thereprocase/dell-5560-wall-mount/docs/assets/after-fin.png

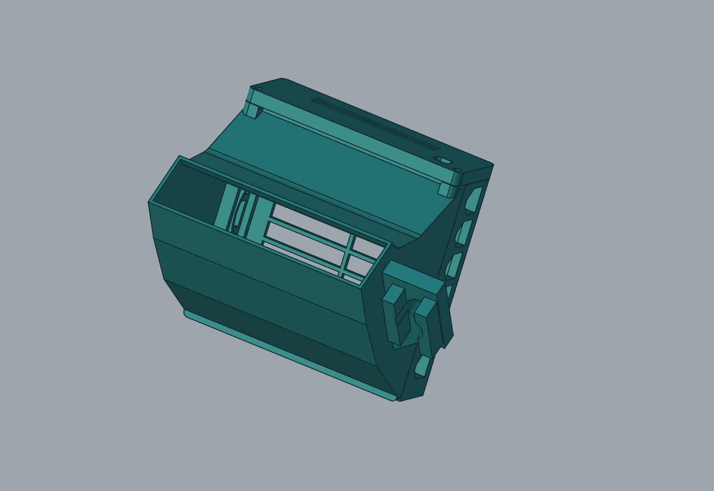
docs/assets/after-fin.png
