thereprocase/dell-5560-wall-mount/docs/assets/after-shoulder.png

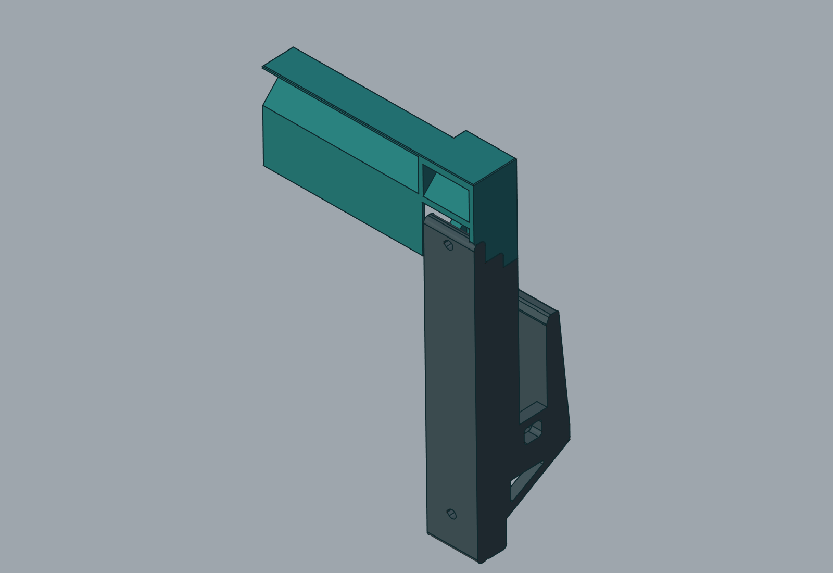
docs/assets/after-shoulder.png
