thereprocase/dell-5560-wall-mount/docs/assets/before-fin.png

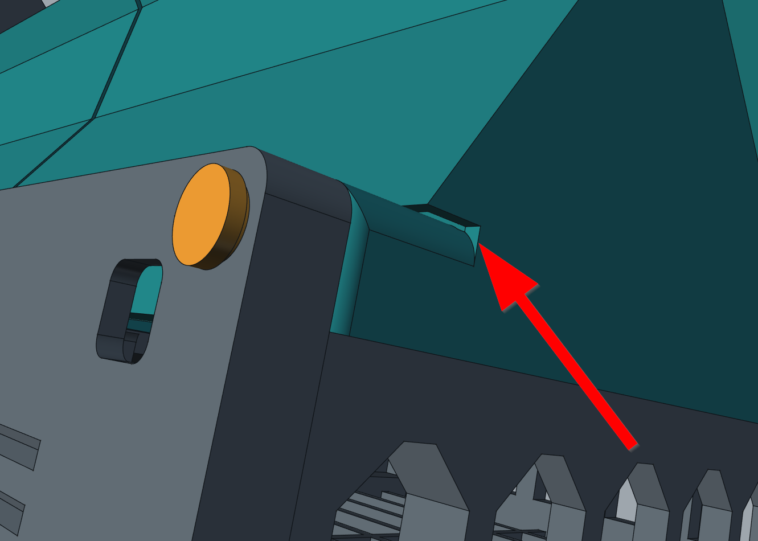
docs/assets/before-fin.png
