thereprocase/dell-5560-wall-mount/docs/assets/before-shoulder.png

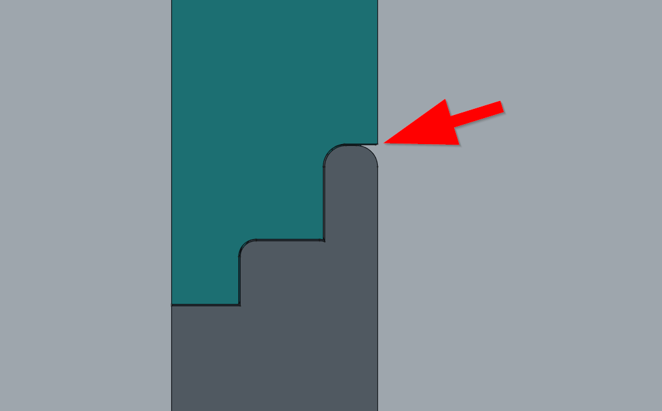
docs/assets/before-shoulder.png
