thereprocase/dell-5560-wall-mount/docs/assets/before-tray.png

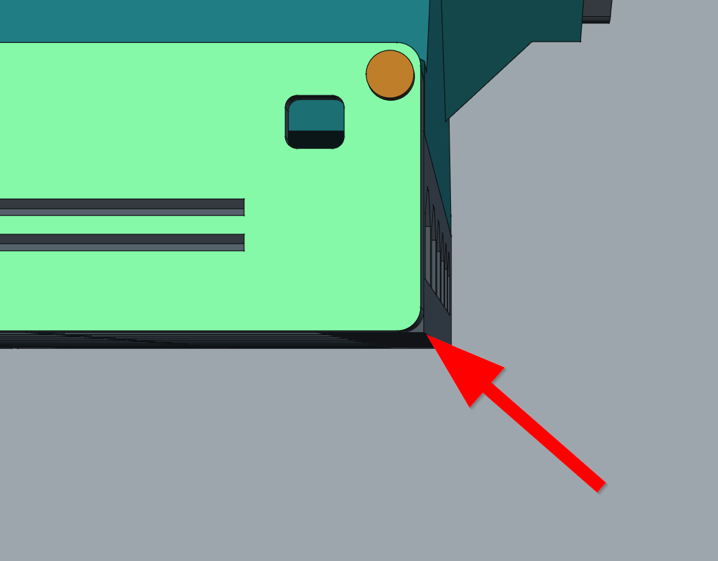
docs/assets/before-tray.png
