thereprocase/dell-5560-wall-mount/docs/assets/cap.png

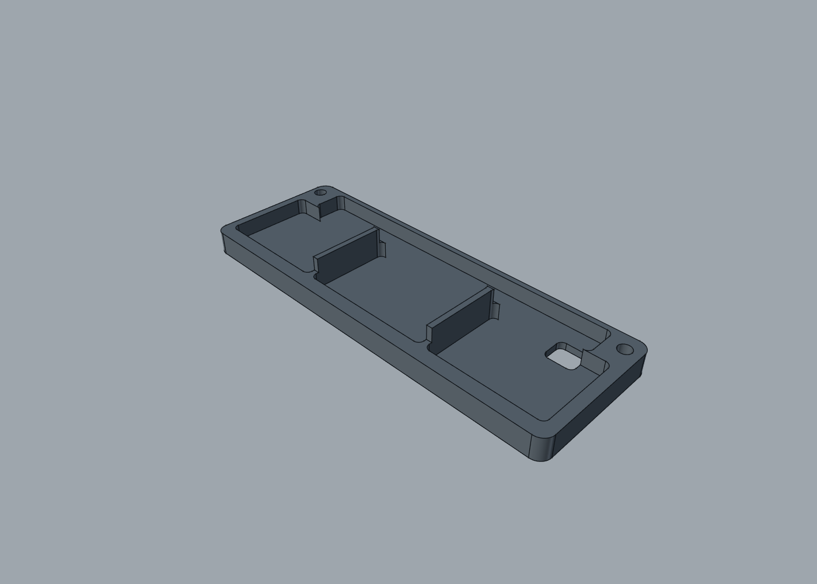
docs/assets/cap.png
