thereprocase/dell-5560-wall-mount/docs/assets/cfd-mesh.png

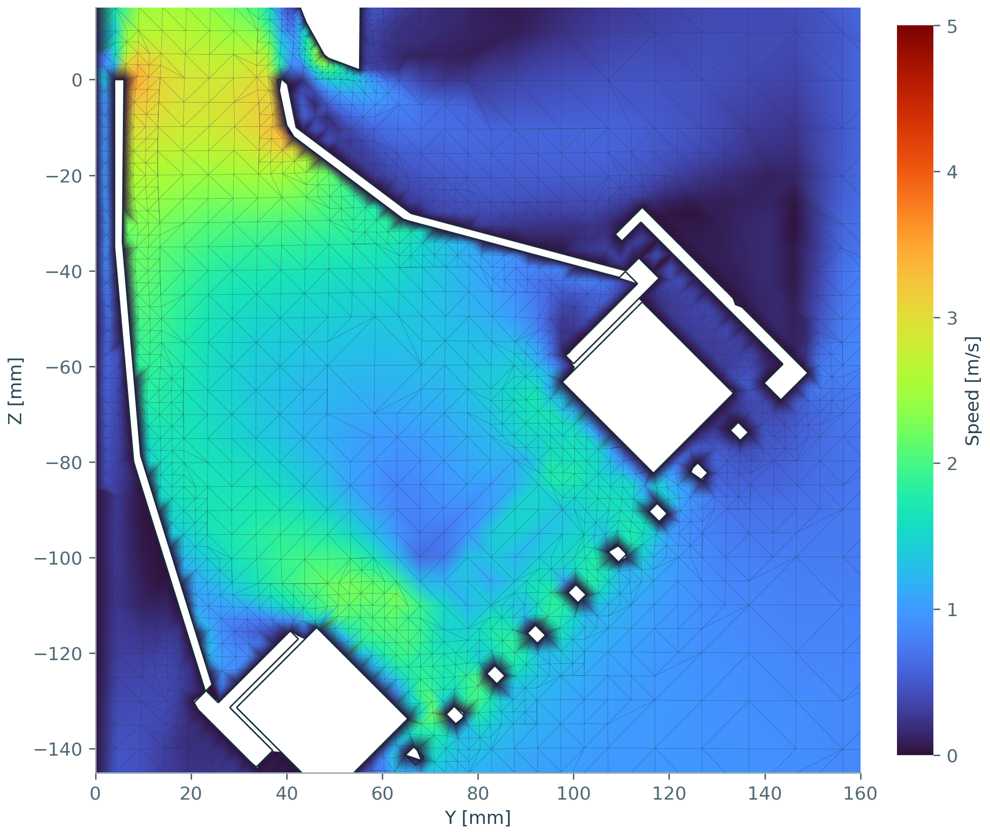
docs/assets/cfd-mesh.png
