thereprocase/dell-5560-wall-mount/docs/assets/cfd-pressure.png

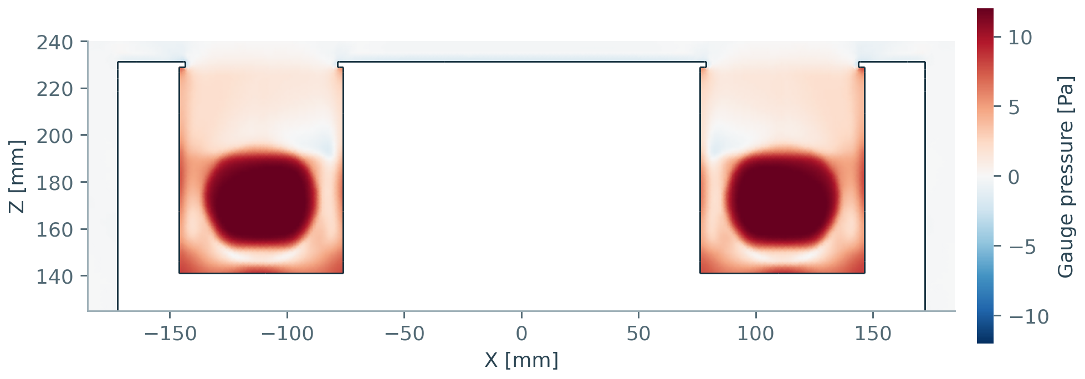
docs/assets/cfd-pressure.png
