thereprocase/dell-5560-wall-mount/docs/assets/cfd-residuals.png

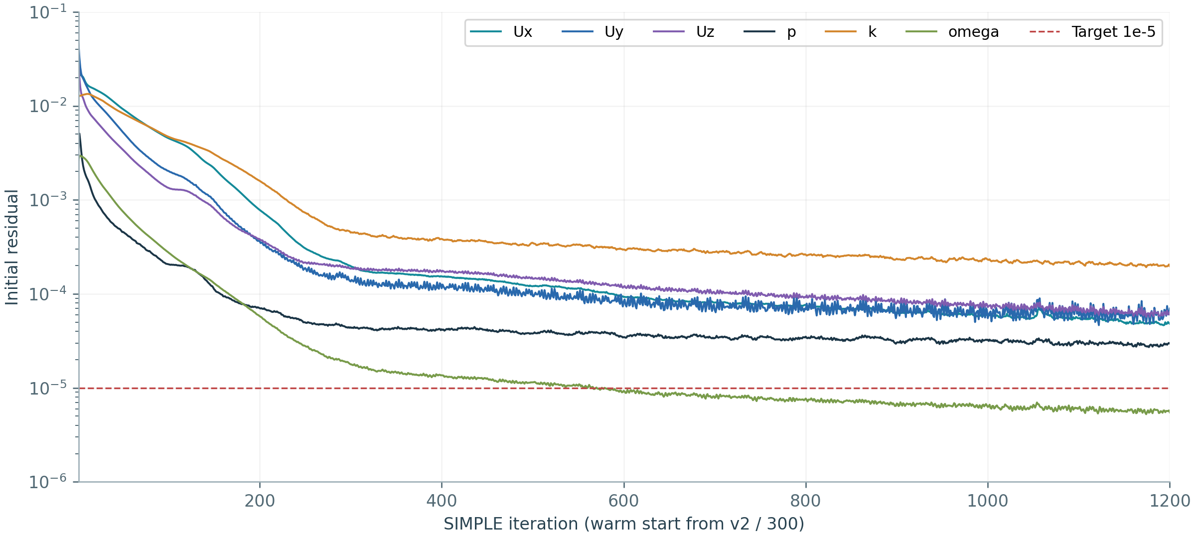
docs/assets/cfd-residuals.png
