thereprocase/dell-5560-wall-mount/docs/assets/cfd-speed.png

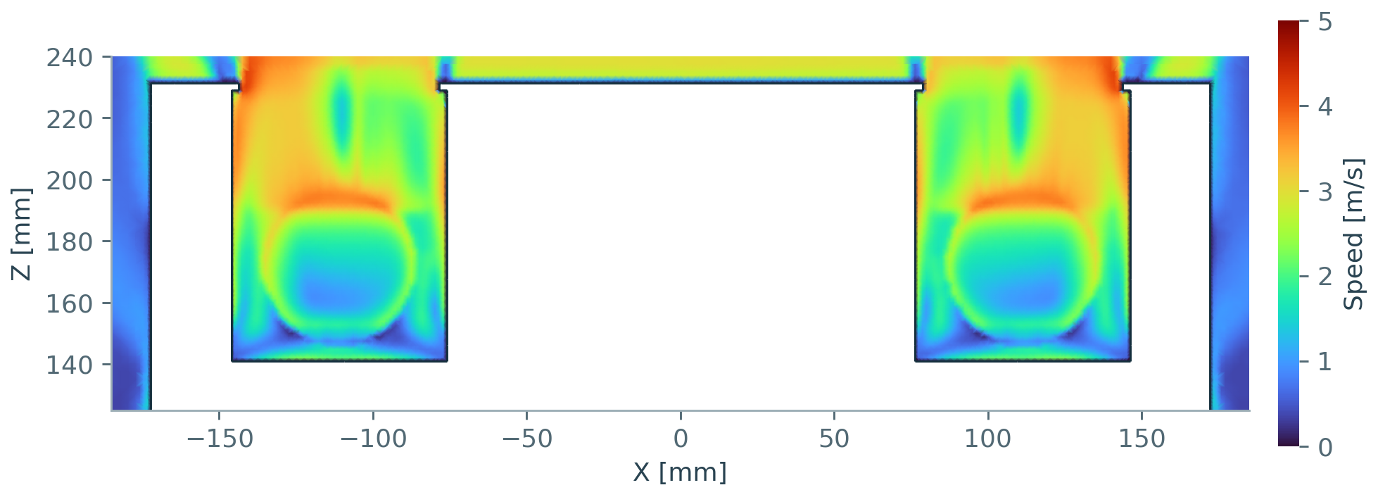
docs/assets/cfd-speed.png
