thereprocase/dell-5560-wall-mount/docs/assets/cfd-streamlines.png

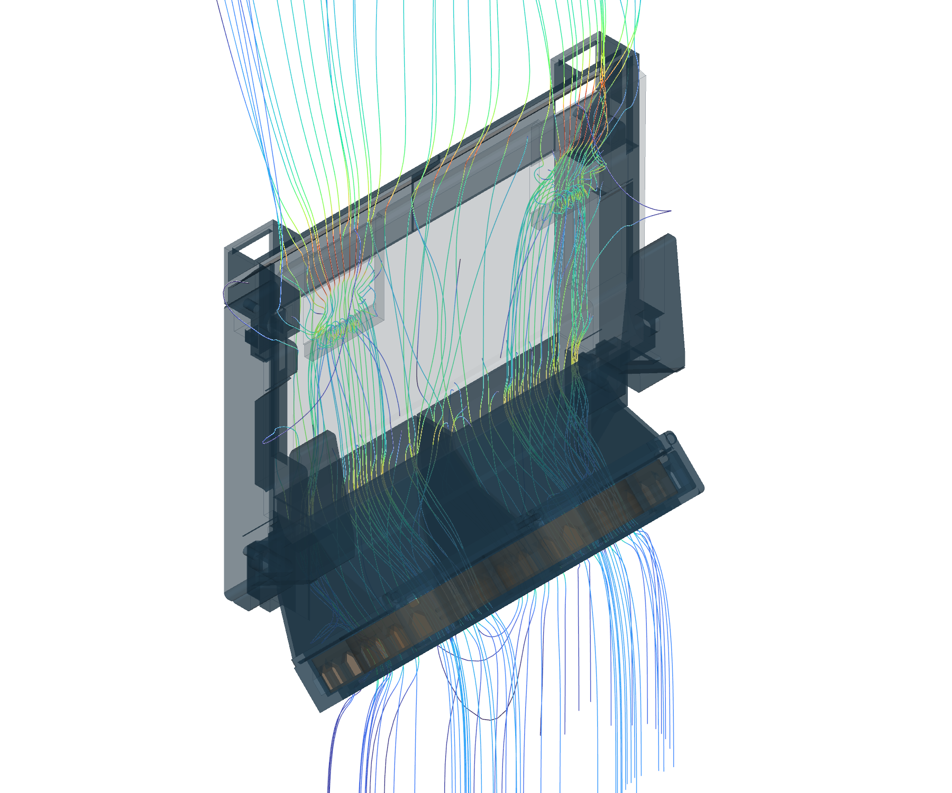
docs/assets/cfd-streamlines.png
