thereprocase/dell-5560-wall-mount/docs/assets/duct.png

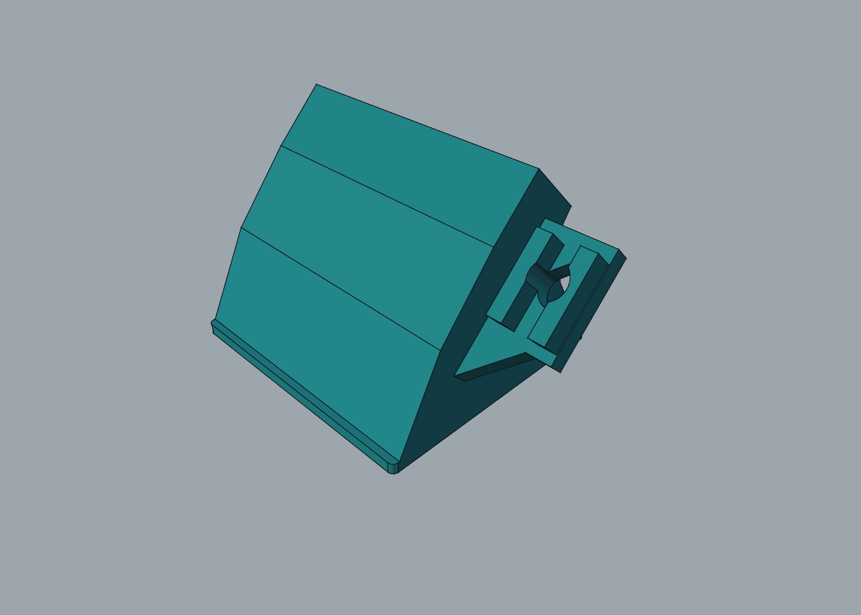
docs/assets/duct.png
