thereprocase/dell-5560-wall-mount/docs/assets/flow-refinement.png

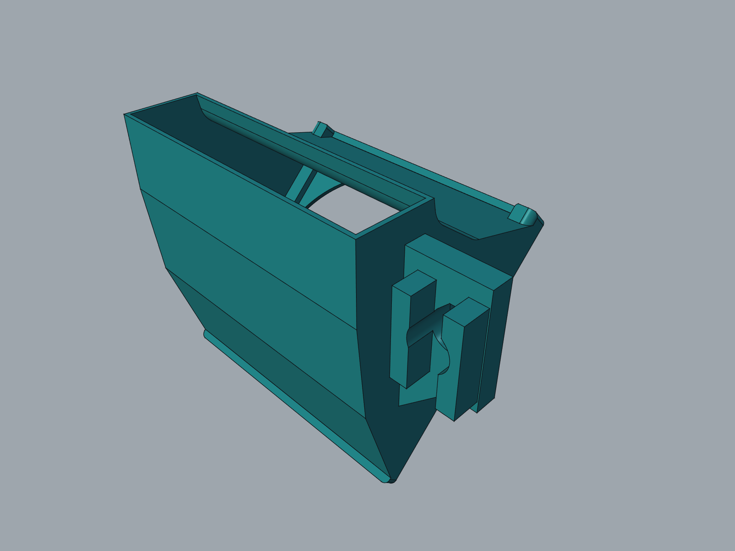
docs/assets/flow-refinement.png
