thereprocase/dell-5560-wall-mount/docs/assets/minimalist-cage-toolpaths.png

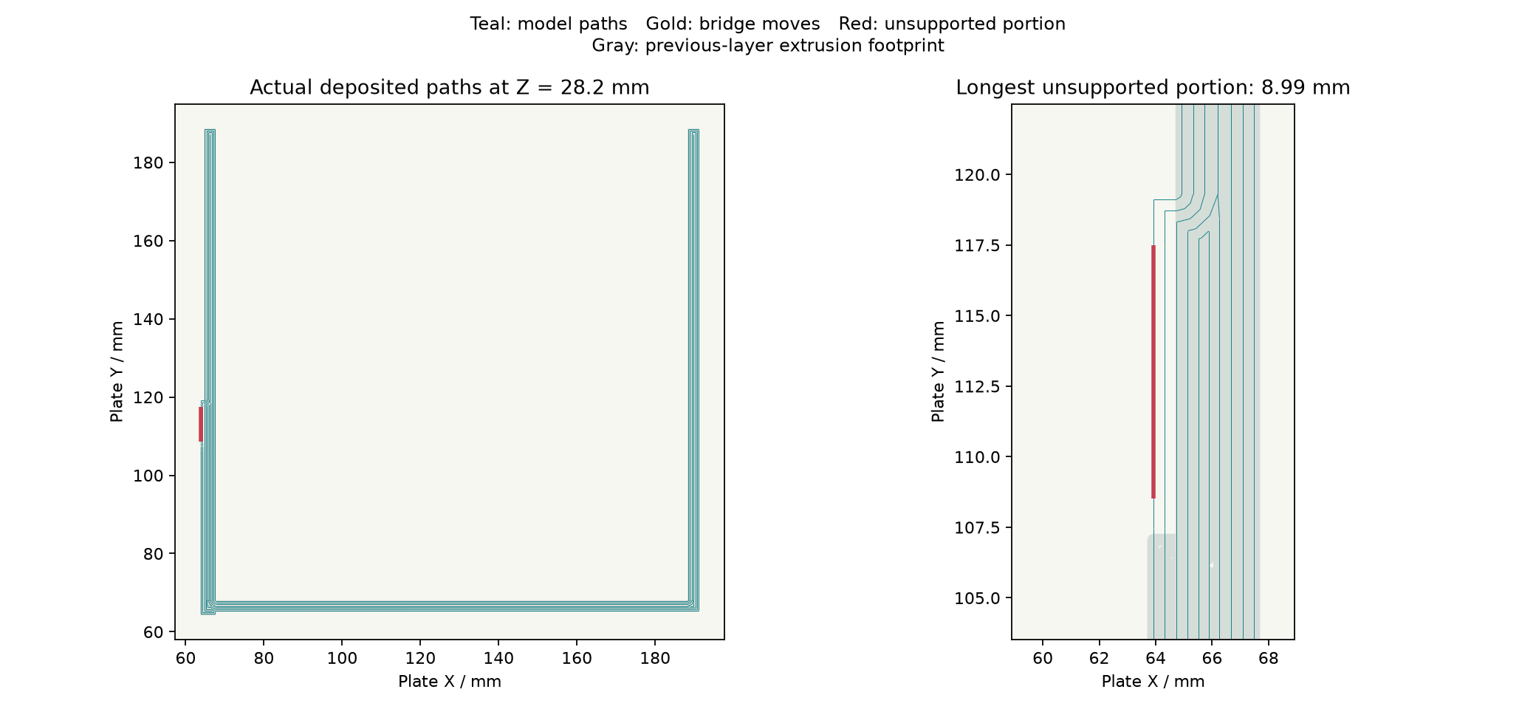
docs/assets/minimalist-cage-toolpaths.png
