thereprocase/dell-5560-wall-mount/docs/assets/minimalist-native.png

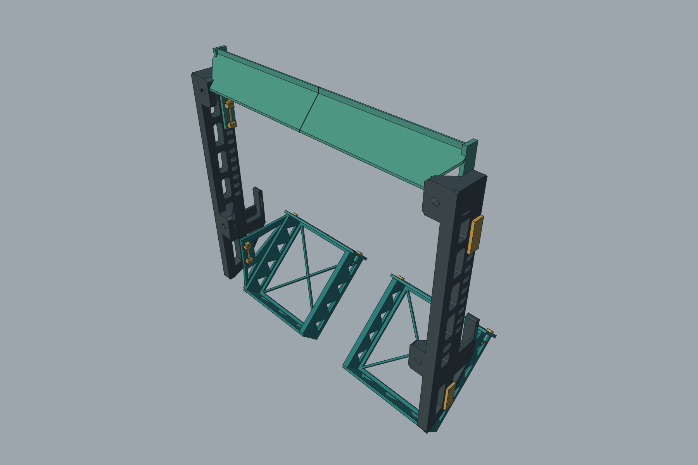
docs/assets/minimalist-native.png
