thereprocase/dell-5560-wall-mount/docs/assets/minimalist-with-envelopes.png

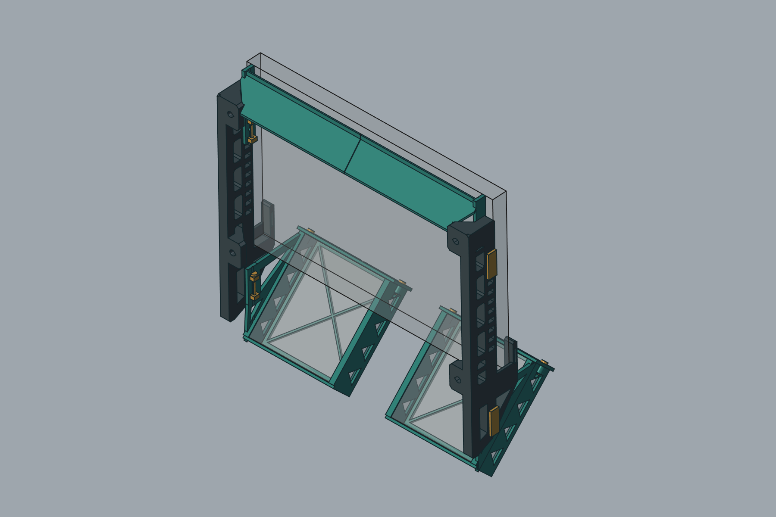
docs/assets/minimalist-with-envelopes.png
