thereprocase/dell-5560-wall-mount/docs/assets/parameters.png

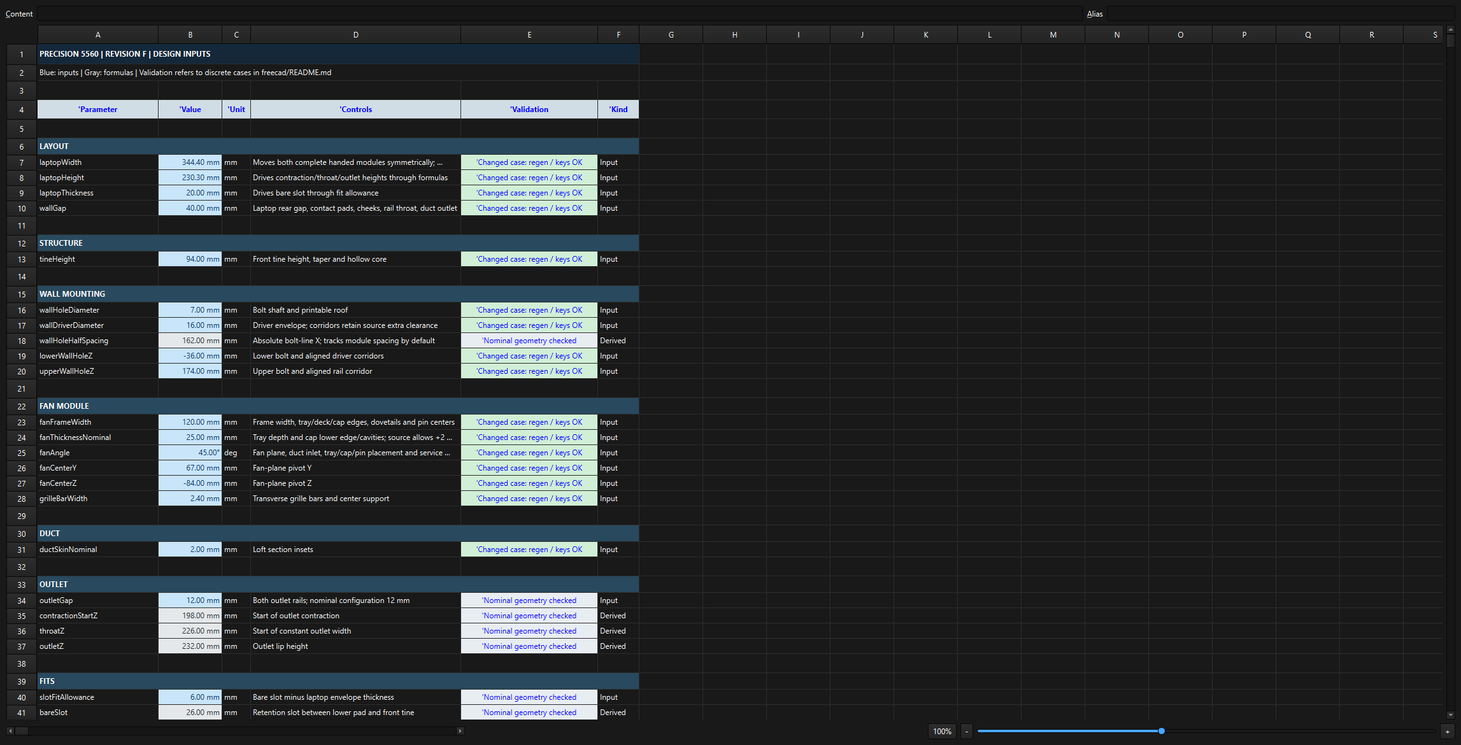
docs/assets/parameters.png
