thereprocase/dell-5560-wall-mount/docs/assets/pin.png

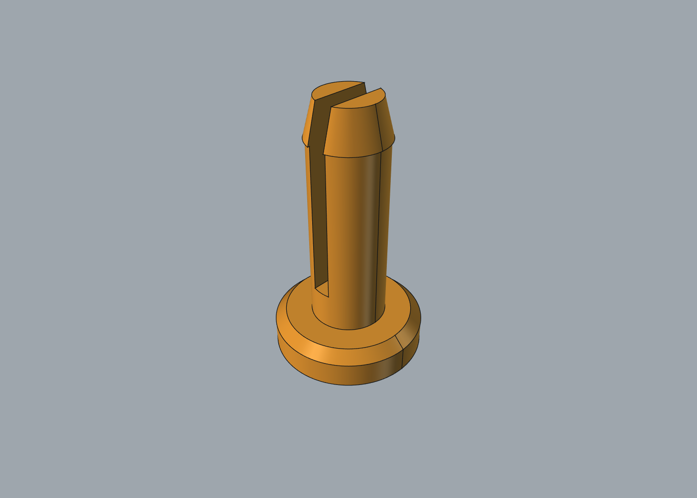
docs/assets/pin.png
