thereprocase/dell-5560-wall-mount/docs/assets/rail.png

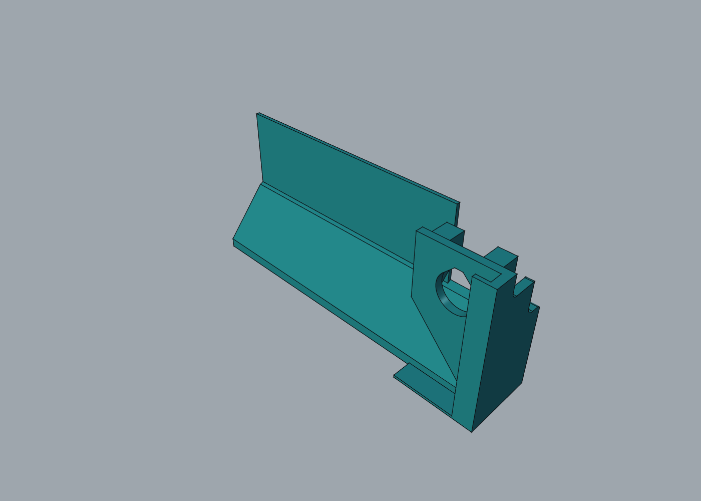
docs/assets/rail.png
