thereprocase/dell-5560-wall-mount/docs/assets/revh-cables-coupon.png

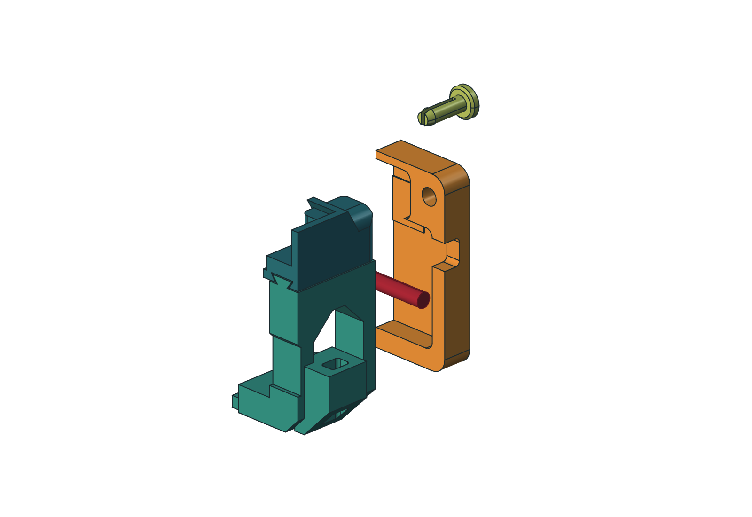
docs/assets/revh-cables-coupon.png
