thereprocase/dell-5560-wall-mount/docs/assets/revh-cables-toolpaths.png

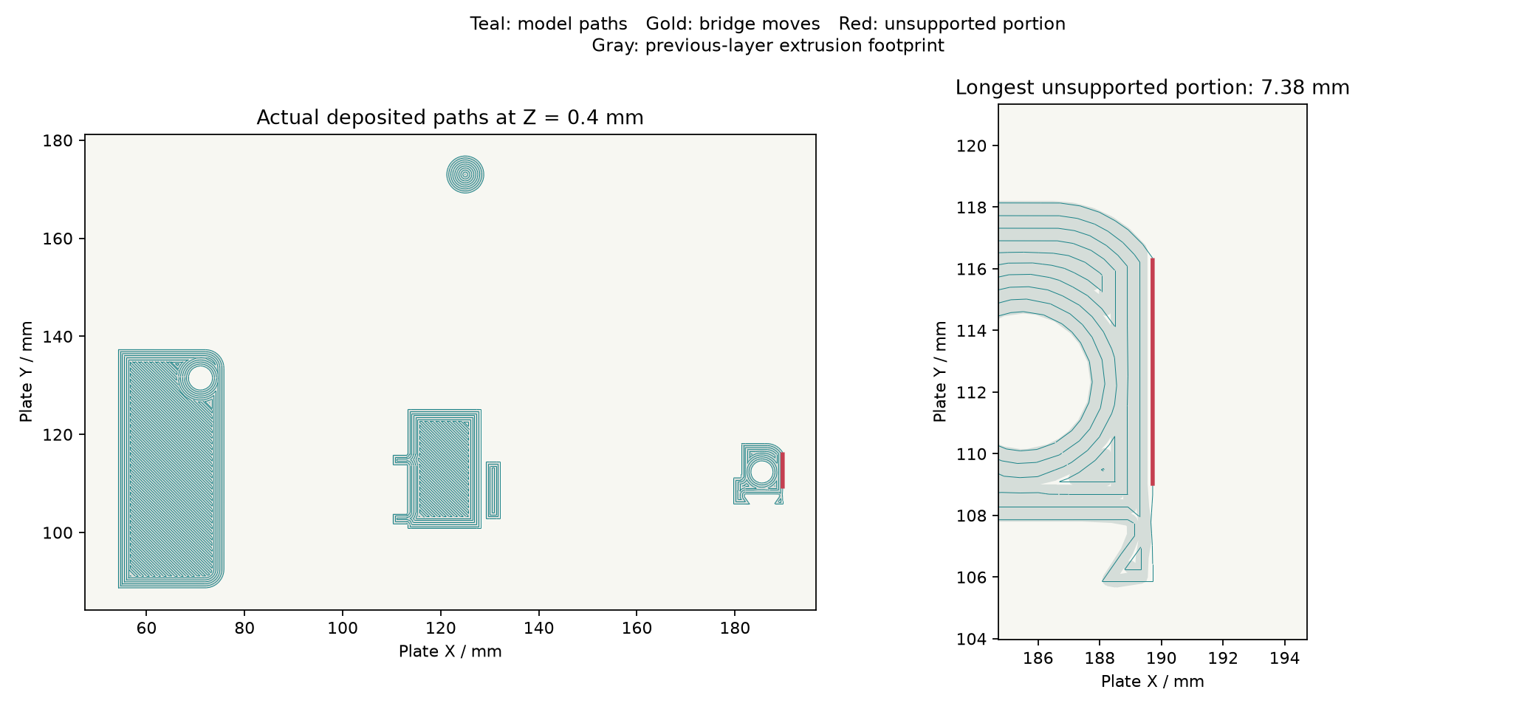
docs/assets/revh-cables-toolpaths.png
