thereprocase/dell-5560-wall-mount/docs/assets/revh-cables-tray.png

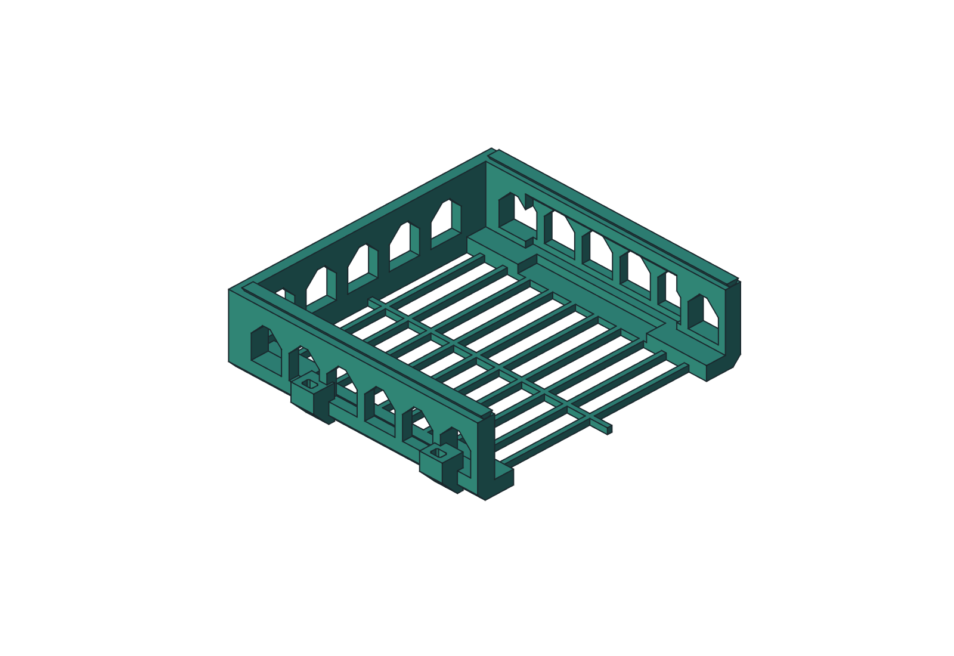
docs/assets/revh-cables-tray.png
