thereprocase/dell-5560-wall-mount/docs/assets/revh-duct-d4-pin-hole-obstruction.png

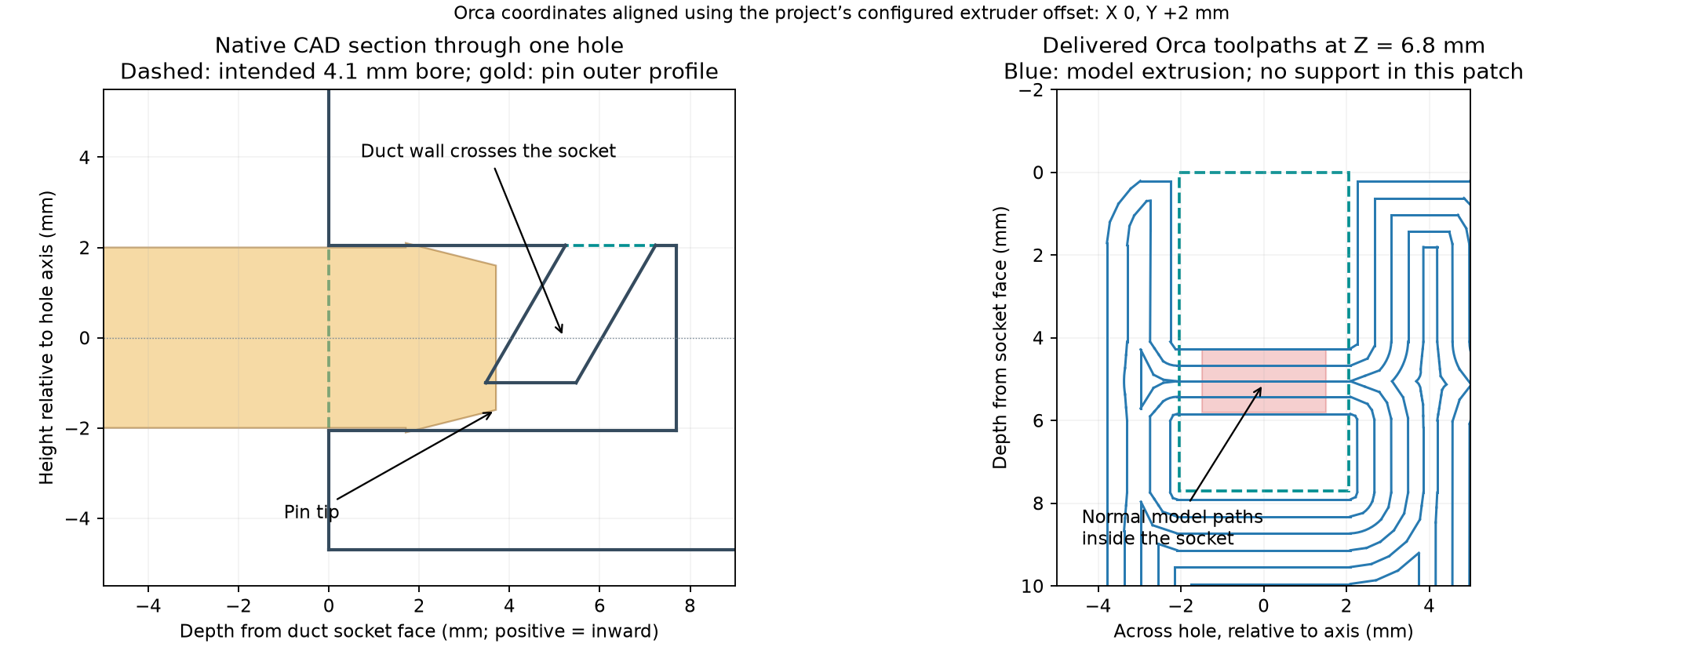
docs/assets/revh-duct-d4-pin-hole-obstruction.png
