thereprocase/dell-5560-wall-mount/docs/assets/revh-duct-d4-socket-before-after.png

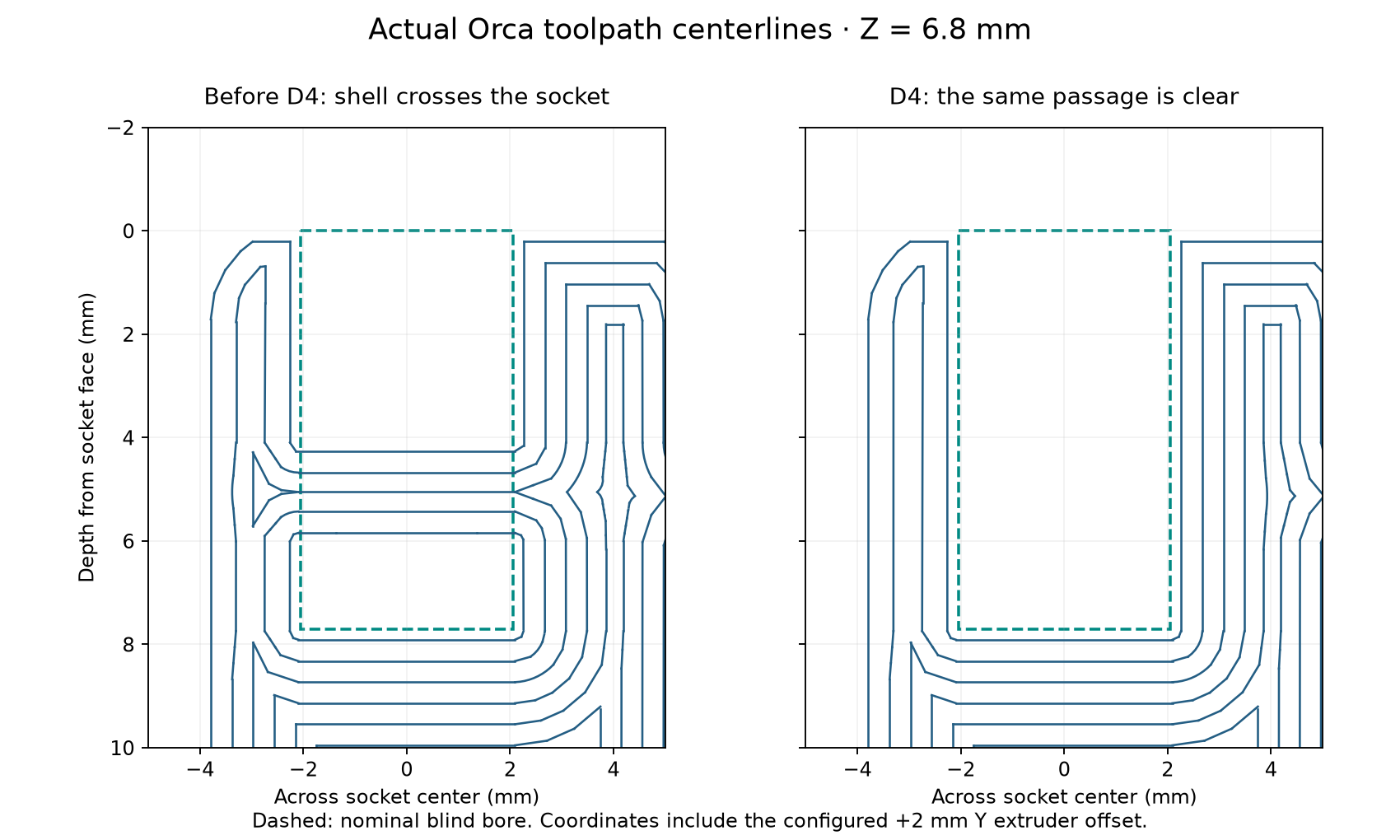
docs/assets/revh-duct-d4-socket-before-after.png
