thereprocase/dell-5560-wall-mount/docs/assets/revh-orca-left-cross-slot-audit.png

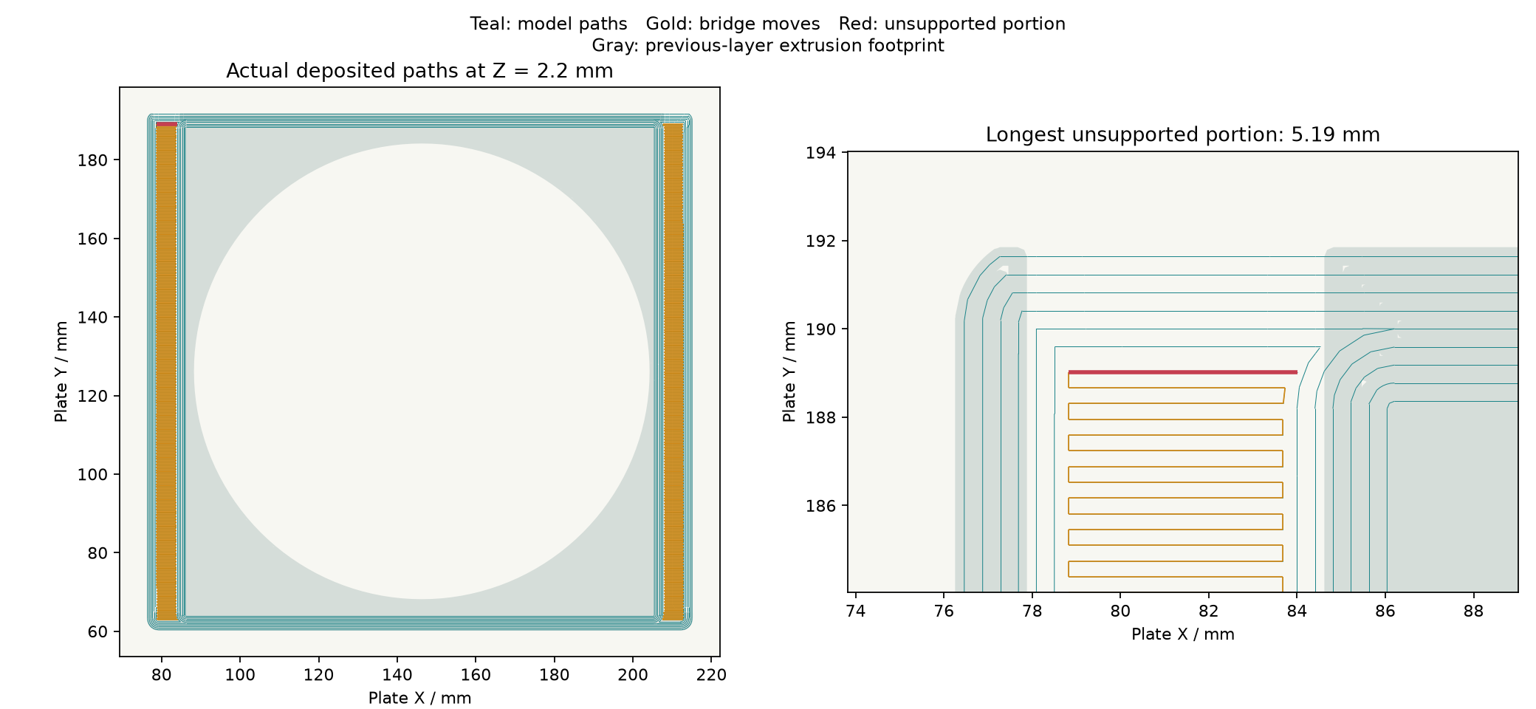
docs/assets/revh-orca-left-cross-slot-audit.png
