thereprocase/dell-5560-wall-mount/docs/assets/revh-retainers-lower.png

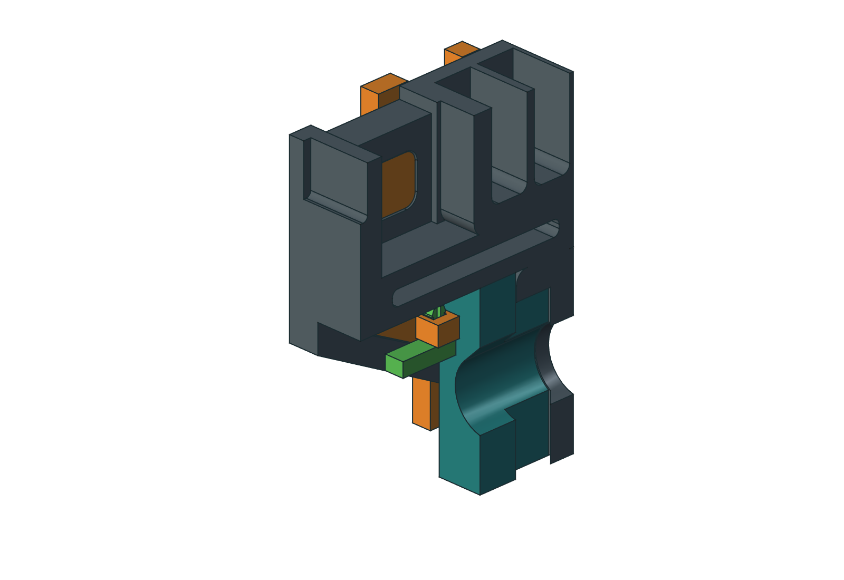
docs/assets/revh-retainers-lower.png
