thereprocase/dell-5560-wall-mount/docs/assets/revh-retainers-removed.png

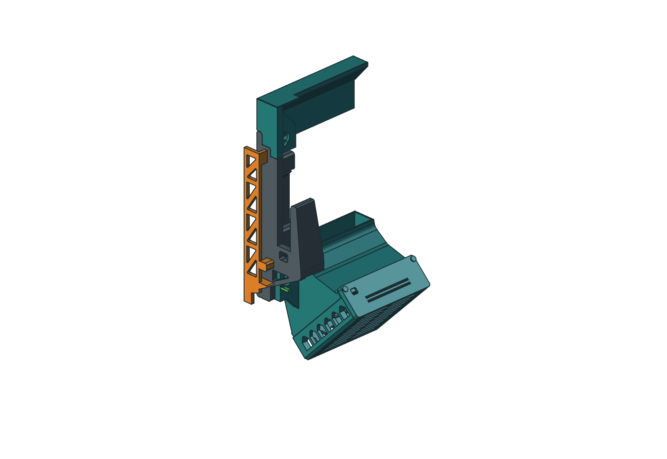
docs/assets/revh-retainers-removed.png
