thereprocase/dell-5560-wall-mount/docs/assets/revh-retainers-toolpaths.png

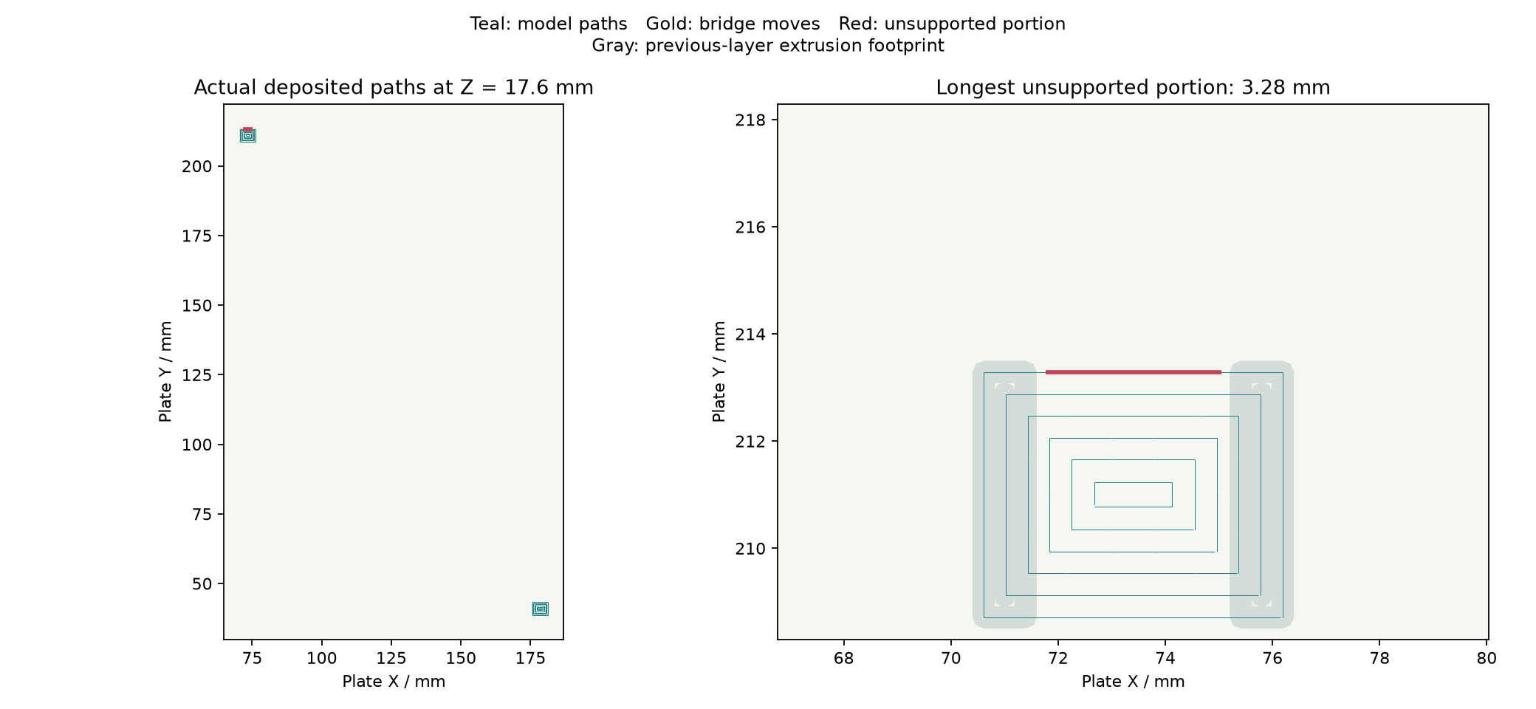
docs/assets/revh-retainers-toolpaths.png
