thereprocase/dell-5560-wall-mount/docs/assets/revh-retainers-upper.png

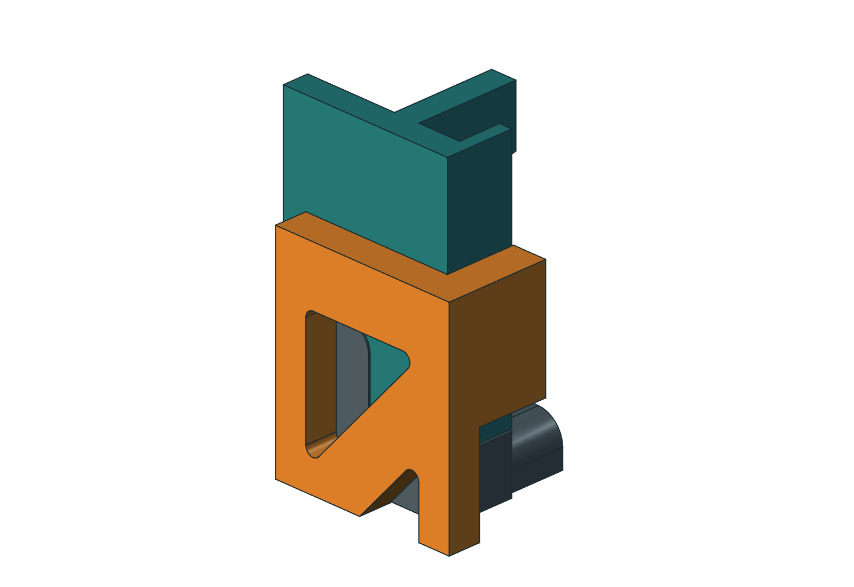
docs/assets/revh-retainers-upper.png
