thereprocase/dell-5560-wall-mount/docs/assets/tray.png

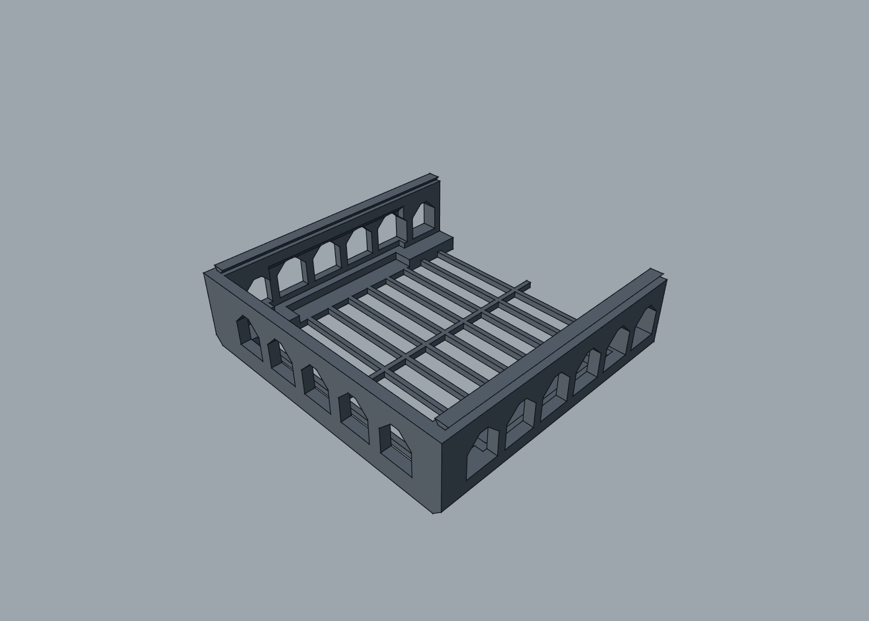
docs/assets/tray.png
