thereprocase/dell-5560-wall-mount/docs/assets/wall-patch.png

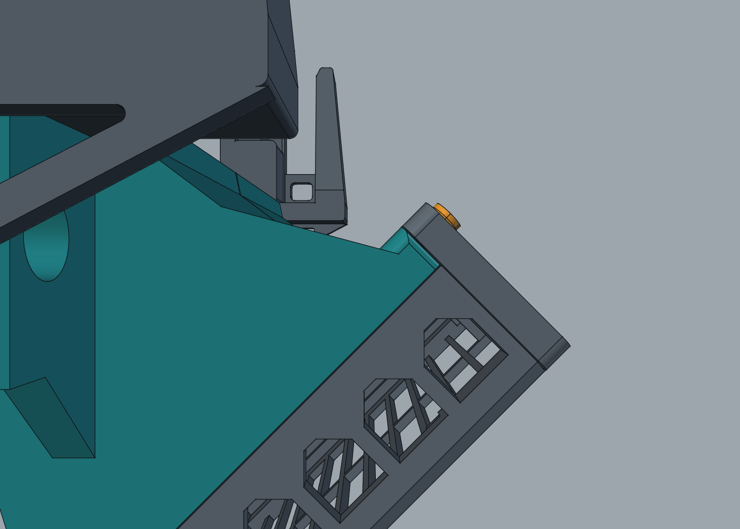
docs/assets/wall-patch.png
