thereprocase/dell-5560-wall-mount/docs/simulation/revh-transient/mesh-duct-overview.png

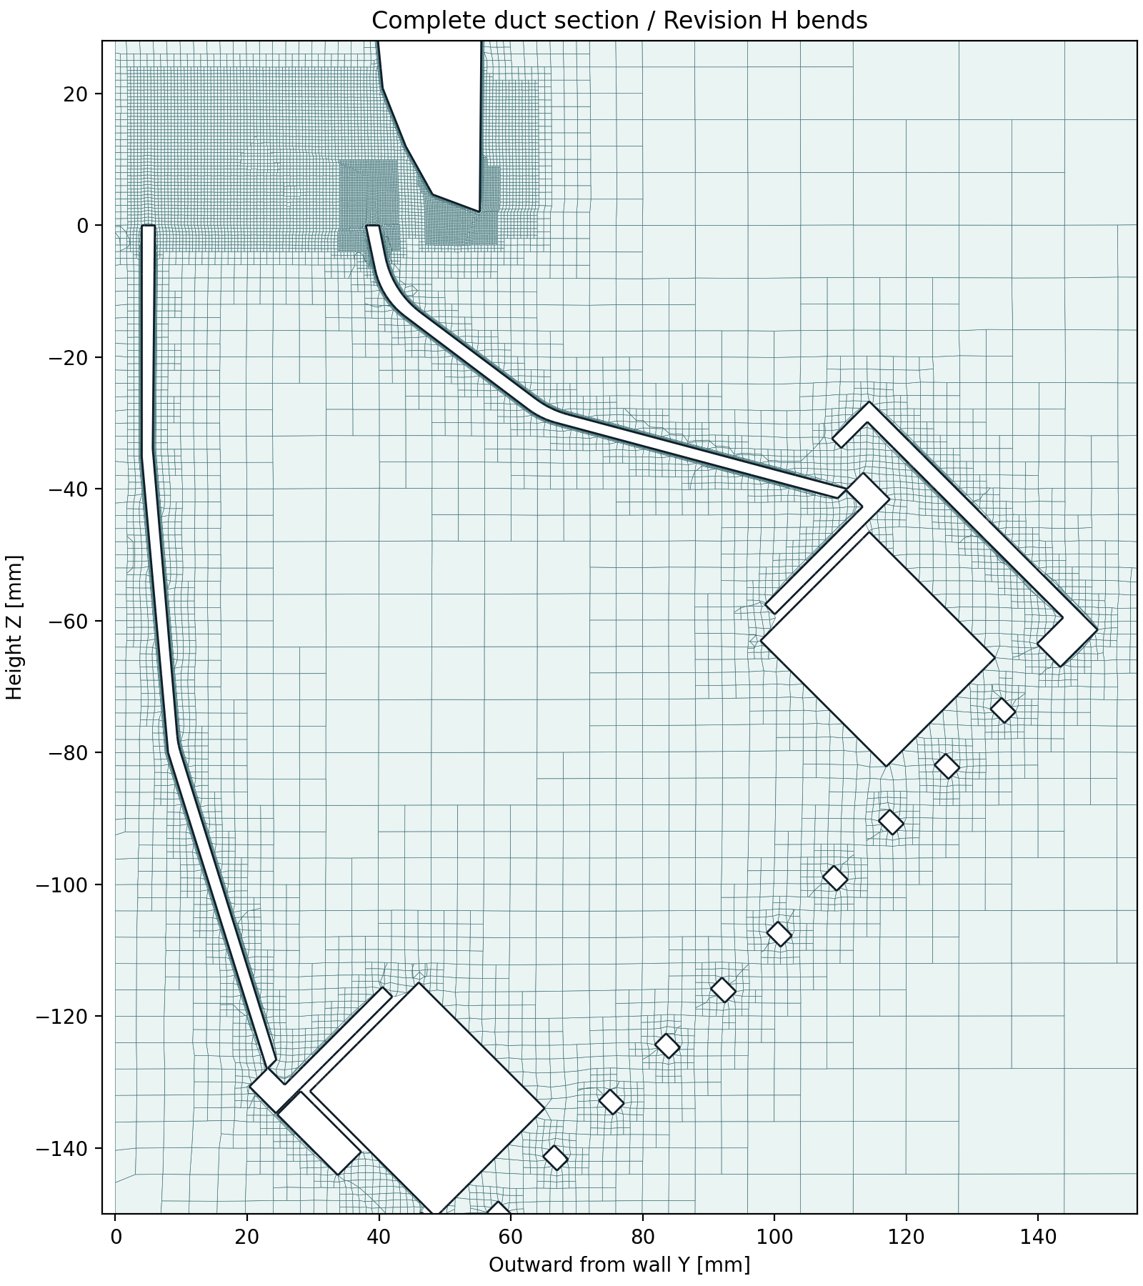
docs/simulation/revh-transient/mesh-duct-overview.png
