thereprocase/dell-5560-wall-mount/docs/simulation/revh-transient/pilot-sections-poster.png

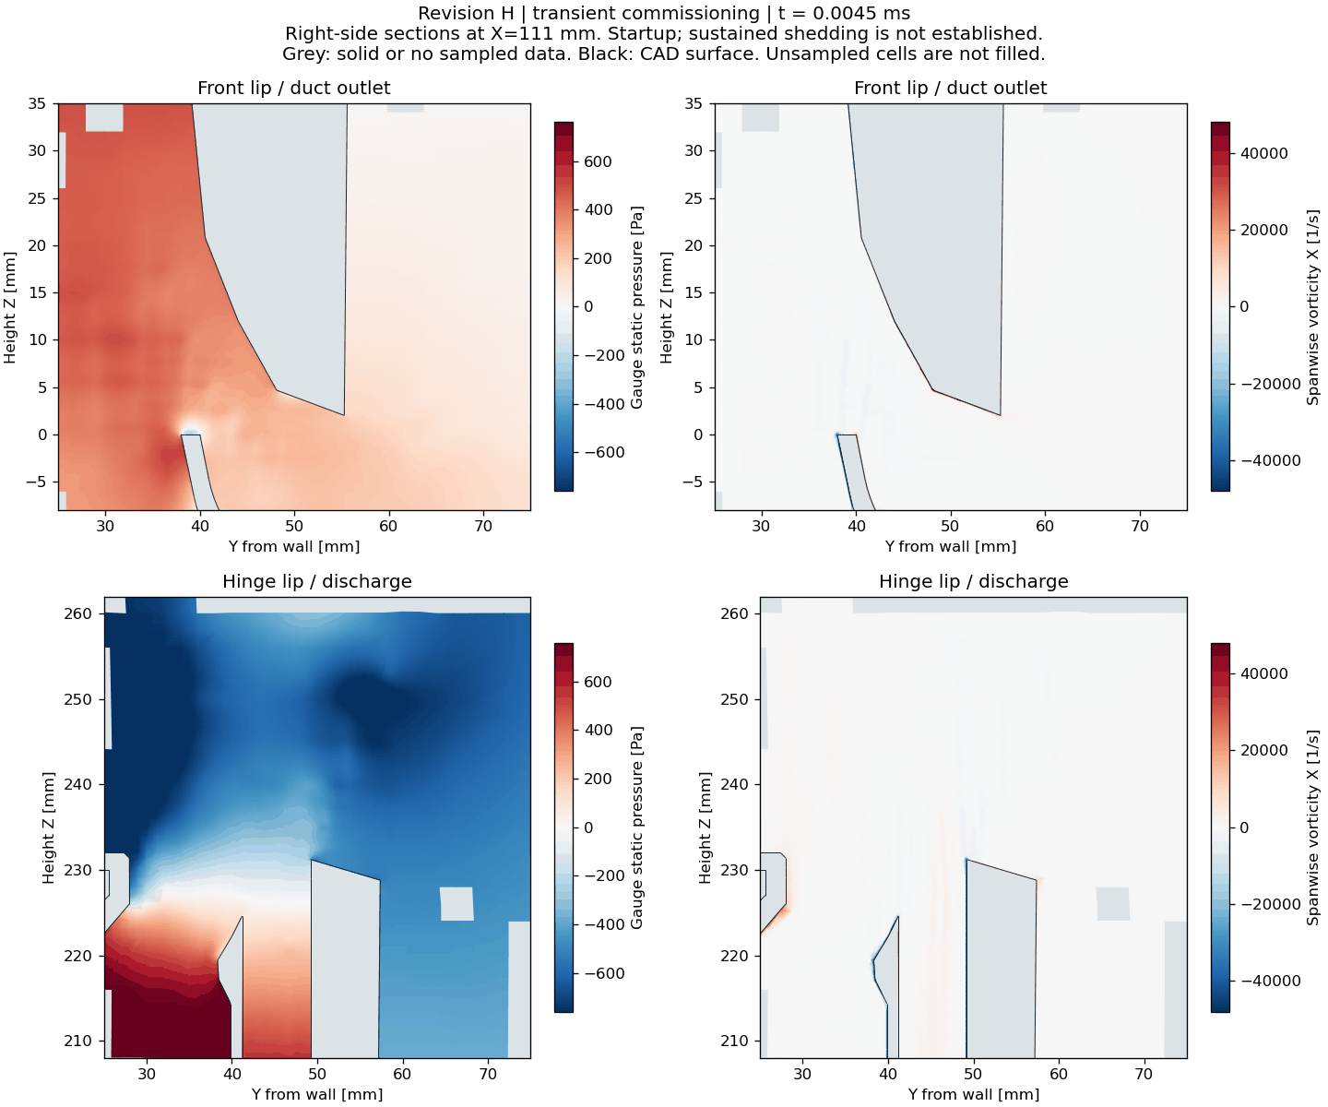
docs/simulation/revh-transient/pilot-sections-poster.png
