thereprocase/dell-5560-wall-mount/docs/simulation/revh-transient/section-locator.png

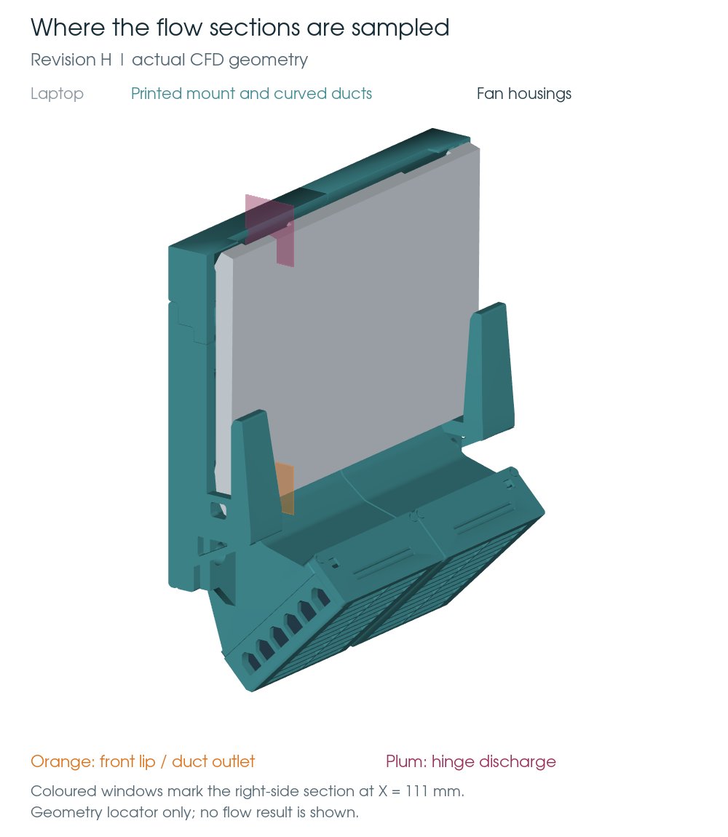
docs/simulation/revh-transient/section-locator.png
