thereprocase/dell-5560-wall-mount/docs/simulation/revh-transient/sequence/checkpoint-01/first-frame.png

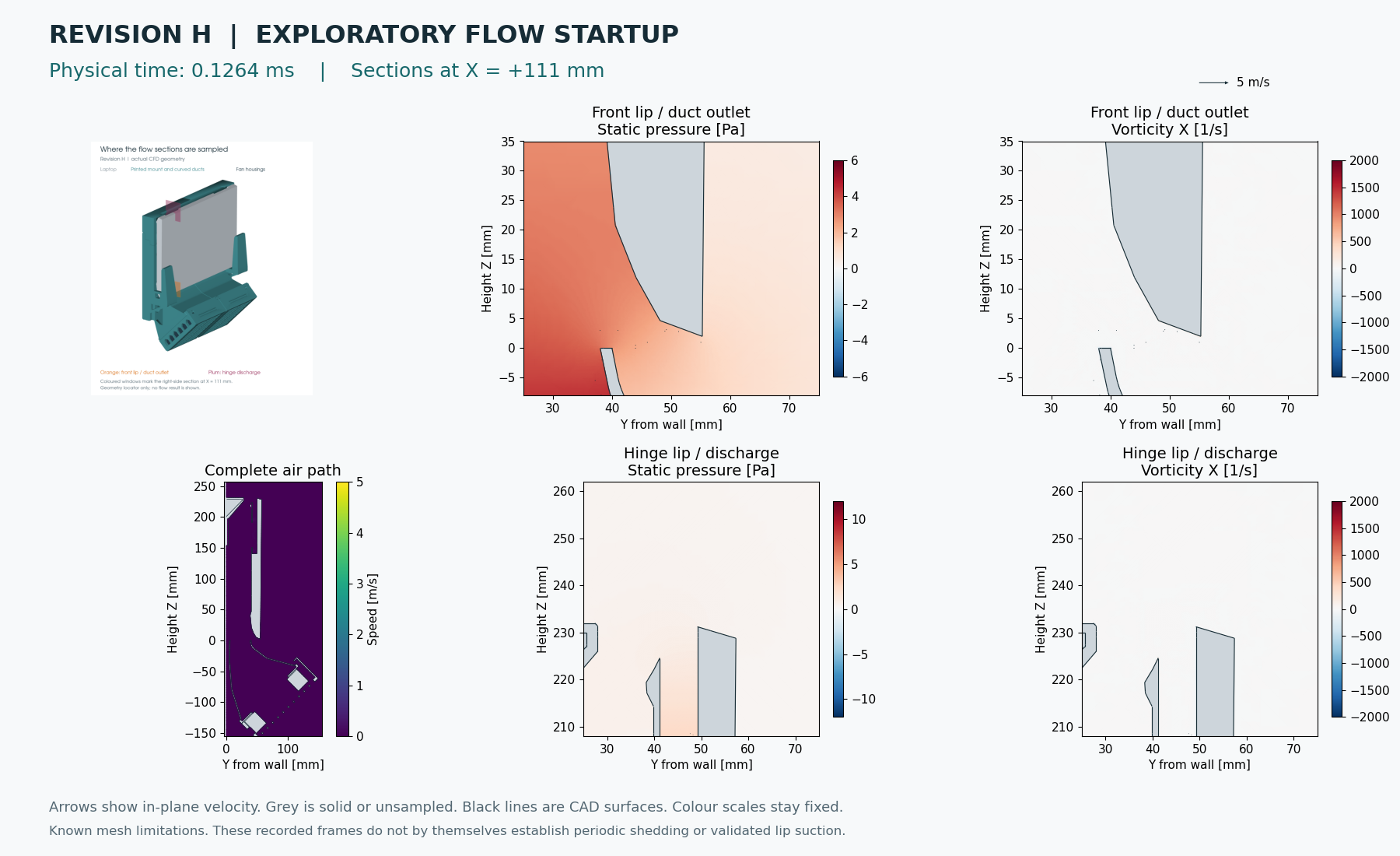
docs/simulation/revh-transient/sequence/checkpoint-01/first-frame.png
