thereprocase/dell-5560-wall-mount/docs/simulation/revh-transient/sequence/checkpoint-03/poster.png

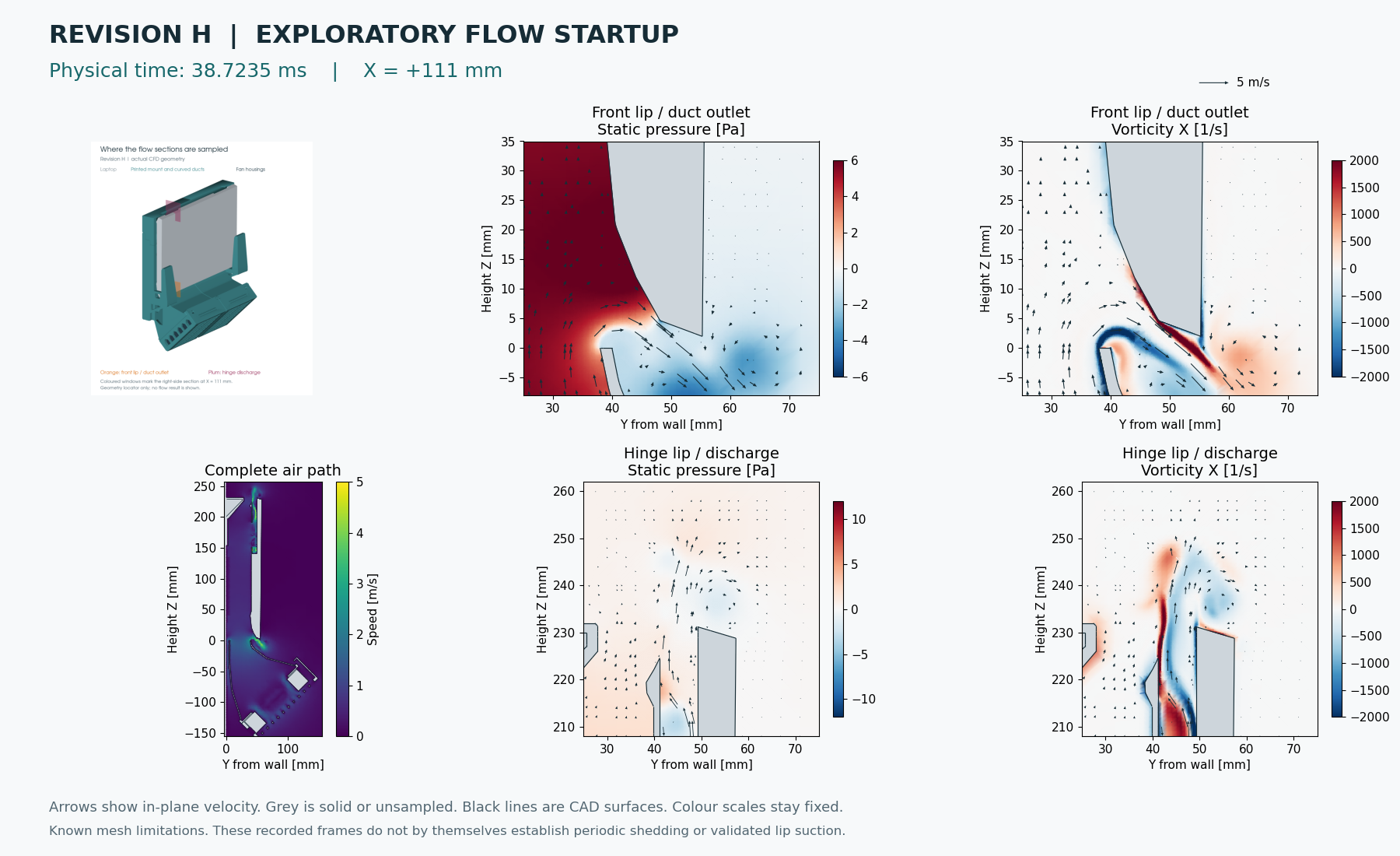
docs/simulation/revh-transient/sequence/checkpoint-03/poster.png
