thereprocase/dell-5560-wall-mount/docs/simulation/revh-transient/sequence/final/flowing/vorticity-arrows.png

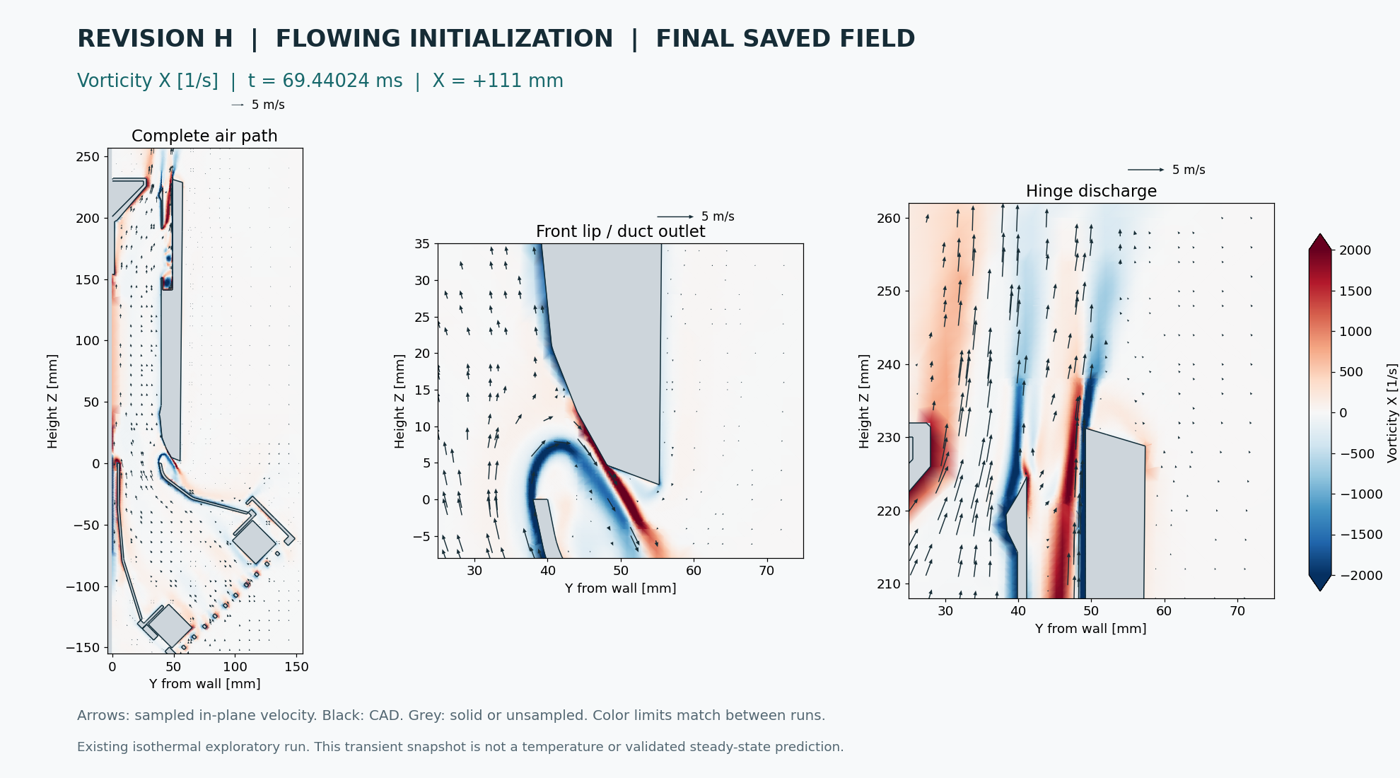
docs/simulation/revh-transient/sequence/final/flowing/vorticity-arrows.png
