thereprocase/dell-5560-wall-mount/docs/simulation/revh-transient/sequence/final/startup/speed-arrows.png

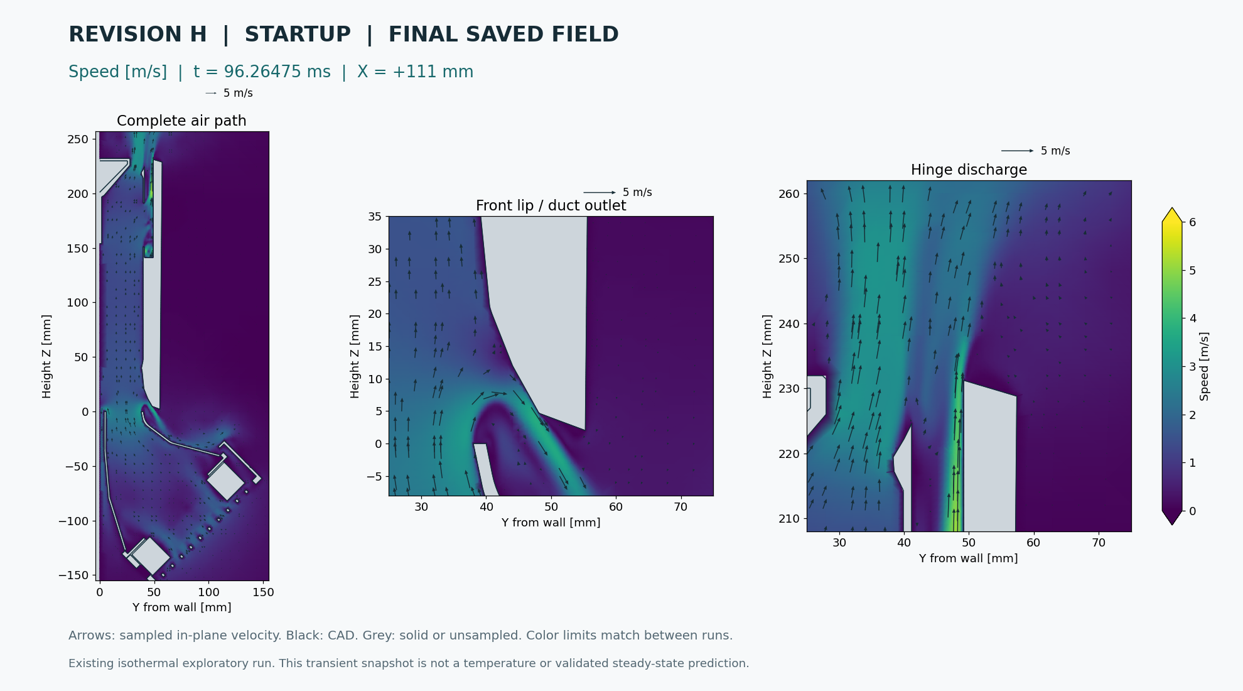
docs/simulation/revh-transient/sequence/final/startup/speed-arrows.png
