thereprocase/dell-5560-wall-mount/docs/simulation/revh-transient/sequence/flowing/latest-tracers.png

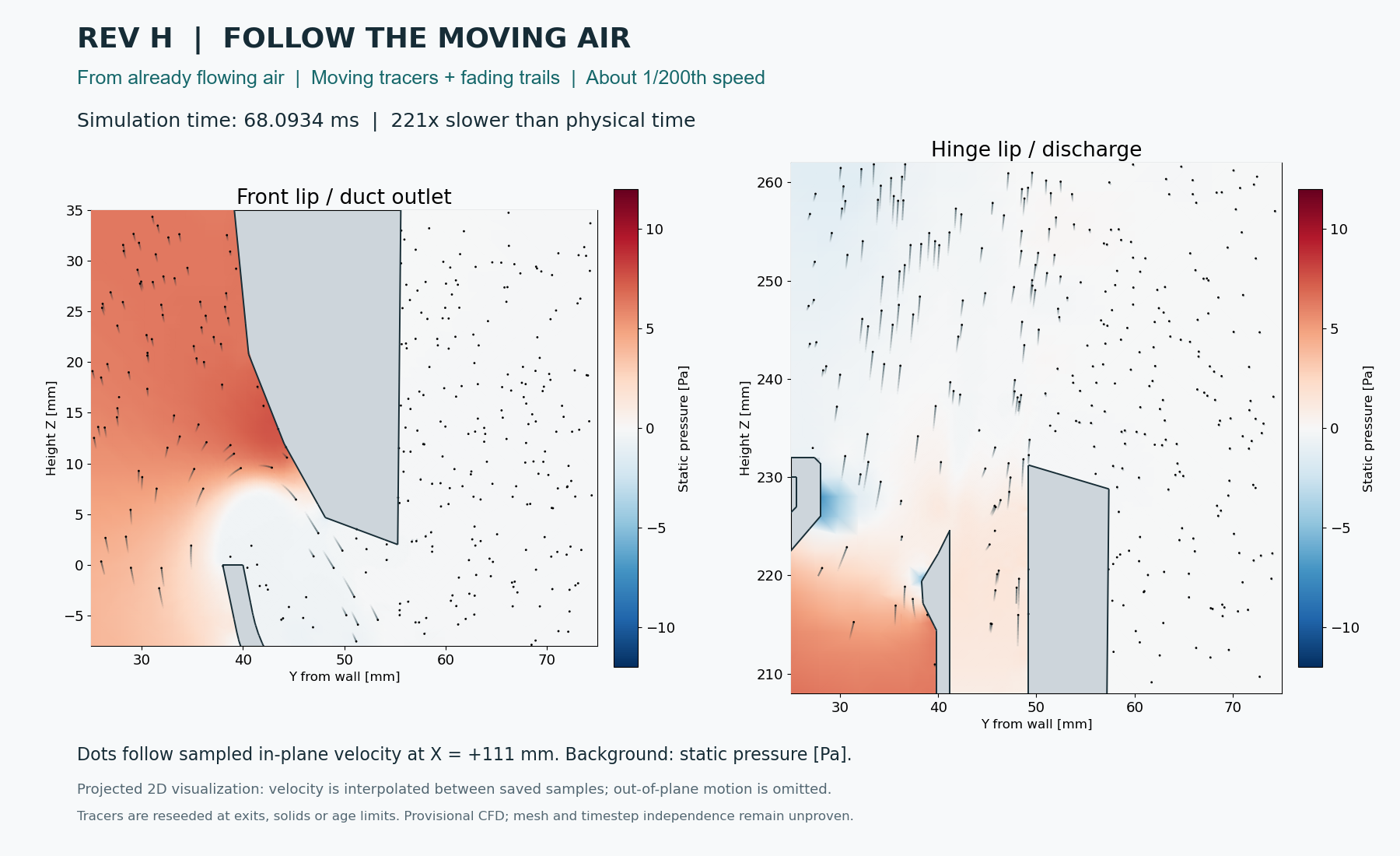
docs/simulation/revh-transient/sequence/flowing/latest-tracers.png
