thereprocase/dell-5560-wall-mount/docs/simulation/revh-transient/sequence/flowing/opening-flow-0.001546810911/opening-flow.png

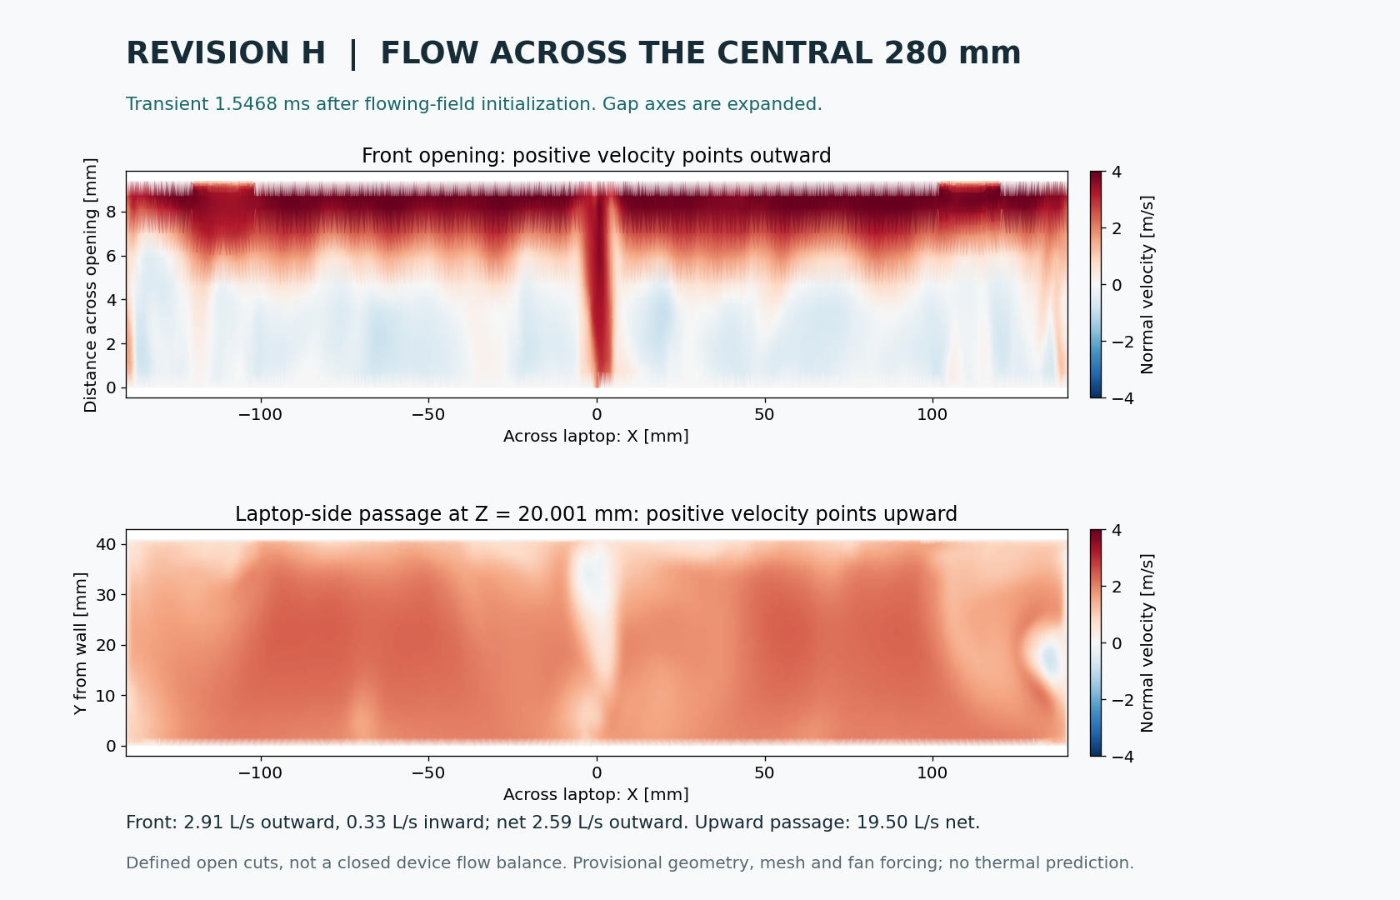
docs/simulation/revh-transient/sequence/flowing/opening-flow-0.001546810911/opening-flow.png
