thereprocase/dell-5560-wall-mount/docs/simulation/revh-transient/sequence/hour-7/poster.png

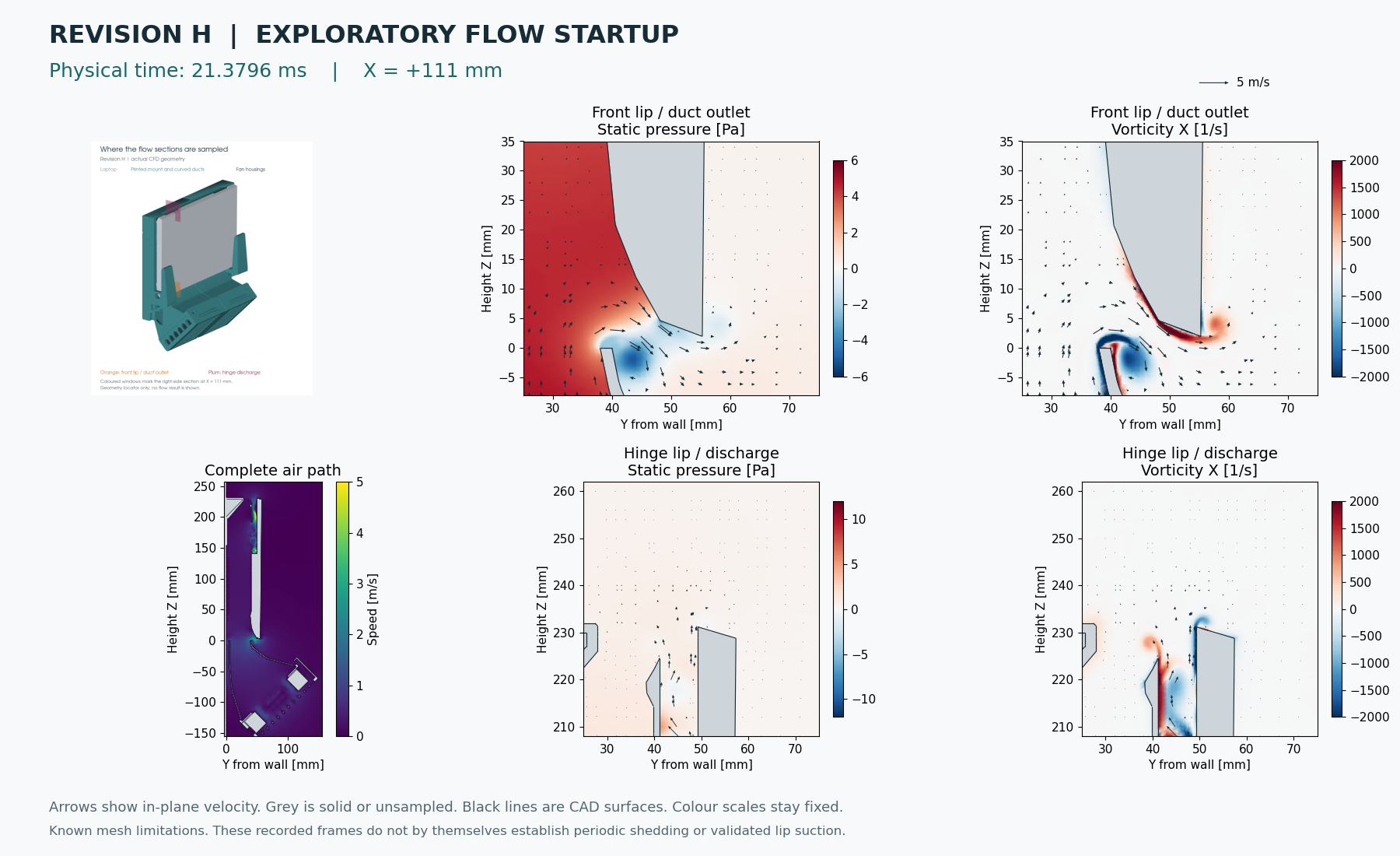
docs/simulation/revh-transient/sequence/hour-7/poster.png
