thereprocase/dell-5560-wall-mount/docs/simulation/revh-transient/sequence/latest-tracers.png

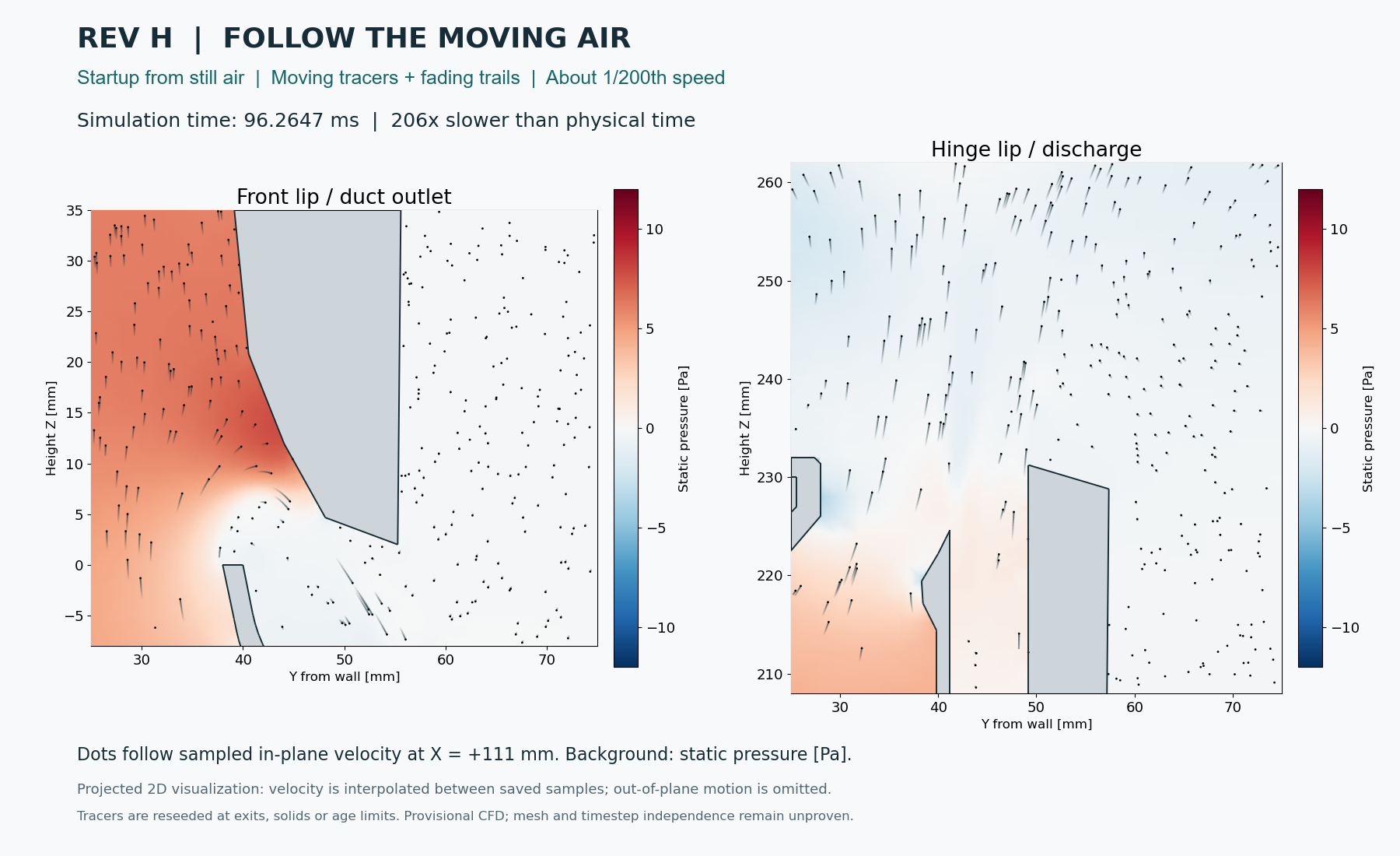
docs/simulation/revh-transient/sequence/latest-tracers.png
