thereprocase/dell-5560-wall-mount/docs/simulation/revh-transient/sequence/steady/iteration-400/vorticity-arrows.png

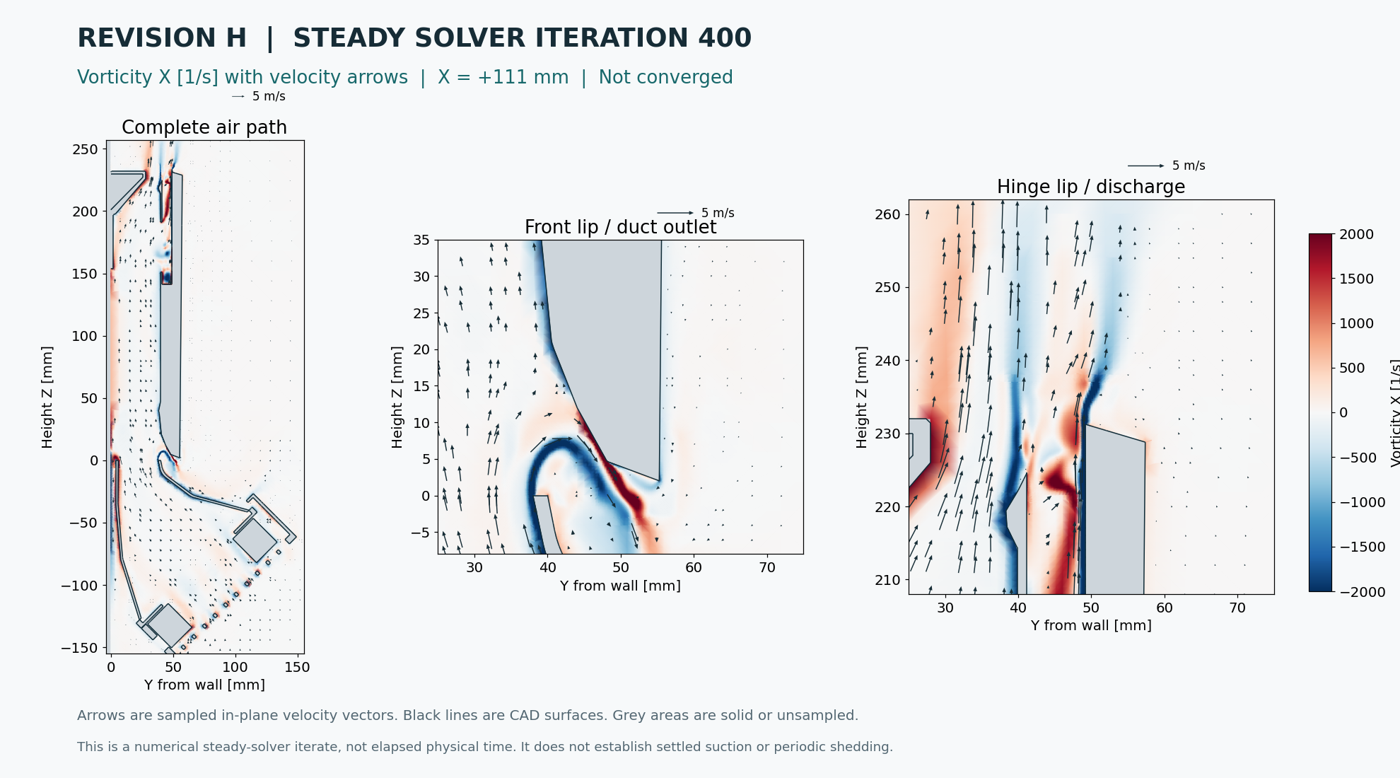
docs/simulation/revh-transient/sequence/steady/iteration-400/vorticity-arrows.png
