thereprocase/dell-5560-wall-mount/freecad/boss_runout_live.png

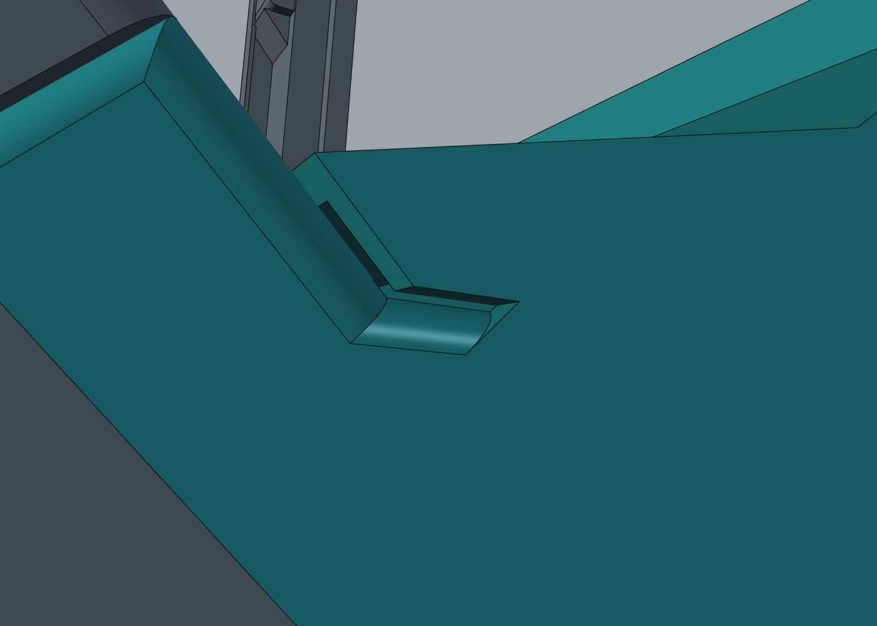
freecad/boss_runout_live.png
