thereprocase/dell-5560-wall-mount/freecad/cel_preview.png

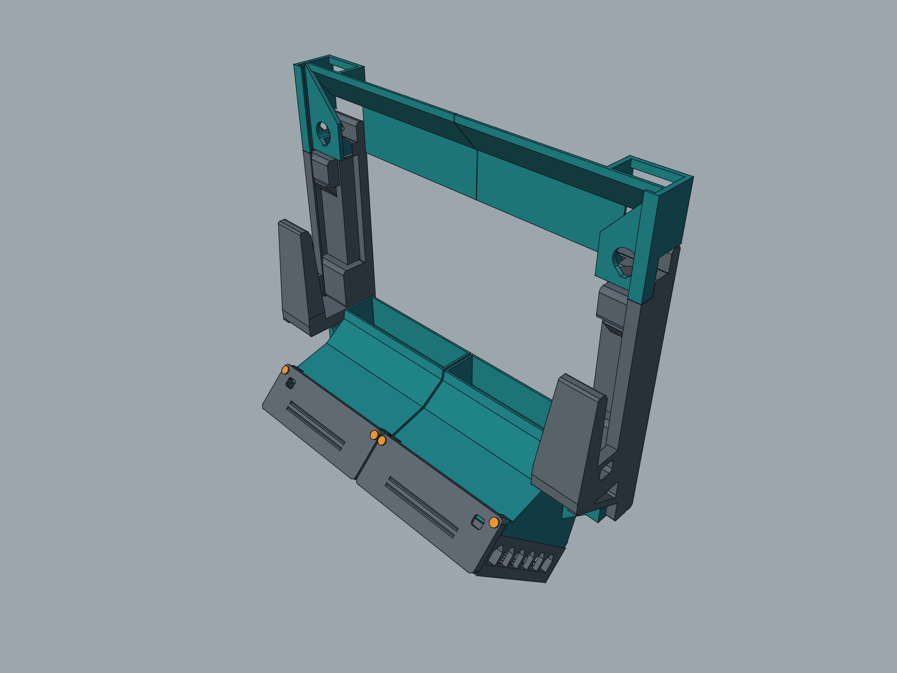
freecad/cel_preview.png
