thereprocase/dell-5560-wall-mount/freecad/Cradle_preview.png

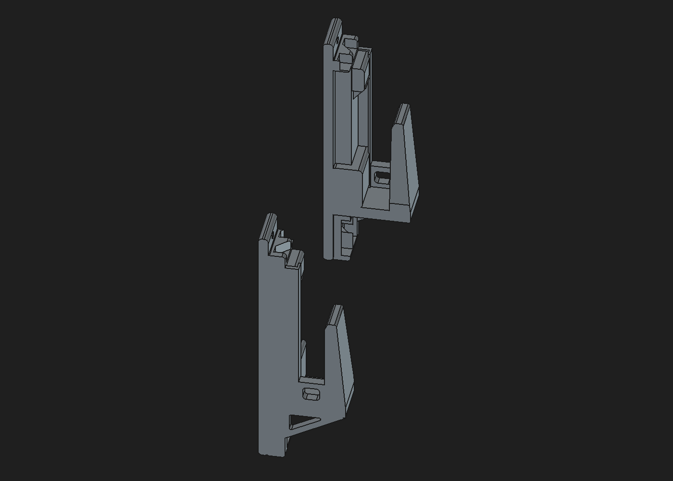
freecad/Cradle_preview.png
