thereprocase/dell-5560-wall-mount/freecad/duct_wall_protected.png

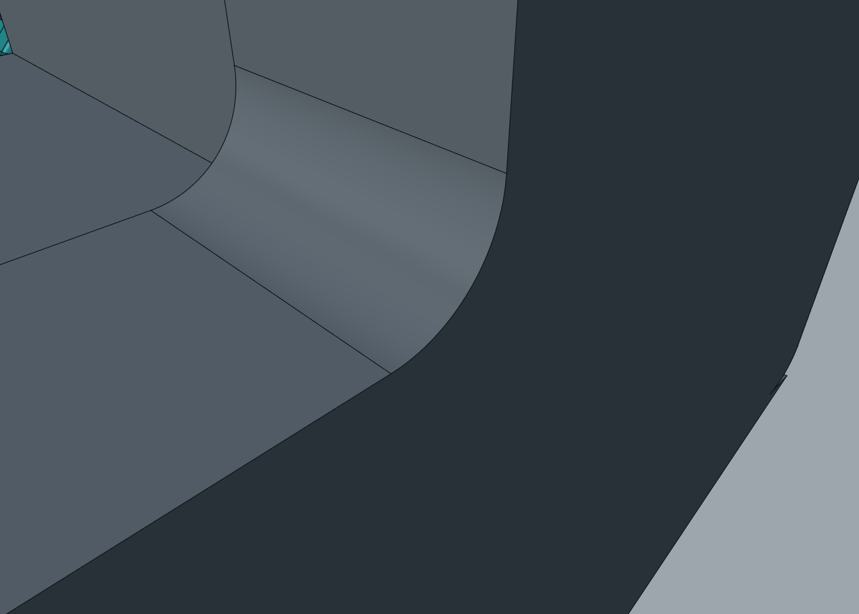
freecad/duct_wall_protected.png
