thereprocase/dell-5560-wall-mount/freecad/FanCap_preview.png

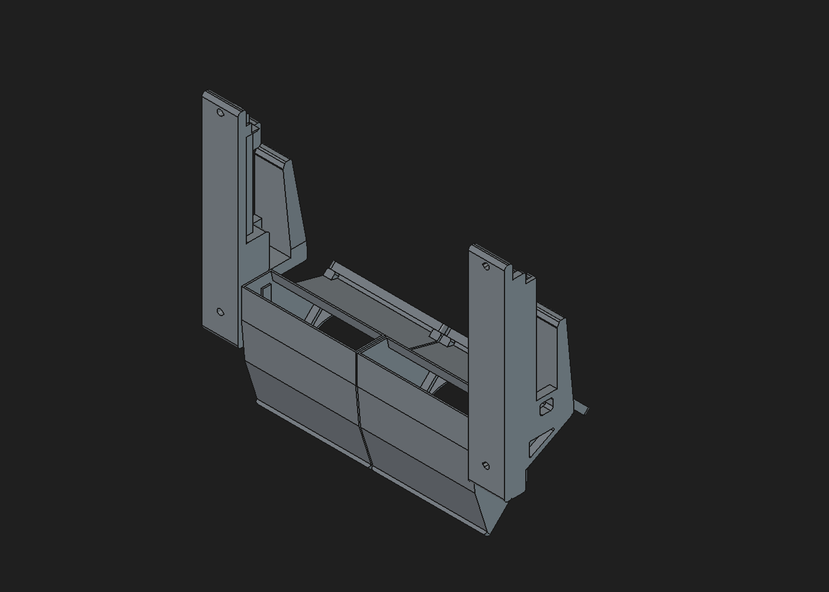
freecad/FanCap_preview.png
