thereprocase/dell-5560-wall-mount/freecad/finished_detail.png

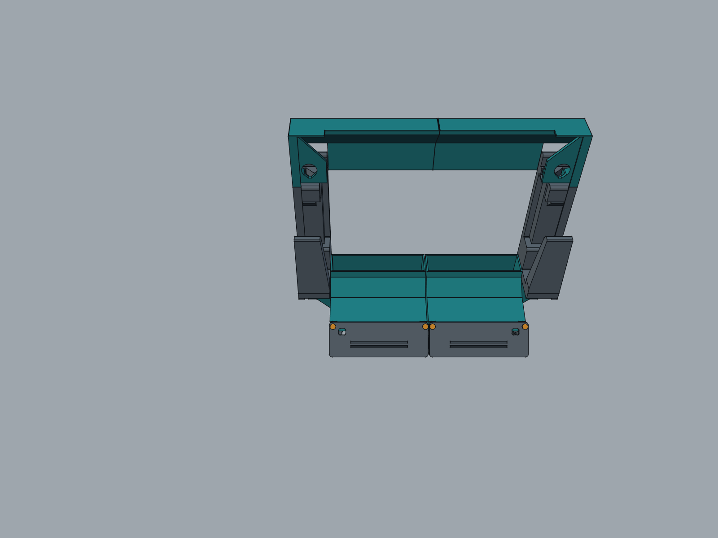
freecad/finished_detail.png
