thereprocase/dell-5560-wall-mount/freecad/fit_review_fan_rear.png

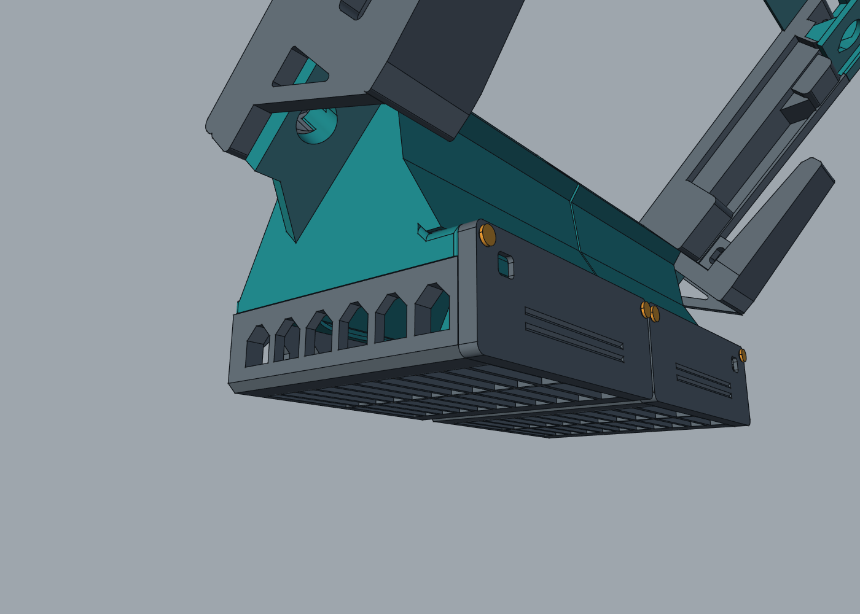
freecad/fit_review_fan_rear.png
