thereprocase/dell-5560-wall-mount/freecad/fit_review_rail.png

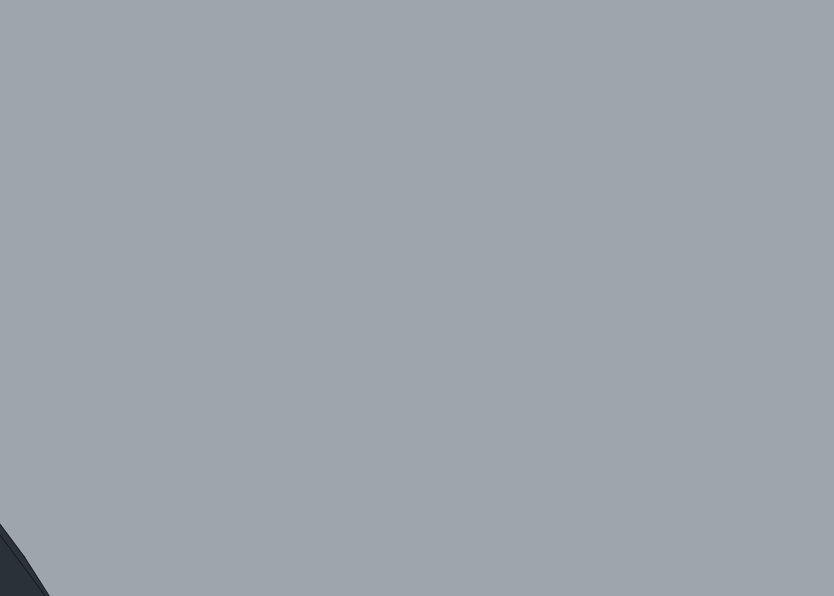
freecad/fit_review_rail.png
