thereprocase/dell-5560-wall-mount/freecad/OutletRail_preview.png

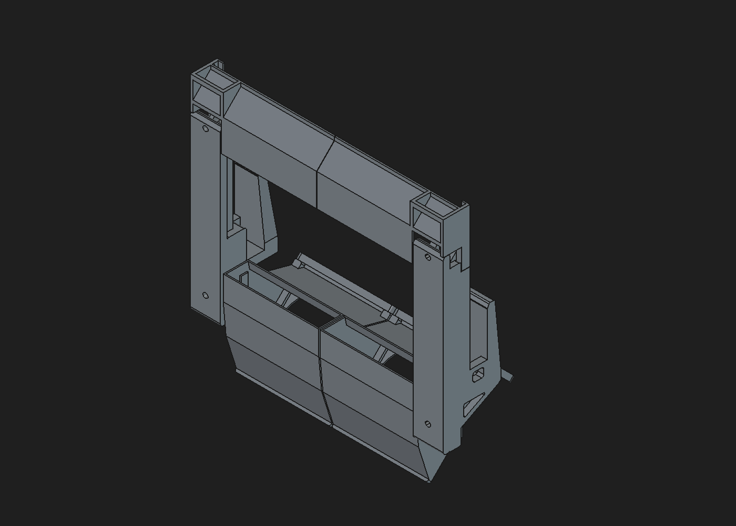
freecad/OutletRail_preview.png
