thereprocase/dell-5560-wall-mount/freecad/pin_preview.png

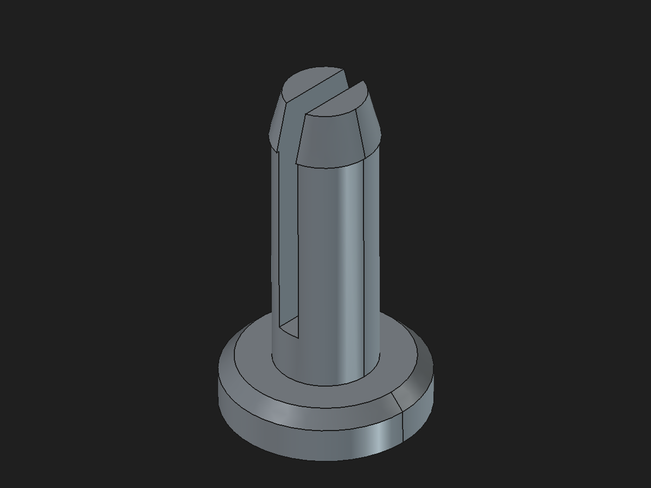
freecad/pin_preview.png
