thereprocase/dell-5560-wall-mount/freecad/rail_refinement_preview.png

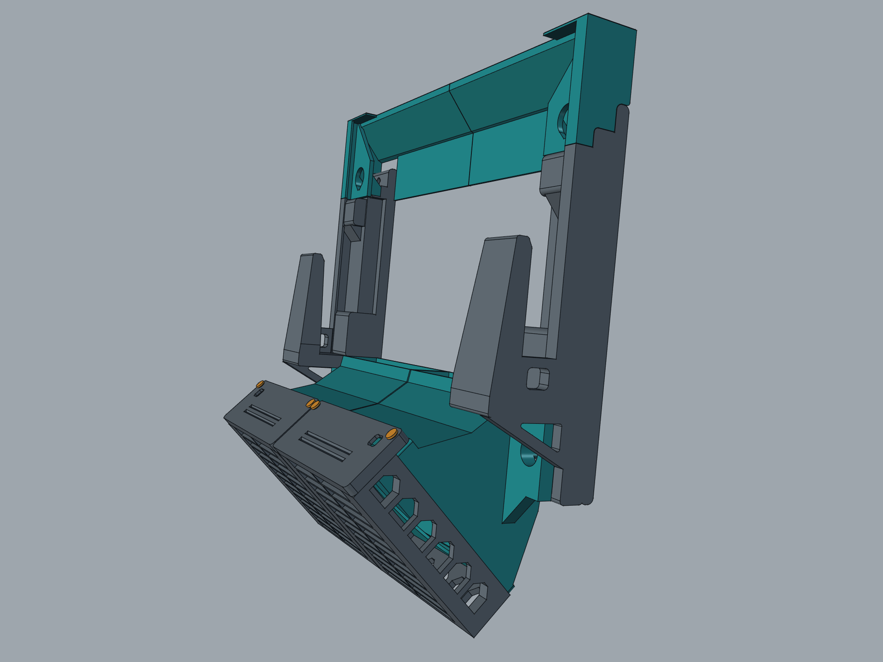
freecad/rail_refinement_preview.png
