thereprocase/dell-5560-wall-mount/freecad/studio_preview.png

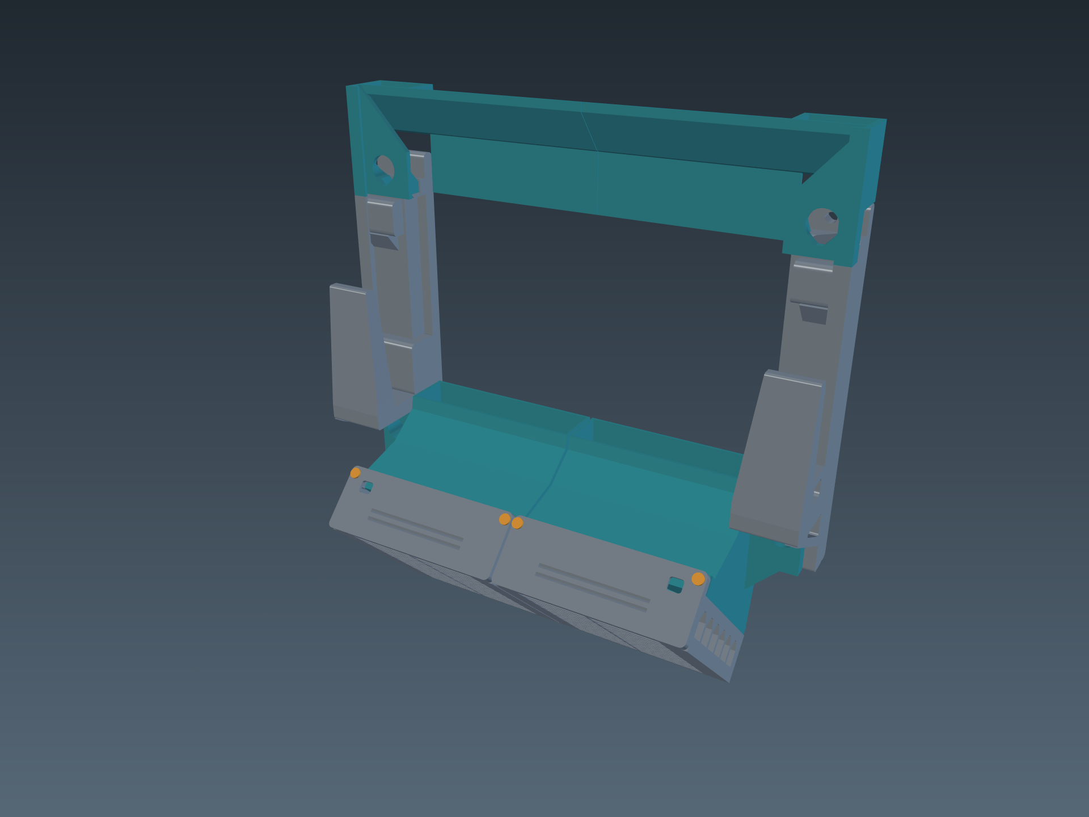
freecad/studio_preview.png
