thereprocase/dell-5560-wall-mount/fusion/output/Fusion_native_pin.png

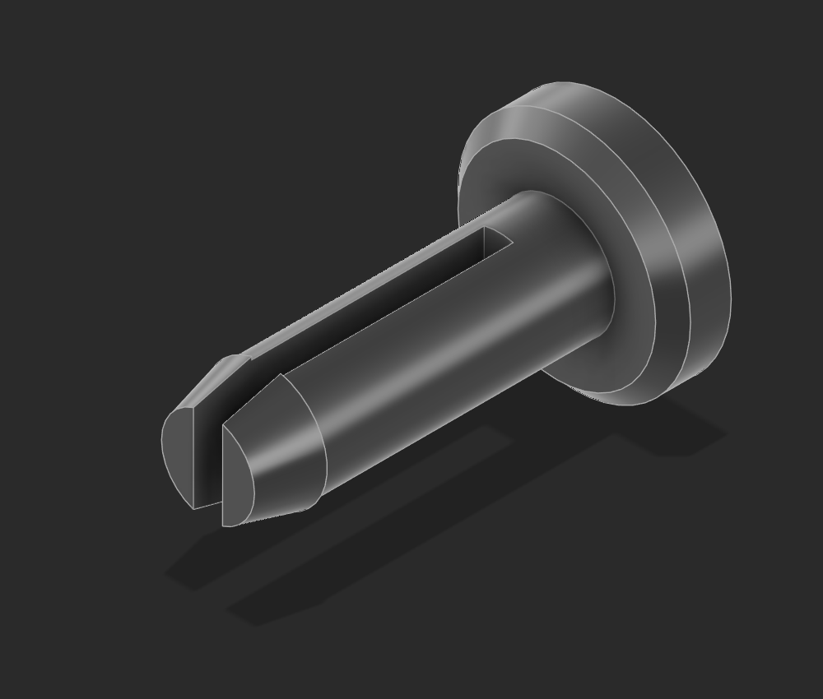
fusion/output/Fusion_native_pin.png
