thereprocase/dell-5560-wall-mount/onshape/exploration_20/pin_native.png

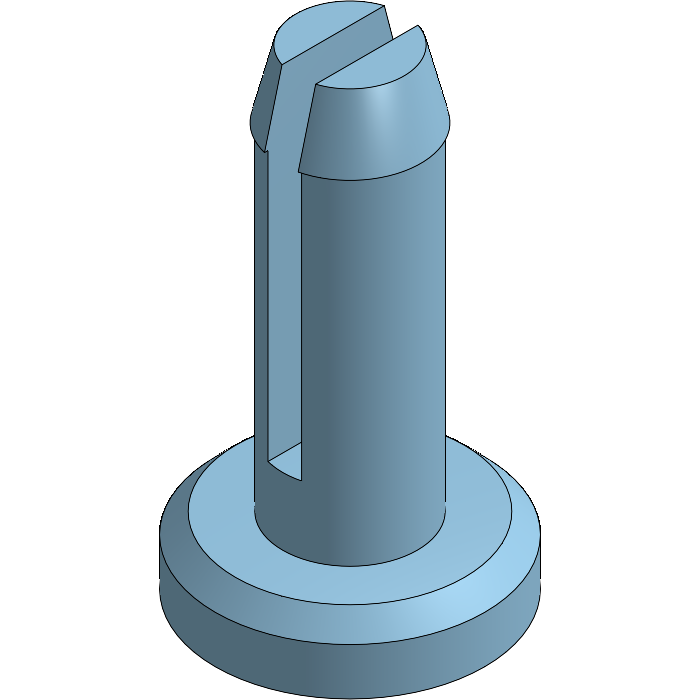
onshape/exploration_20/pin_native.png
