thereprocase/dell-5560-wall-mount/reference/Dell_5560_Base_Inside.jpg

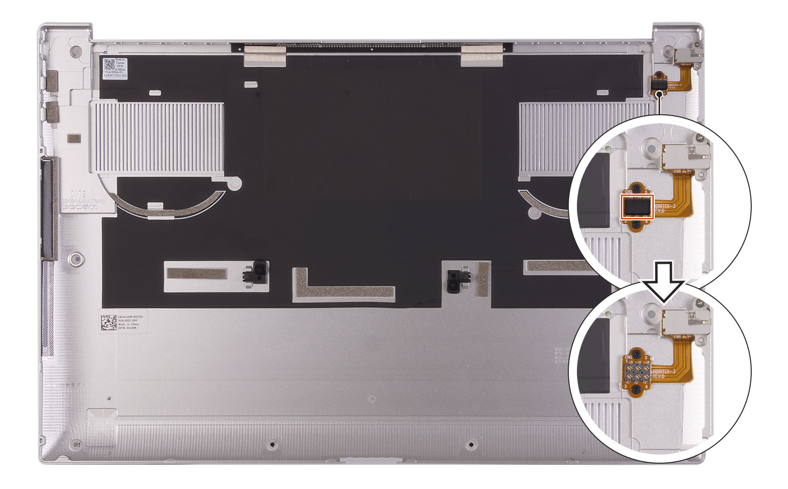
reference/Dell_5560_Base_Inside.jpg
