thereprocase/dell-5560-wall-mount/reference/Dell_5560_Bottom_View.png

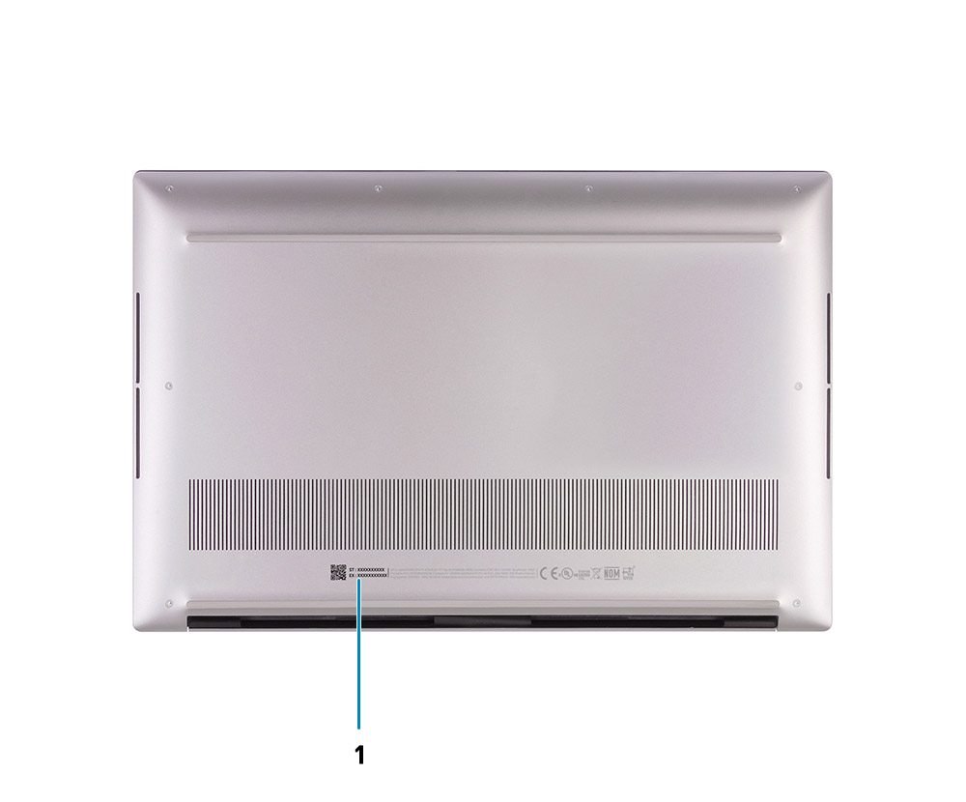
reference/Dell_5560_Bottom_View.png
