thereprocase/dell-5560-wall-mount/reference/Dell_5560_Left.jpg

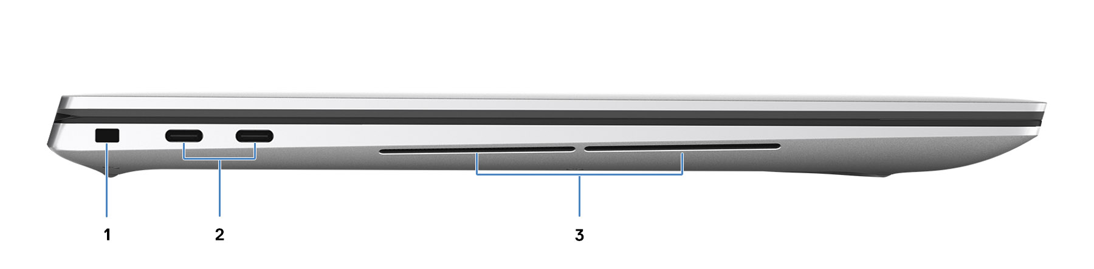
reference/Dell_5560_Left.jpg
