thereprocase/dell-5560-wall-mount/reference/Dell_5560_Right.jpg

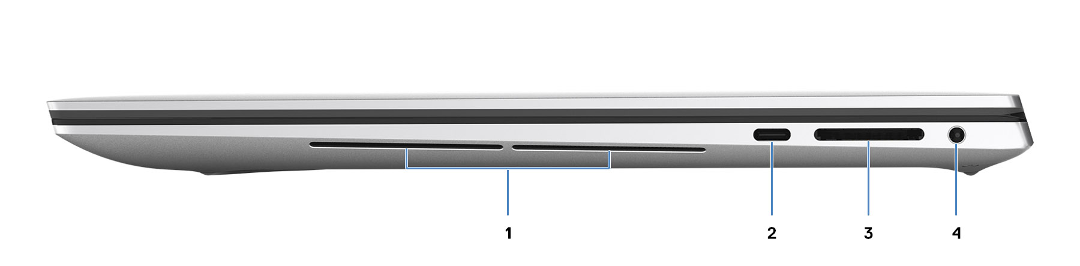
reference/Dell_5560_Right.jpg
