thereprocase/dell-5560-wall-mount/revh_cables/reports/09_left_fan_tray-toolpath.png

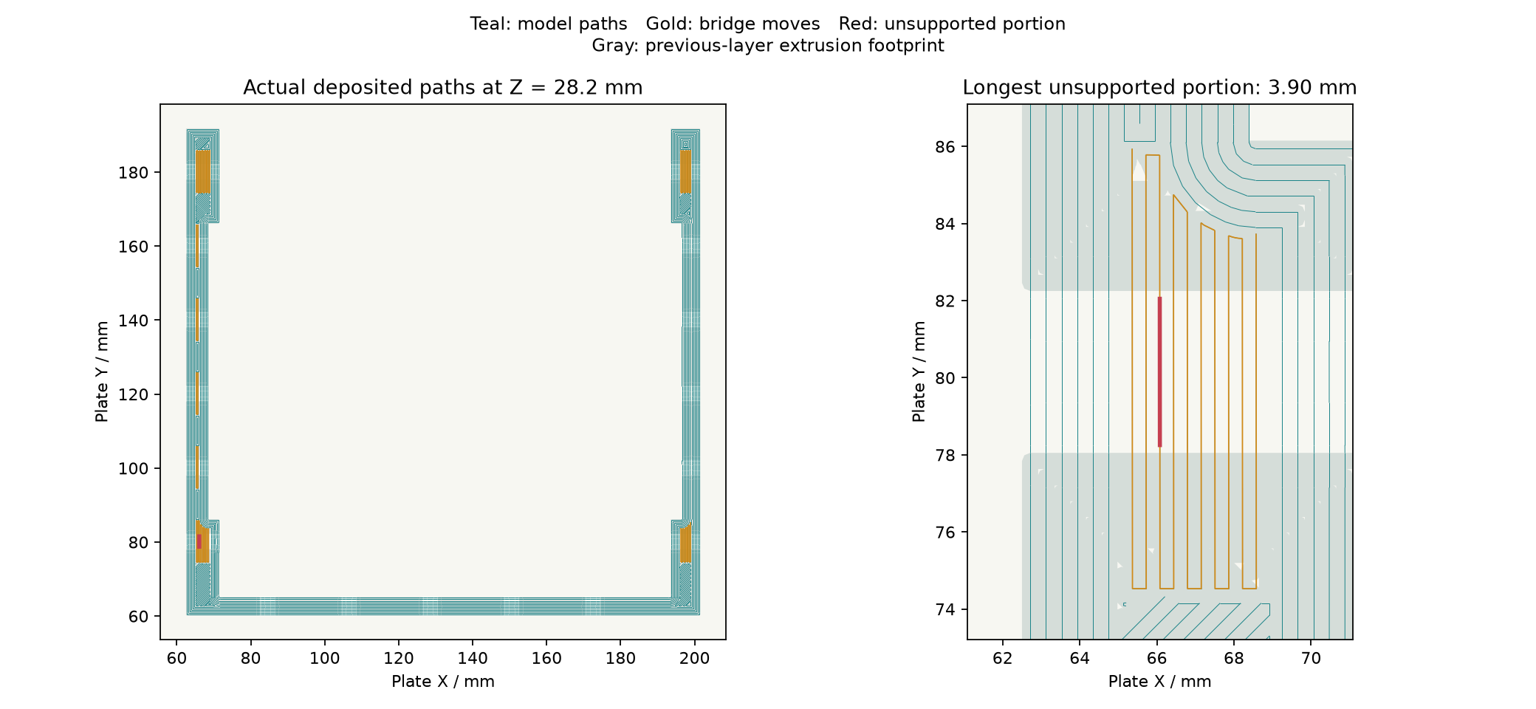
revh_cables/reports/09_left_fan_tray-toolpath.png
