thereprocase/dell-5560-wall-mount/revh_cables/reports/10_right_fan_tray-toolpath.png

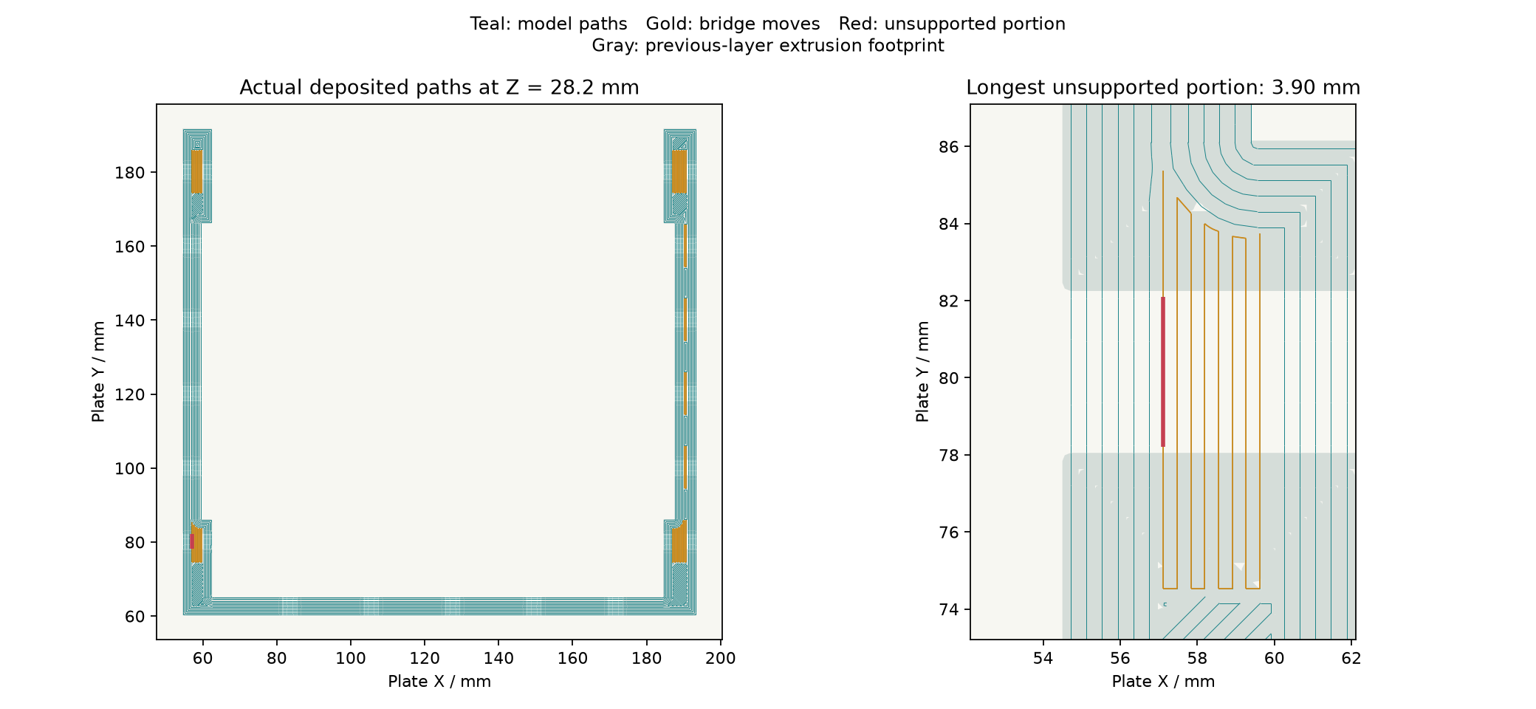
revh_cables/reports/10_right_fan_tray-toolpath.png
