thereprocase/dell-5560-wall-mount/revh_cables/reports/20_both_cable_covers-toolpath.png

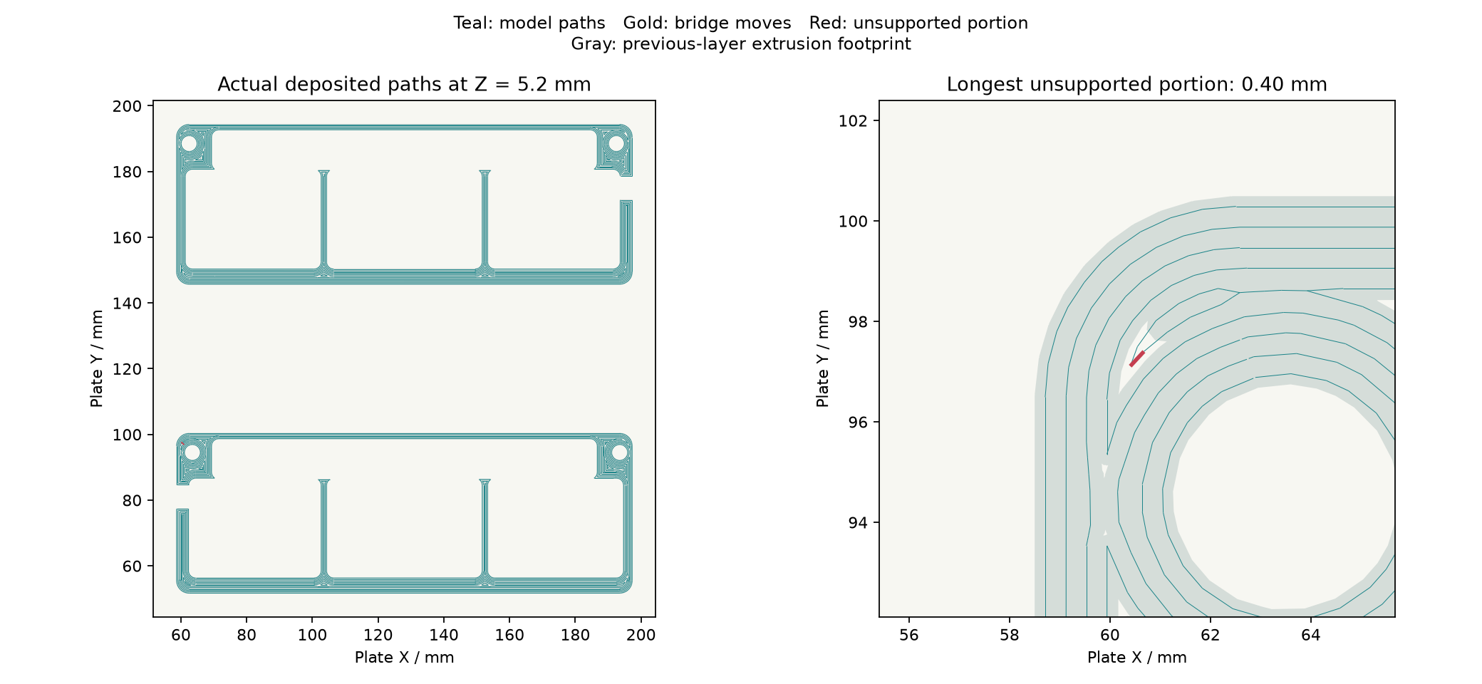
revh_cables/reports/20_both_cable_covers-toolpath.png
