thereprocase/dell-5560-wall-mount/revh_duct_r4/reports/04_right_fan_duct-support.png

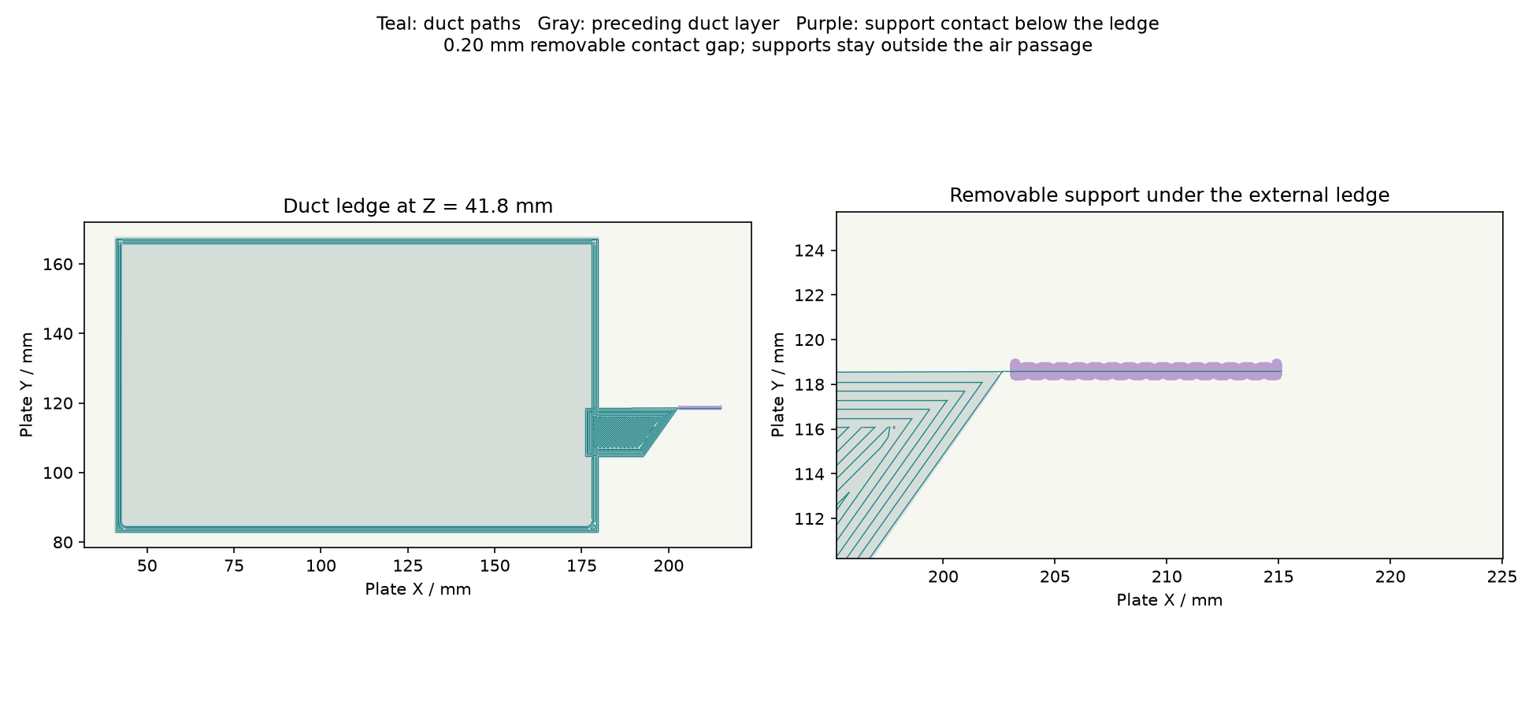
revh_duct_r4/reports/04_right_fan_duct-support.png
