thereprocase/dell-5560-wall-mount/freecad/Precision_5560_Native.step

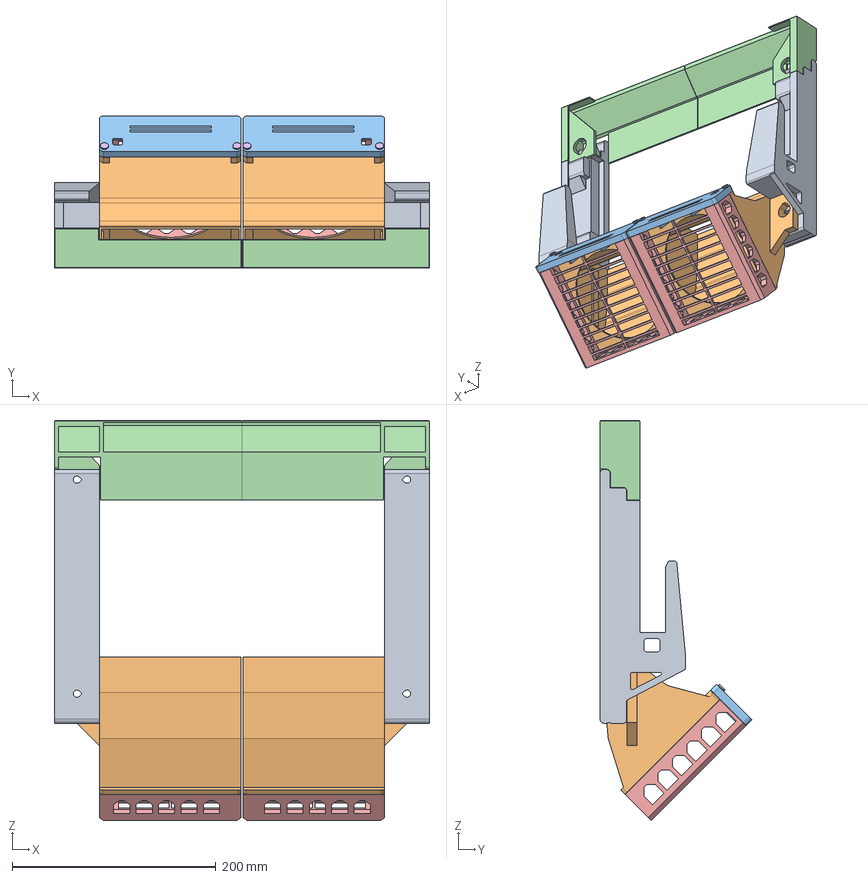
[picture p98: CAD file, 2026-10-06]
freecad/Precision_5560_Native.step
368.0 x 149.0 x 392.4 mm
02_right_cradle
01_left_cradle
04_right_fan_duct
03_left_fan_duct
06_right_fan_retainer
05_left_fan_retainer
08_right_outlet_rail
07_left_outlet_rail
10_right_fan_tray
09_left_fan_tray
Push pin — master x 4
