thereprocase/dell-5560-wall-mount/freecad/print_refinements/08_right_outlet_rail.step

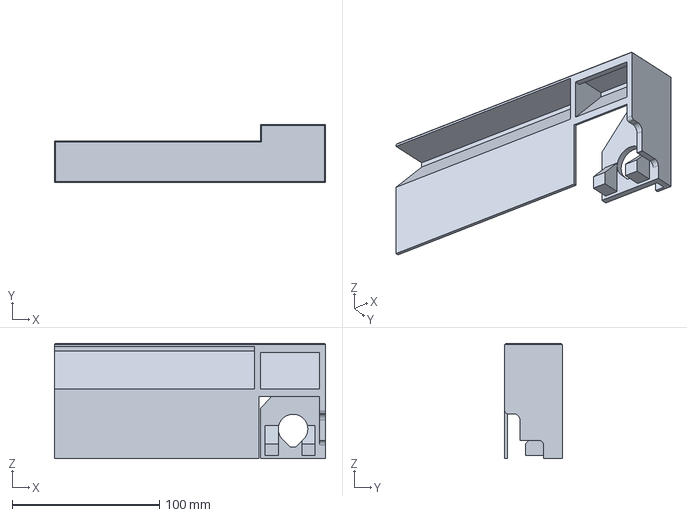
[picture p99: CAD file, 2026-10-06]
freecad/print_refinements/08_right_outlet_rail.step
183.8 x 39.0 x 78.0 mm
