thereprocase/dell-5560-wall-mount/freecad/print_refinements_oriented/03_left_fan_duct.stl

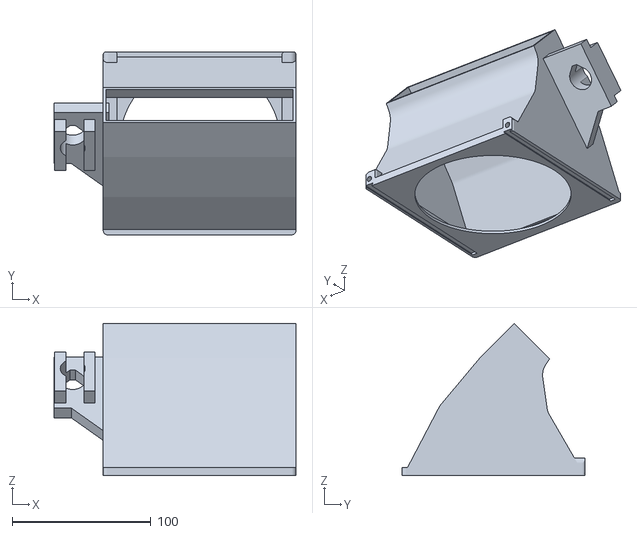
[picture p100: CAD file, 2026-10-06]
freecad/print_refinements_oriented/03_left_fan_duct.stl
174.5 x 131.7 x 109.6
