thereprocase/dell-5560-wall-mount/fusion/cfd/cases/OpenCFD_v2412/q20_coarse/constant/triSurface/fluid_boundary.stl

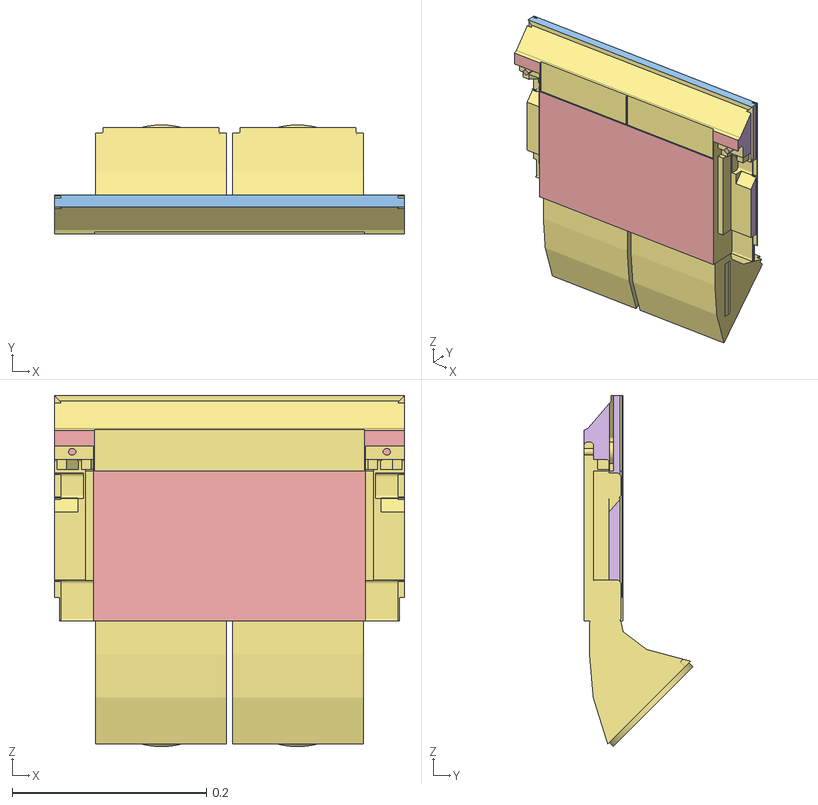
[picture p102: CAD file, 2026-10-06]
fusion/cfd/cases/OpenCFD_v2412/q20_coarse/constant/triSurface/fluid_boundary.stl
0.36 x 0.112 x 0.361
fan_left
fan_right
outlet
laptop_shell
wall_plane
assumed_side_seals
printed_or_model_walls
