thereprocase/dell-5560-wall-mount/fusion/cfd/geometry/fluid.step

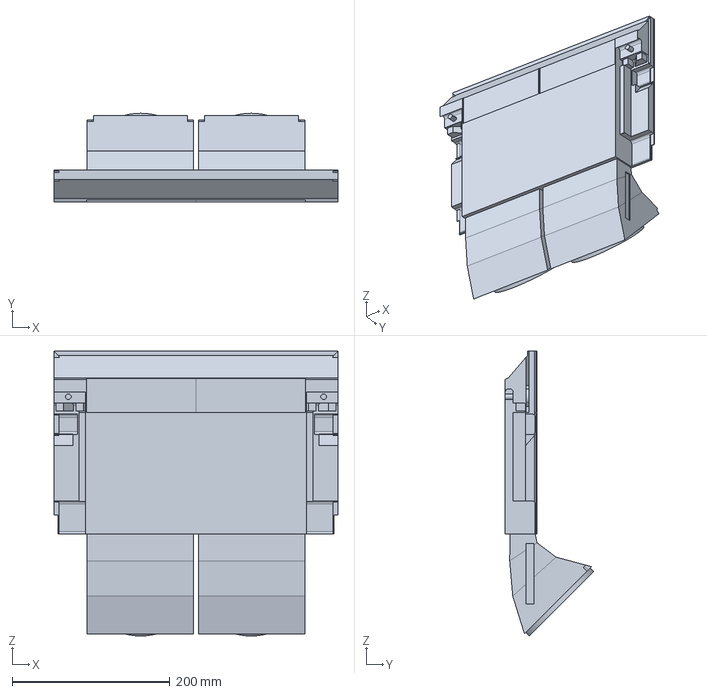
[picture p103: CAD file, 2026-10-06]
fusion/cfd/geometry/fluid.step
360.0 x 112.3 x 361.3 mm
