thereprocase/dell-5560-wall-mount/fusion/cfd/geometry_installed/printed.stl

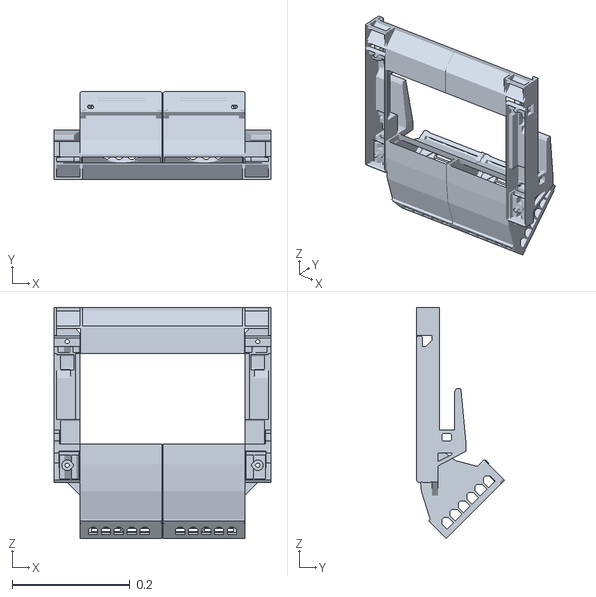
[picture p106: CAD file, 2026-10-06]
fusion/cfd/geometry_installed/printed.stl
0.368 x 0.149 x 0.392
