thereprocase/dell-5560-wall-mount/fusion/cfd/geometry_installed/zones/dell_fan_left.stl

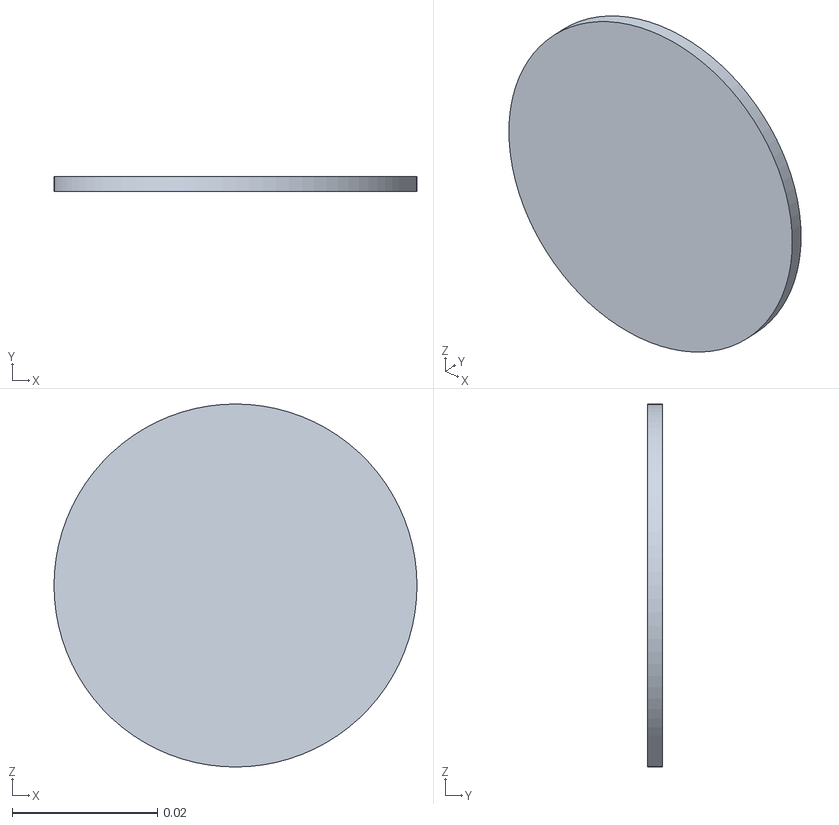
[picture p107: CAD file, 2026-10-06]
fusion/cfd/geometry_installed/zones/dell_fan_left.stl
0.05 x 0.002 x 0.05
