thereprocase/dell-5560-wall-mount/fusion/cfd/geometry_revh/laptop.stl

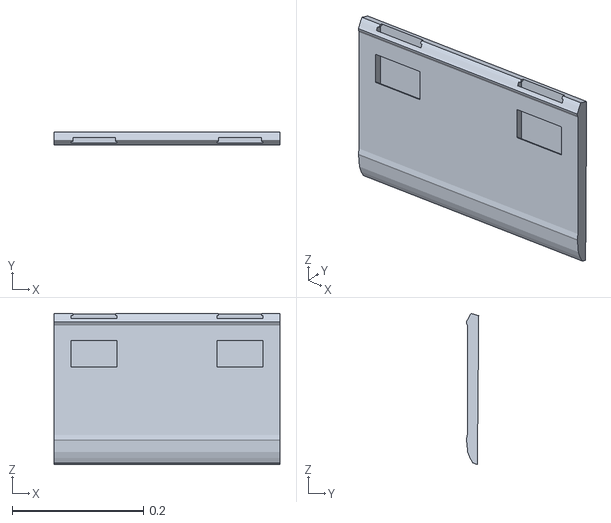
[picture p108: CAD file, 2026-10-06]
fusion/cfd/geometry_revh/laptop.stl
0.344 x 0.0191 x 0.23
