thereprocase/dell-5560-wall-mount/fusion/cfd/geometry_traced_repaired/ambient_openings.stl

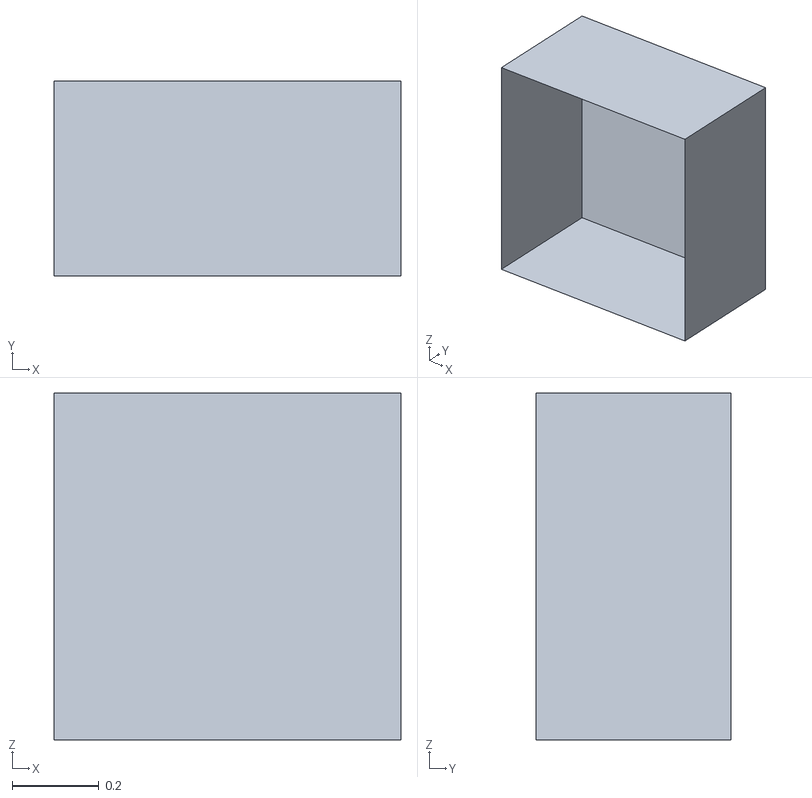
[picture p109: CAD file, 2026-10-06]
fusion/cfd/geometry_traced_repaired/ambient_openings.stl
0.8 x 0.45 x 0.8
