thereprocase/dell-5560-wall-mount/fusion/cfd/geometry_traced_v1/zones/noctua_fan_left.stl

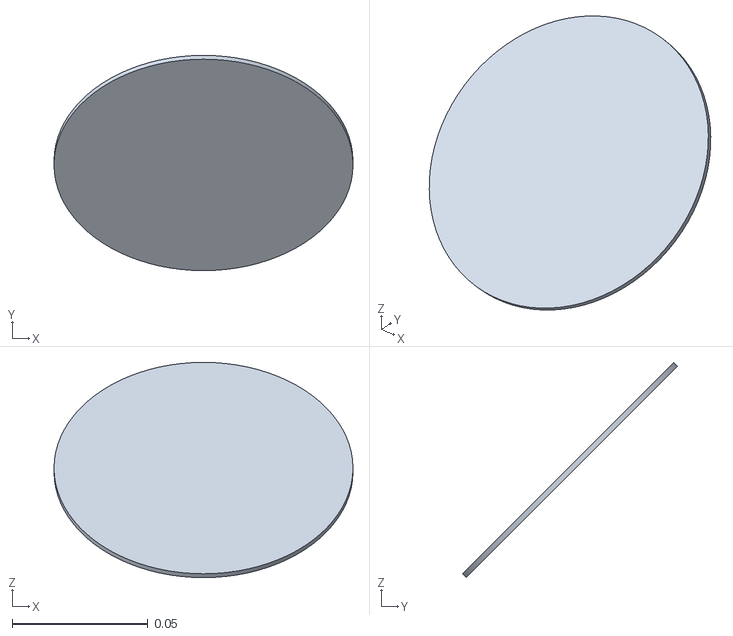
[picture p110: CAD file, 2026-10-06]
fusion/cfd/geometry_traced_v1/zones/noctua_fan_left.stl
0.11 x 0.0792 x 0.0792
