thereprocase/dell-5560-wall-mount/minimalist/presets/13-inch-example/print/05_left_fan_cap.step

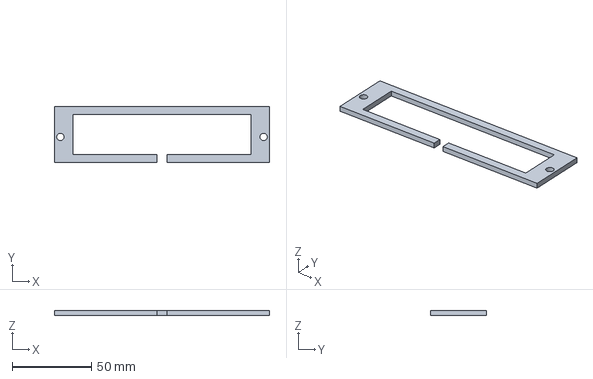
[picture p112: CAD file, 2026-10-06]
minimalist/presets/13-inch-example/print/05_left_fan_cap.step
135.4 x 35.1 x 3.00 mm
