thereprocase/dell-5560-wall-mount/REFERENCE_Installed_Layout.step

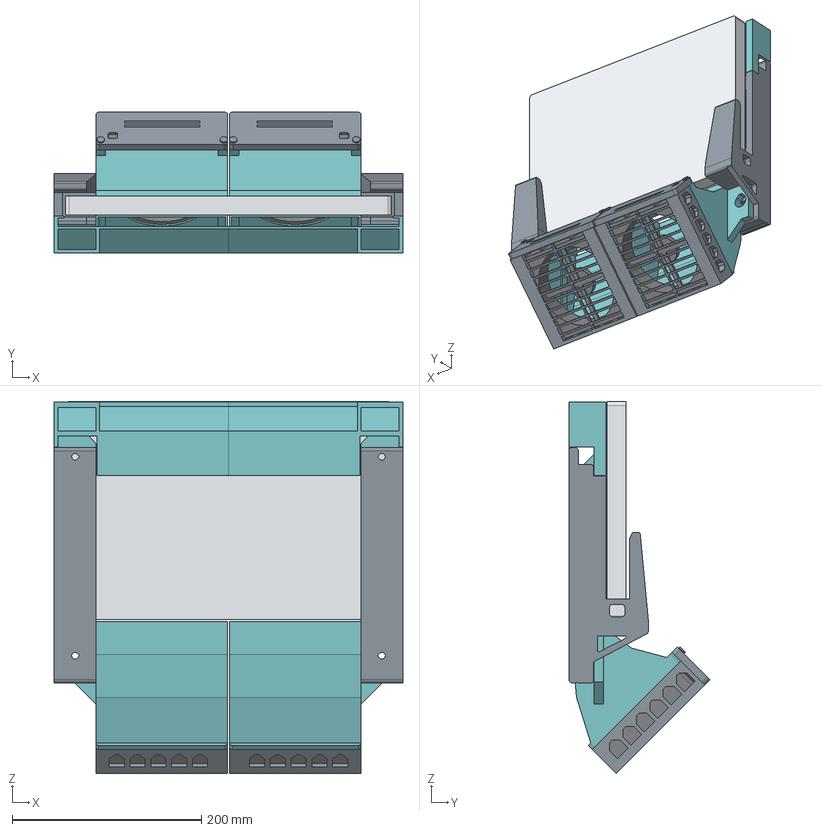
[picture p117: CAD file, 2026-10-06]
REFERENCE_Installed_Layout.step
368.0 x 149.0 x 392.7 mm
01_left_cradle
02_right_cradle
03_left_fan_duct
04_right_fan_duct
05_left_fan_retainer
06_right_fan_retainer
07_left_outlet_rail
08_right_outlet_rail
09_left_fan_tray
10_right_fan_tray
11_left_push_pin
12_right_push_pin
13_left_push_pin
14_right_push_pin
LAPTOP_ENVELOPE
FAN_0
FAN_1
