thereprocase/dell-5560-wall-mount/revh_cables/Precision_5560_RevH_Cable_Management_C1.FCStd

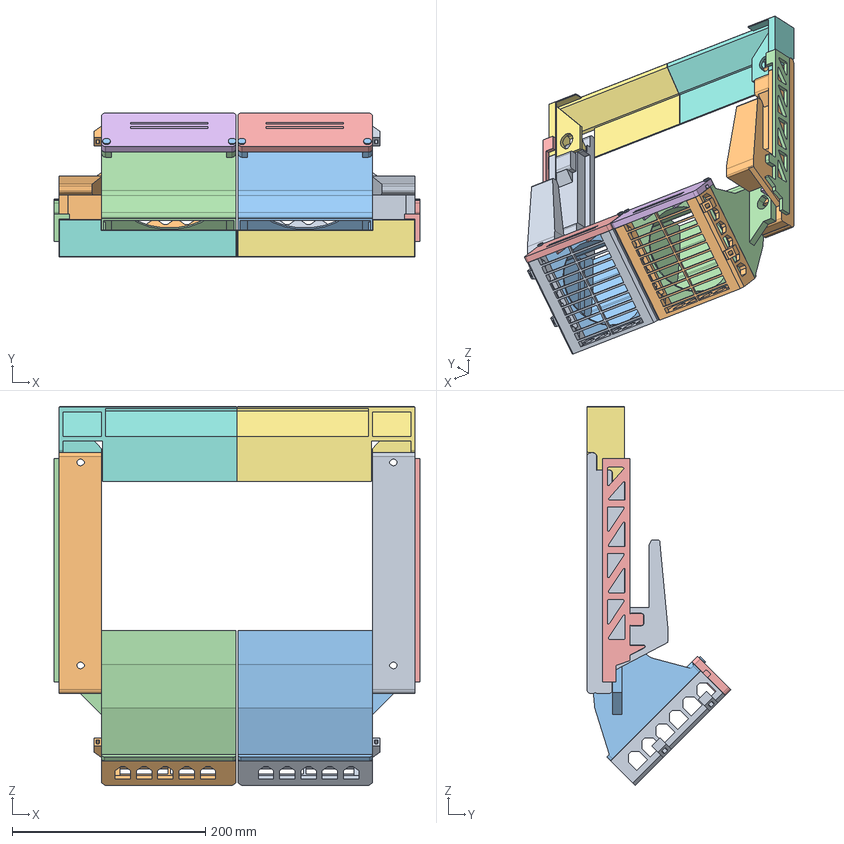
[picture p118: CAD file, 2026-10-06]
revh_cables/Precision_5560_RevH_Cable_Management_C1.FCStd
378.6 x 149.0 x 392.4 mm
02_right_cradle
01_left_cradle
04_right_fan_duct
03_left_fan_duct
06 right fan retainer / H-C1 source
05 left fan retainer / H-C1 source
08_right_outlet_rail
07_left_outlet_rail
10 right fan tray / H-C1 source
09 left fan tray / H-C1 source
Push pin — master x 4
15 — left removable side retainer
16 — right removable side retainer
17 — left side-retainer keeper
18 — right side-retainer keeper
