thereprocase/dell-5560-wall-mount/revh_cables/print/05_left_fan_retainer.step

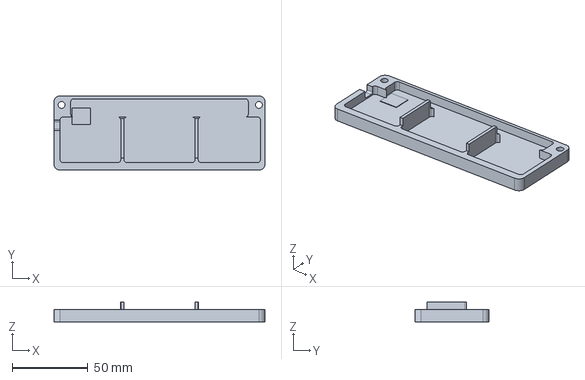
[picture p119: CAD file, 2026-10-06]
revh_cables/print/05_left_fan_retainer.step
139.0 x 49.0 x 13.0 mm
