thereprocase/dell-5560-wall-mount/revh_duct_r4/baseline/Precision_5560_RevH_Current.FCStd

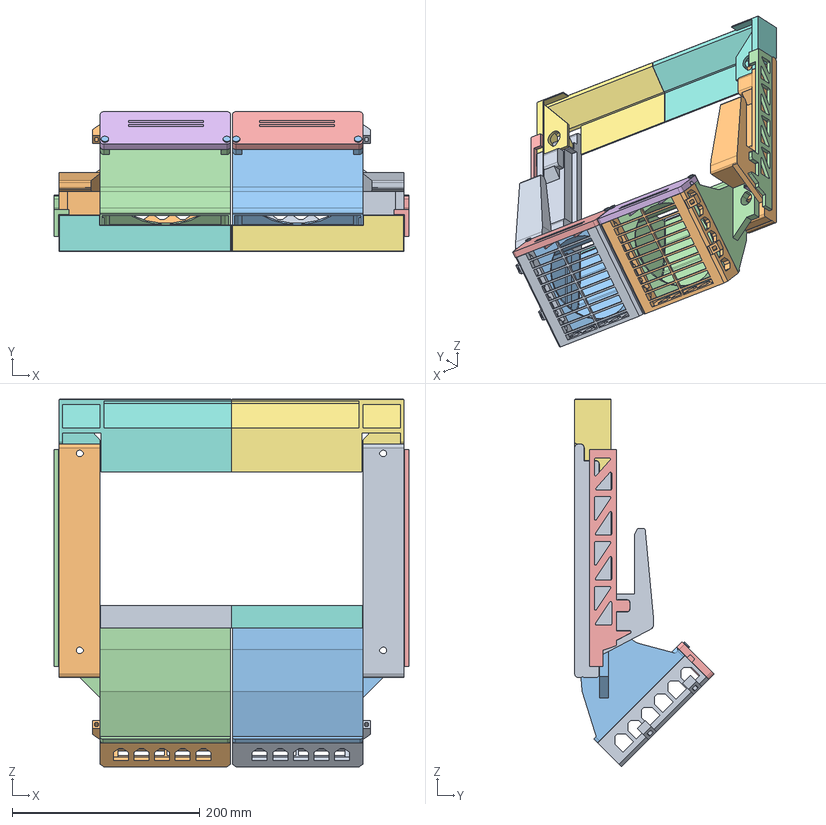
[picture p120: CAD file, 2026-10-06]
revh_duct_r4/baseline/Precision_5560_RevH_Current.FCStd
378.6 x 149.0 x 392.4 mm
02_right_cradle
01_left_cradle
04 right fan duct / D3 reinforced inlet
03 left fan duct / D3 reinforced inlet
06 right fan retainer / H-C1 source
05 left fan retainer / H-C1 source
08_right_outlet_rail
07_left_outlet_rail
10 right fan tray / T3 selected fit
09 left fan tray / T3 selected fit
Push pin — master x 4
15 left side retainer / R2 candidate
16 right side retainer / R2 candidate
17 left retainer keeper / R2 candidate
18 right retainer keeper / R2 candidate
20 right rear air baffle / B1 optional
19 left rear air baffle / B1 optional
