thereprocase/dell-5560-wall-mount/revh_retention/Precision_5560_RevH_Removable_Retainers.FCStd

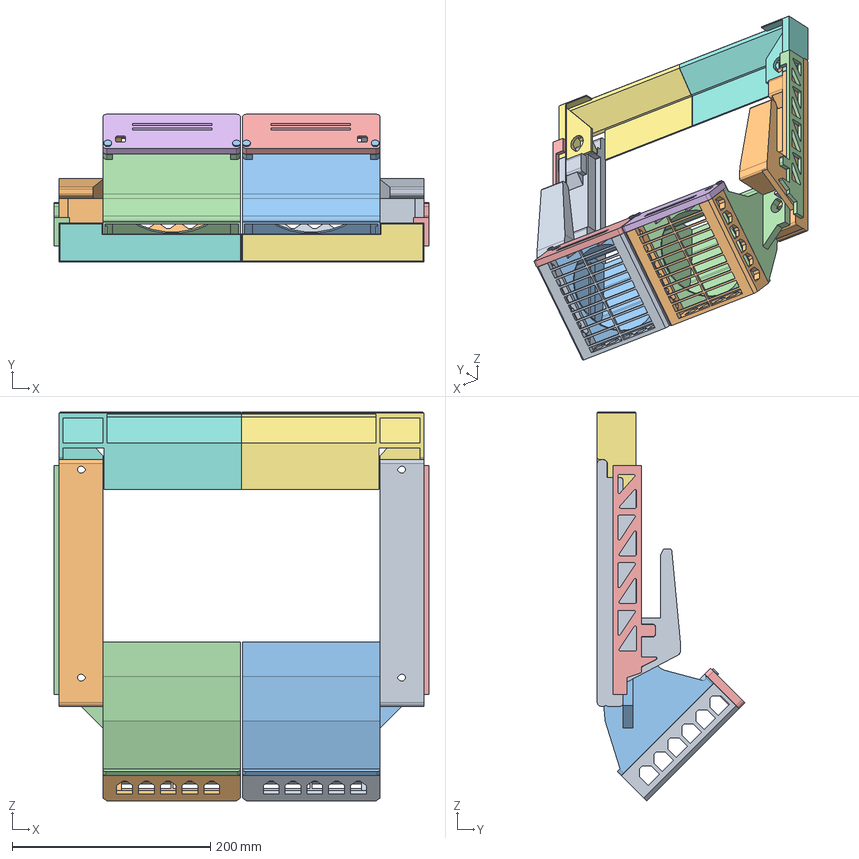
[picture p121: CAD file, 2026-10-06]
revh_retention/Precision_5560_RevH_Removable_Retainers.FCStd
378.6 x 149.0 x 392.4 mm
02_right_cradle
01_left_cradle
04_right_fan_duct
03_left_fan_duct
06_right_fan_retainer
05_left_fan_retainer
08_right_outlet_rail
07_left_outlet_rail
10_right_fan_tray
09_left_fan_tray
Push pin — master x 4
15 — left removable side retainer
16 — right removable side retainer
17 — left side-retainer keeper
18 — right side-retainer keeper
