thereprocase/dell-5560-wall-mount/docs/models/after/12_right_push_pin.stl

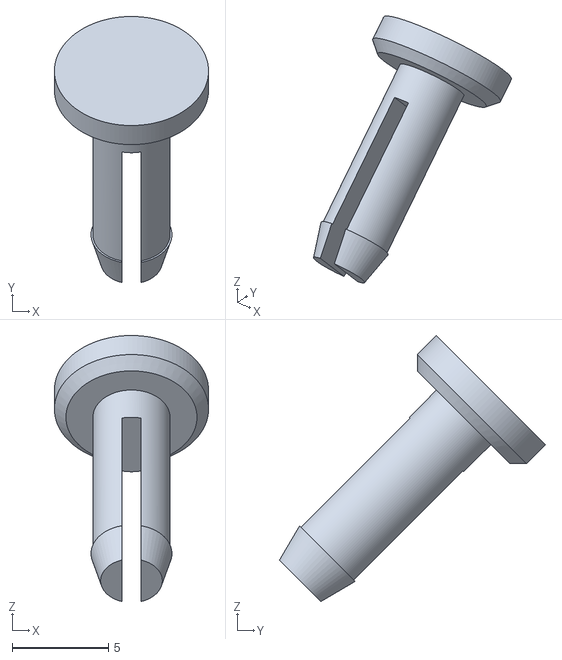
[picture p122: CAD file, 2026-10-06]
docs/models/after/12_right_push_pin.stl
8.00 x 13.8 x 13.8
