thereprocase/dell-5560-wall-mount/docs/models/minimalist/13-inch-example/05_left_fan_cap.stl

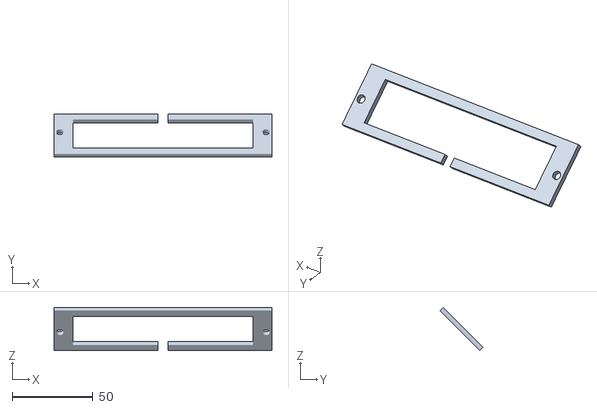
[picture p123: CAD file, 2026-10-06]
docs/models/minimalist/13-inch-example/05_left_fan_cap.stl
135.4 x 26.9 x 26.9
