thereprocase/dell-5560-wall-mount/docs/models/minimalist/14-inch-example/08_right_dam.stl

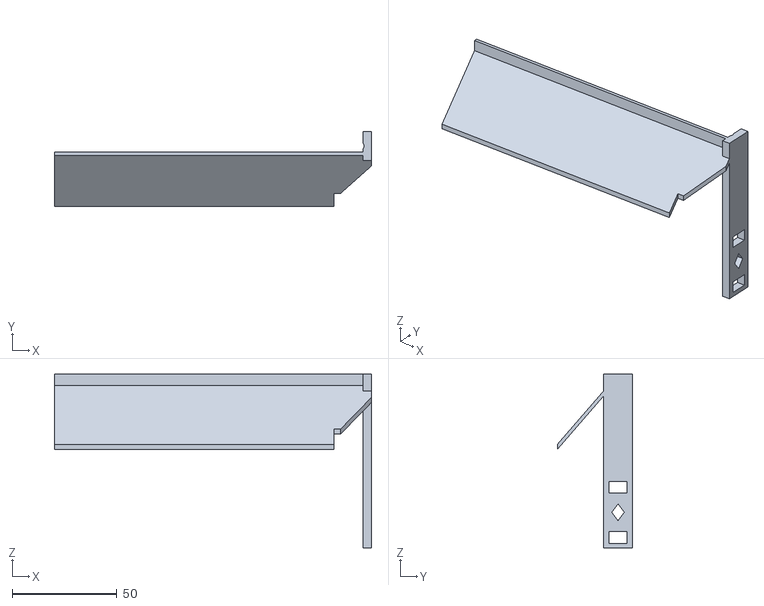
[picture p124: CAD file, 2026-10-06]
docs/models/minimalist/14-inch-example/08_right_dam.stl
151.4 x 36.0 x 83.0
