thereprocase/dell-5560-wall-mount/docs/models/retainers/15_left_side_retainer.stl

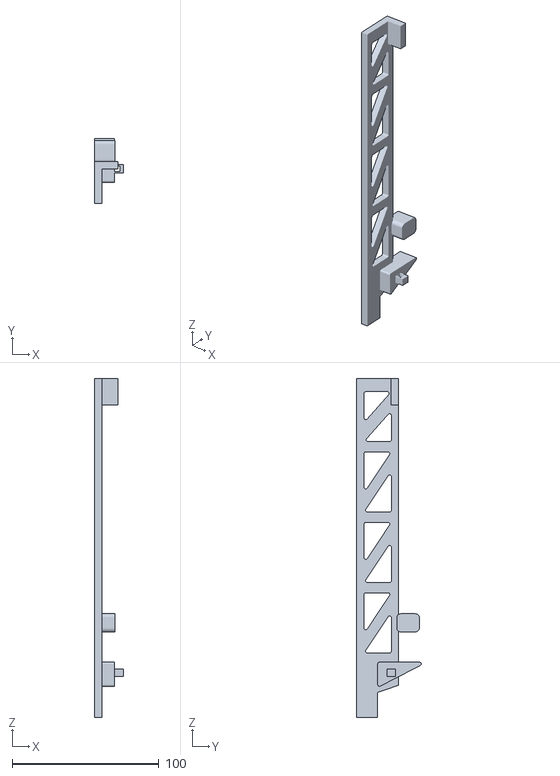
[picture p125: CAD file, 2026-10-06]
docs/models/retainers/15_left_side_retainer.stl
19.8 x 44.0 x 231.0
