thereprocase/dell-5560-wall-mount/fusion/cfd/geometry/fan_left.stl

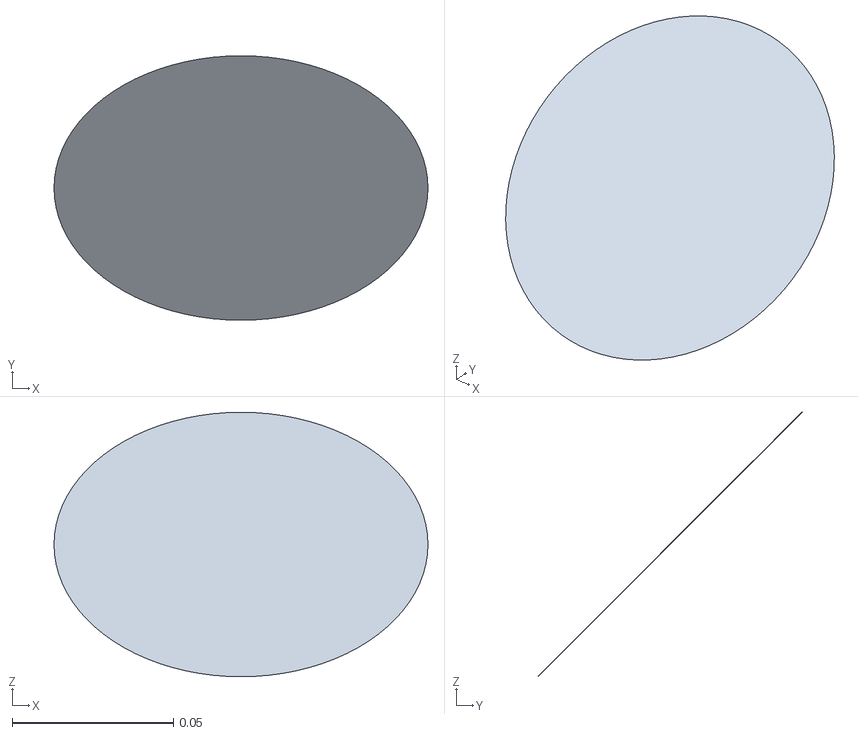
[picture p126: CAD file, 2026-10-06]
fusion/cfd/geometry/fan_left.stl
0.116 x 0.082 x 0.082
