thereprocase/dell-5560-wall-mount/fusion/cfd/geometry_gap16/wall_plane.stl

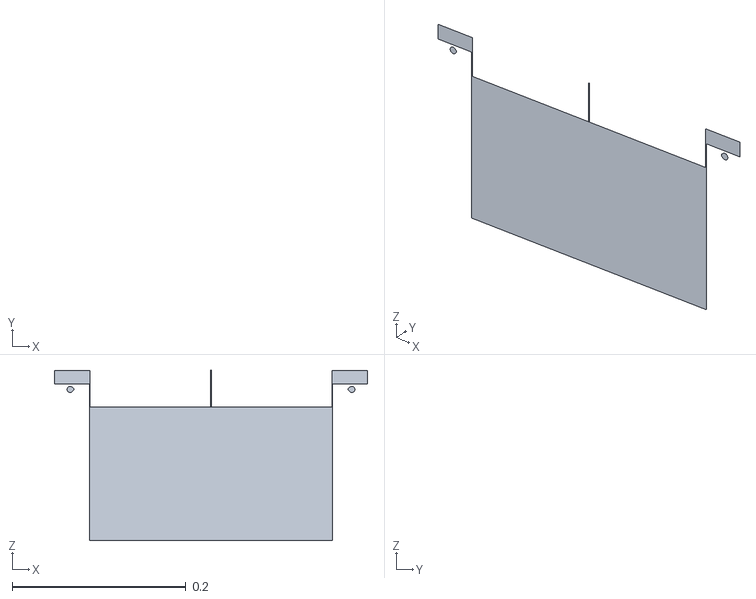
[picture p127: CAD file, 2026-10-06]
fusion/cfd/geometry_gap16/wall_plane.stl
0.36 x 0 x 0.196
