thereprocase/dell-5560-wall-mount/fusion/cfd/geometry_installed/wall_plane.stl

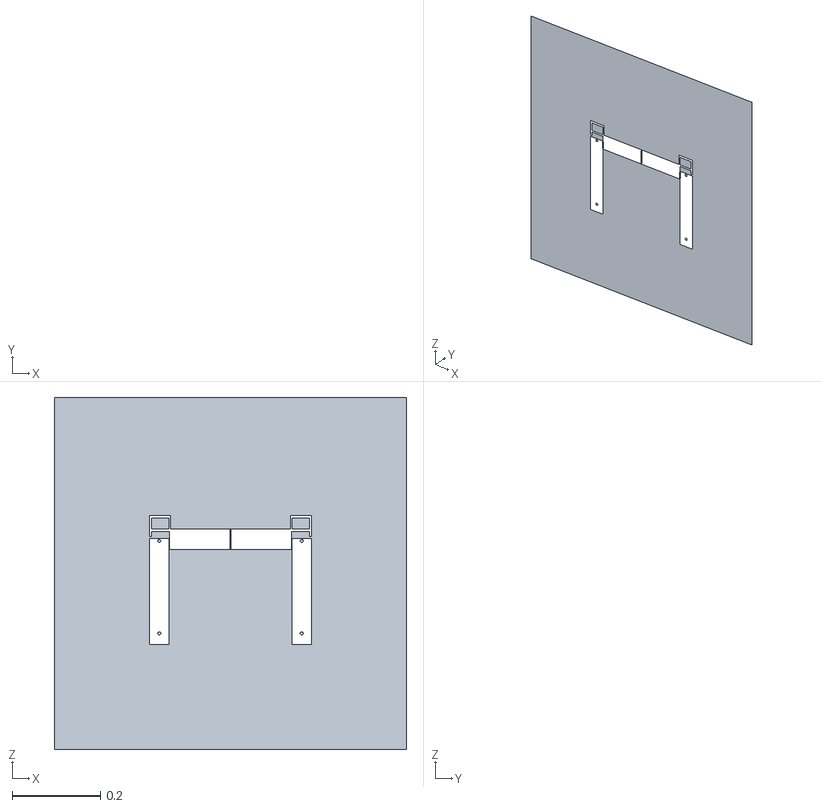
[picture p128: CAD file, 2026-10-06]
fusion/cfd/geometry_installed/wall_plane.stl
0.8 x 0 x 0.8
