thereprocase/dell-5560-wall-mount/fusion/cfd/geometry_revh/wall_plane.stl

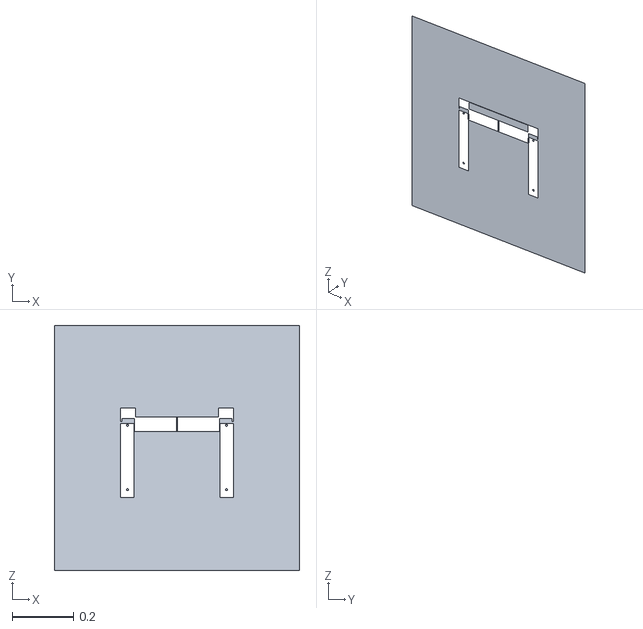
[picture p129: CAD file, 2026-10-06]
fusion/cfd/geometry_revh/wall_plane.stl
0.8 x 5.8e-17 x 0.8
