thereprocase/dell-5560-wall-mount/fusion/cfd/geometry_revh/zones/intake_grille_right.stl

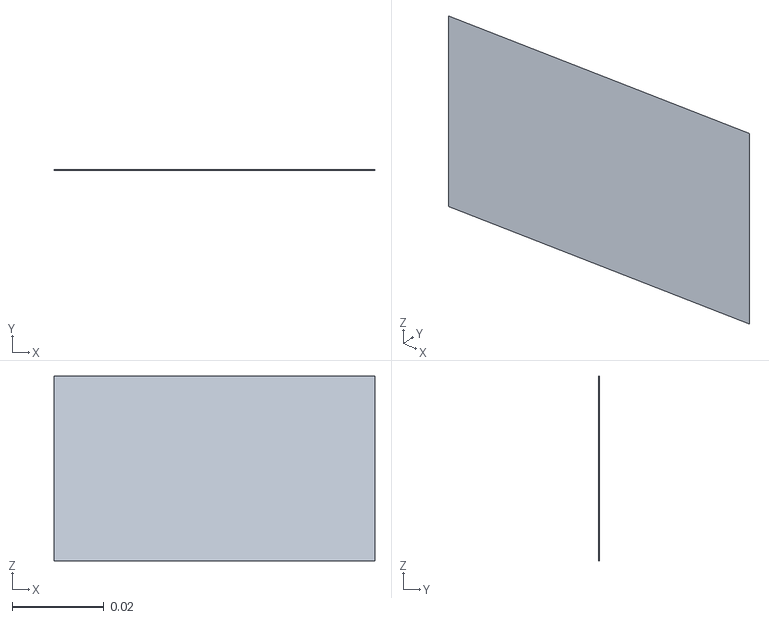
[picture p130: CAD file, 2026-10-06]
fusion/cfd/geometry_revh/zones/intake_grille_right.stl
0.0701 x 0.0001 x 0.0403
