thereprocase/dell-5560-wall-mount/minimalist/coupons/01_coupon_right_arm.step

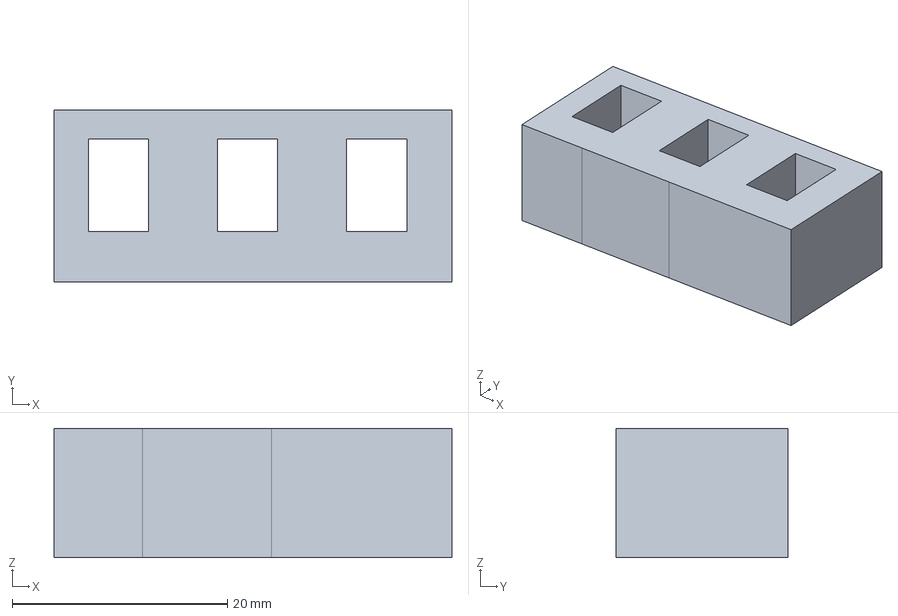
[picture p131: CAD file, 2026-10-06]
minimalist/coupons/01_coupon_right_arm.step
37.0 x 16.0 x 12.0 mm
