thereprocase/dell-5560-wall-mount/minimalist/presets/16-inch-example/print/15_left_dam_keeper.step

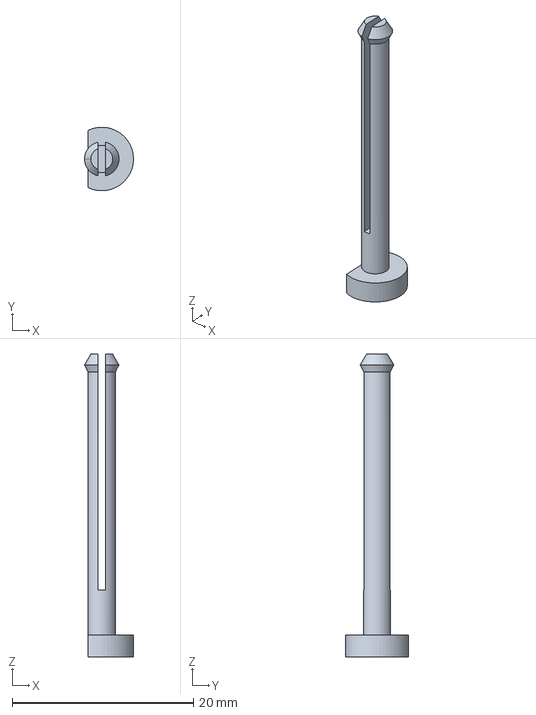
[picture p132: CAD file, 2026-10-06]
minimalist/presets/16-inch-example/print/15_left_dam_keeper.step
5.39 x 6.99 x 33.4 mm
