thereprocase/dell-5560-wall-mount/outlet_gap_variants/right_outlet_rail_gap_8mm.step

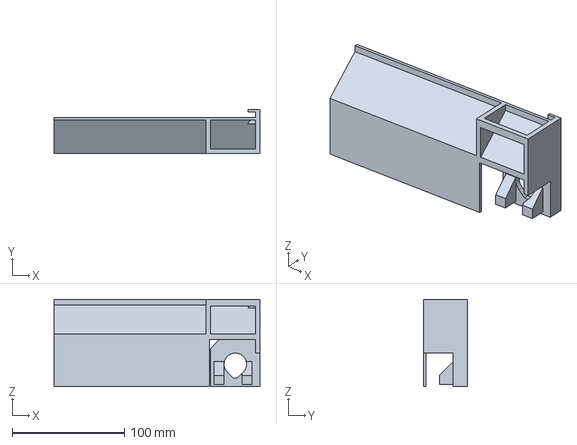
[picture p133: CAD file, 2026-10-06]
outlet_gap_variants/right_outlet_rail_gap_8mm.step
183.8 x 39.0 x 78.0 mm
