thereprocase/dell-5560-wall-mount/print_ready/09_left_fan_tray.3mf

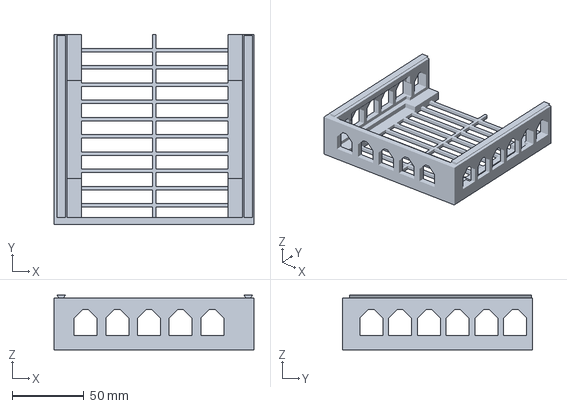
[picture p134: CAD file, 2026-10-06]
print_ready/09_left_fan_tray.3mf
139.0 x 132.0 x 38.0 mm
