thereprocase/dell-5560-wall-mount/REFERENCE_Estimated_Laptop_Profile.step

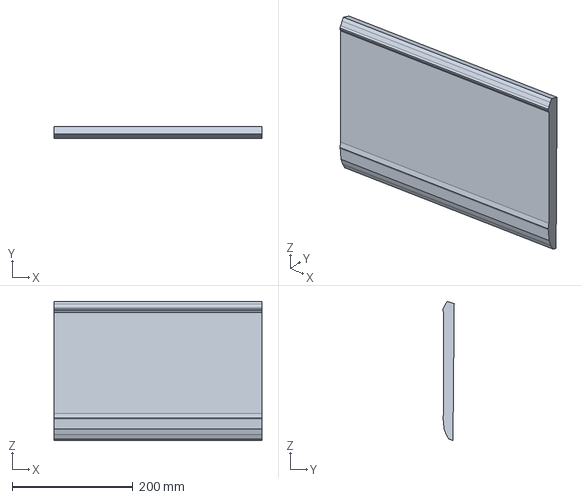
[picture p135: CAD file, 2026-10-06]
REFERENCE_Estimated_Laptop_Profile.step
344.4 x 19.1 x 230.3 mm
