thereprocase/dell-5560-wall-mount/revh_cables/print/20_both_cable_covers.step

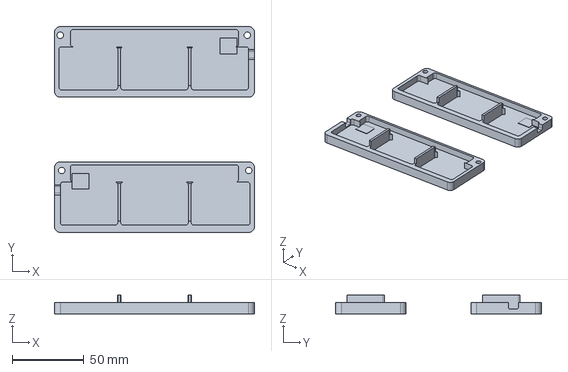
[picture p136: CAD file, 2026-10-06]
revh_cables/print/20_both_cable_covers.step
139.0 x 143.0 x 13.0 mm
