thereprocase/dell-5560-wall-mount/docs/models/minimalist/17-inch-example/03_left_fan_cage.stl

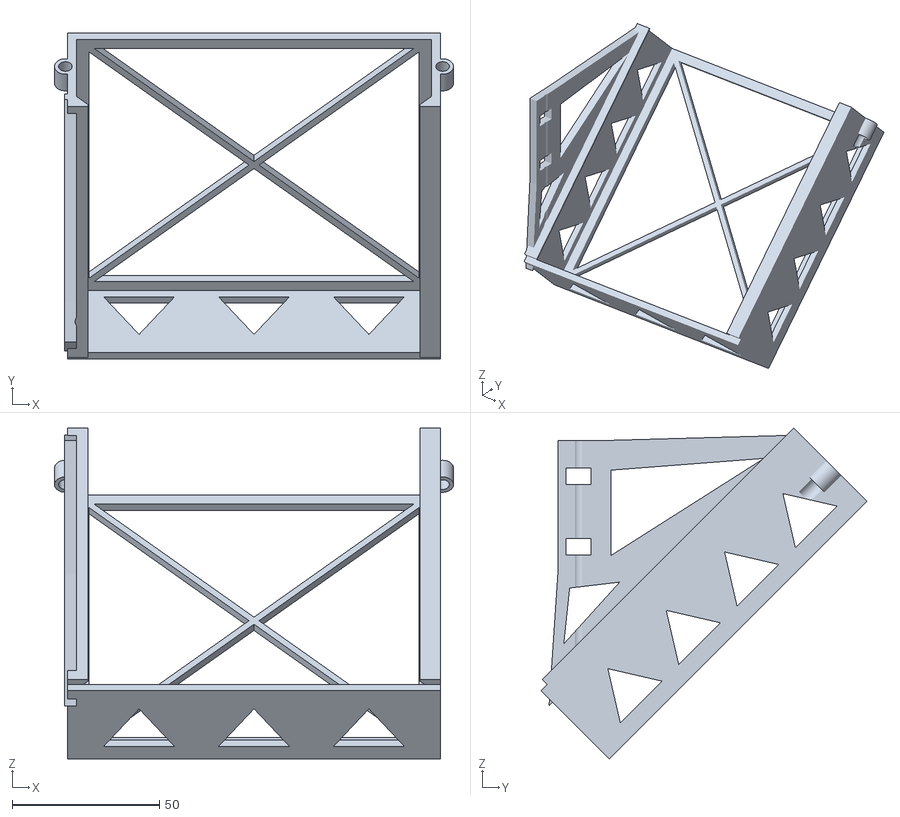
[picture p137: CAD file, 2026-10-06]
docs/models/minimalist/17-inch-example/03_left_fan_cage.stl
135.4 x 110.5 x 112.2
