thereprocase/dell-5560-wall-mount/fusion/cfd/geometry_gap8/assumed_side_seals.stl

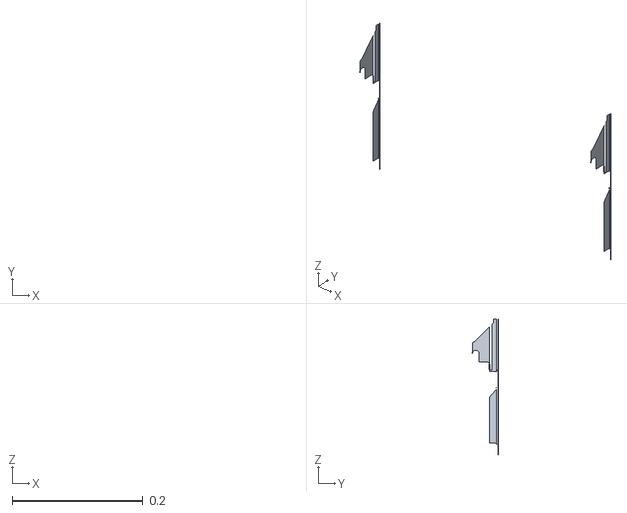
[picture p138: CAD file, 2026-10-06]
fusion/cfd/geometry_gap8/assumed_side_seals.stl
0.36 x 0.04 x 0.208
