thereprocase/dell-5560-wall-mount/fusion/cfd/geometry_installed/laptop.stl

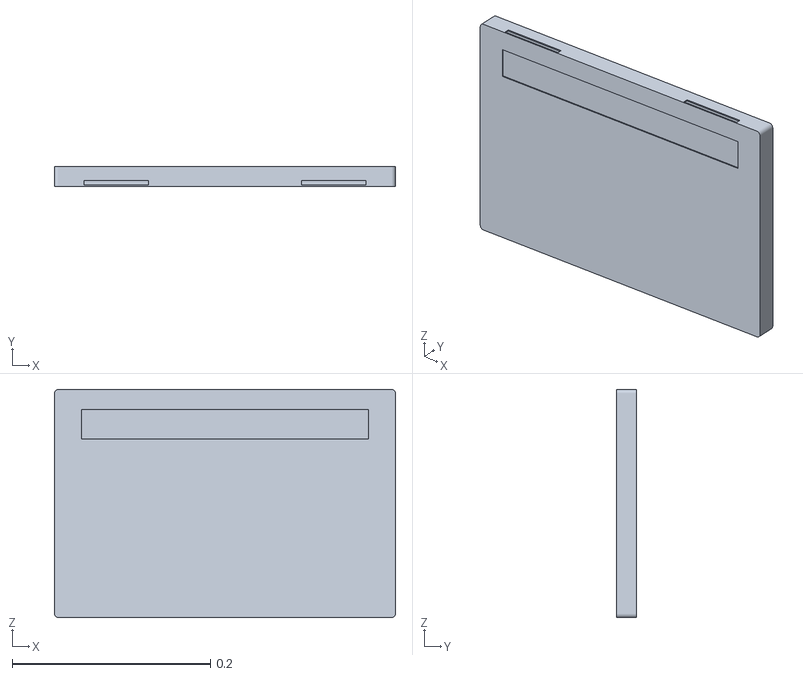
[picture p139: CAD file, 2026-10-06]
fusion/cfd/geometry_installed/laptop.stl
0.344 x 0.02 x 0.23
