thereprocase/dell-5560-wall-mount/fusion/cfd/geometry_traced_v1/noctua.stl

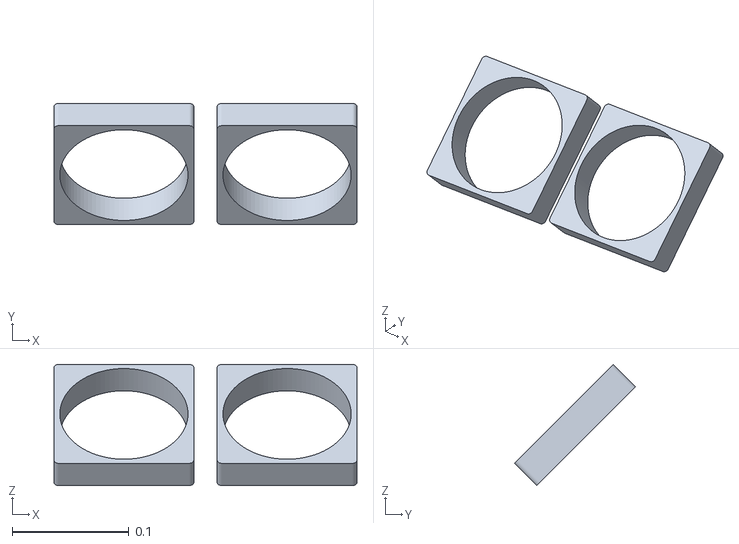
[picture p140: CAD file, 2026-10-06]
fusion/cfd/geometry_traced_v1/noctua.stl
0.26 x 0.104 x 0.104
