thereprocase/dell-5560-wall-mount/fusion/output/native/cfd_helpers_traced.step

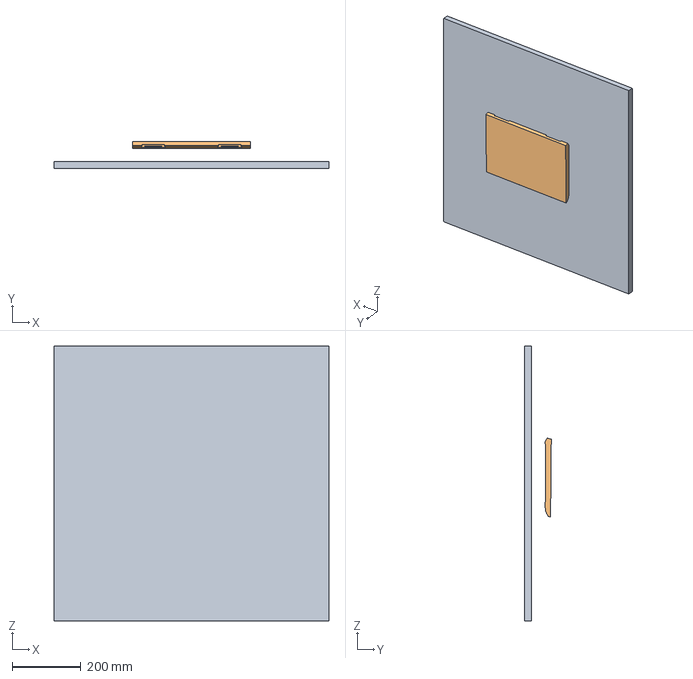
[picture p141: CAD file, 2026-10-06]
fusion/output/native/cfd_helpers_traced.step
800.0 x 77.4 x 800.0 mm
