thereprocase/dell-5560-wall-mount/minimalist/coupons/06_coupon_fan_cap.step

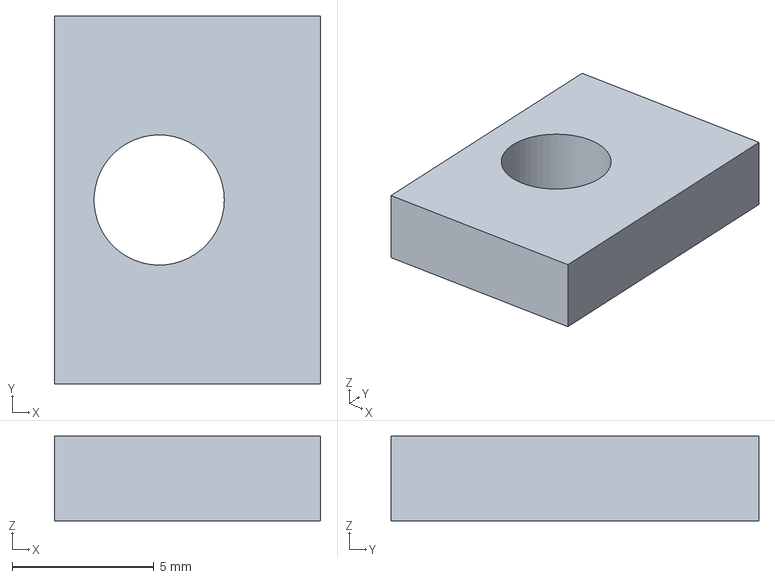
[picture p142: CAD file, 2026-10-06]
minimalist/coupons/06_coupon_fan_cap.step
9.40 x 13.0 x 3.00 mm
