thereprocase/dell-5560-wall-mount/minimalist/presets/13-inch-example/print/22_hardware_without_dam.step

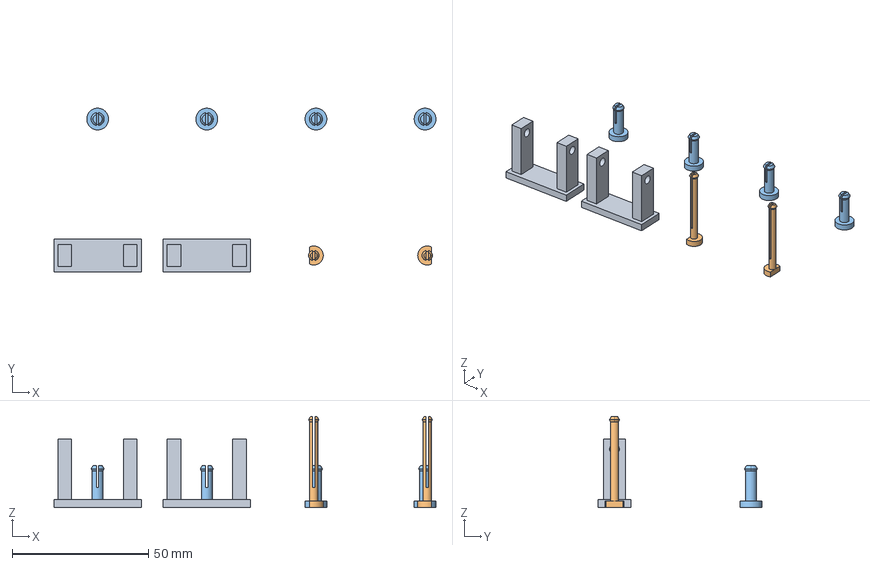
[picture p143: CAD file, 2026-10-06]
minimalist/presets/13-inch-example/print/22_hardware_without_dam.step
140.0 x 60.0 x 33.4 mm
