thereprocase/dell-5560-wall-mount/minimalist/presets/5560/print/21_all_hardware.step

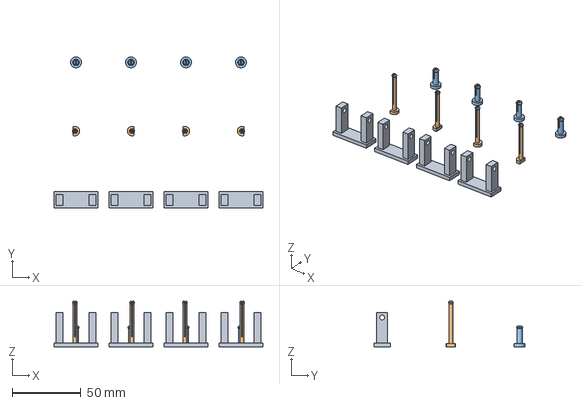
[picture p144: CAD file, 2026-10-06]
minimalist/presets/5560/print/21_all_hardware.step
152.0 x 110.0 x 33.4 mm
