thereprocase/dell-5560-wall-mount/fusion/cfd/cases/OpenCFD_v2412/installed_pressure10_v3/warm_start_metadata/README.md

The field values were copied from v2 iteration 300 into v3 time 0. The old uniform/time metadata was preserved here after the initial read warning. The solver log confirms v3 began at Time=1 and advanced from there. This is steady SIMPLE iteration numbering, not physical elapsed time. Future warm-start preparation should exclude uniform/time before launch.
