thereprocase/dell-5560-wall-mount/docs/assets/revh-duct-d4-D4-current-assembly.png

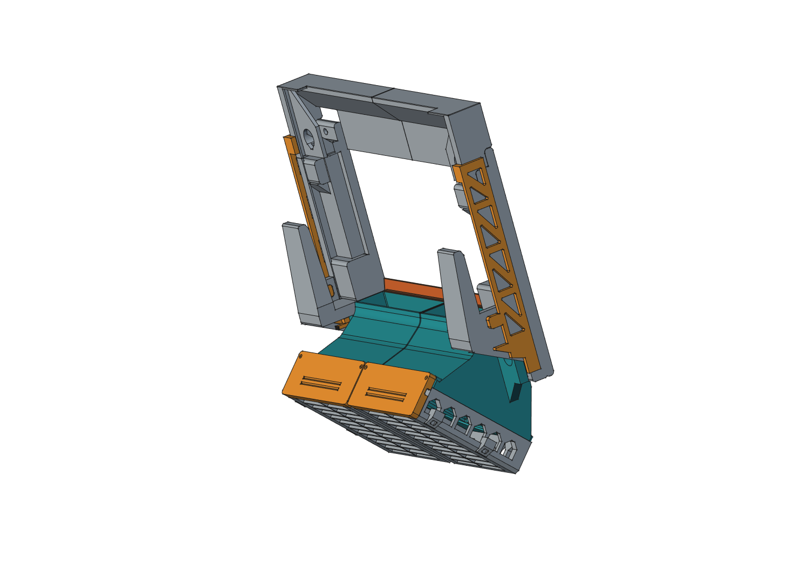
docs/assets/revh-duct-d4-D4-current-assembly.png
