thereprocase/dell-5560-wall-mount/freecad/assembly_preview.png

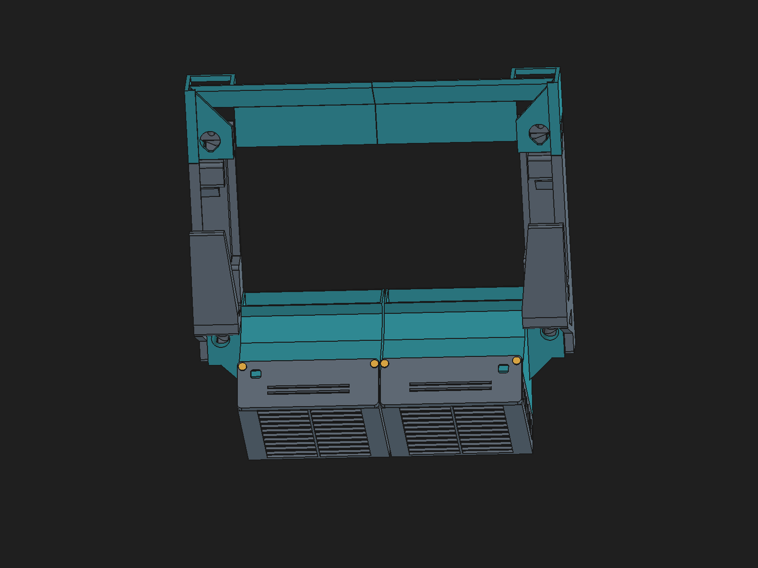
freecad/assembly_preview.png
