thereprocase/dell-5560-wall-mount/fusion/output/native/assembly.png

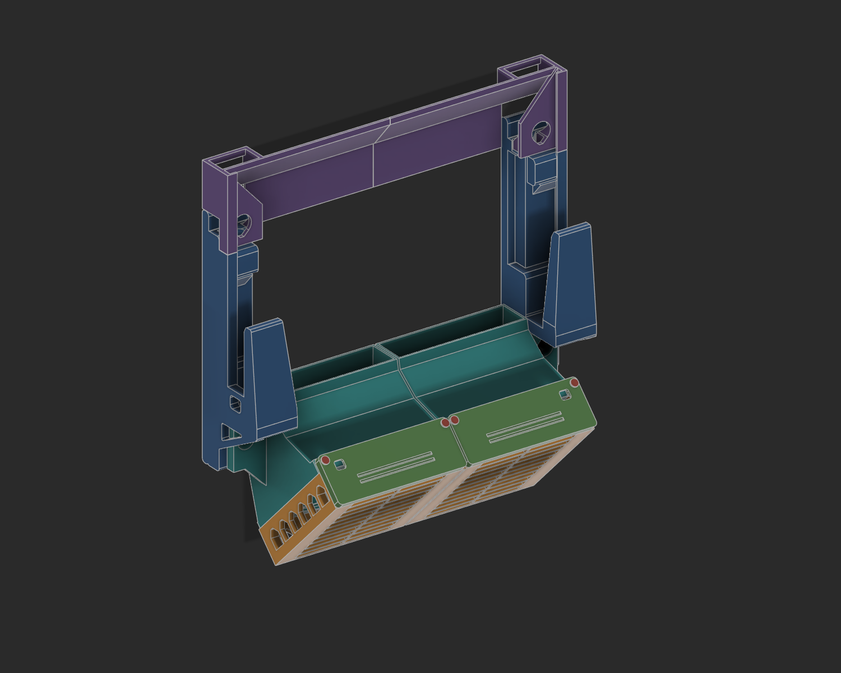
fusion/output/native/assembly.png
