thereprocase/dell-5560-wall-mount/makerworld/2026-09-08/ducted/ducted_02_open.jpg

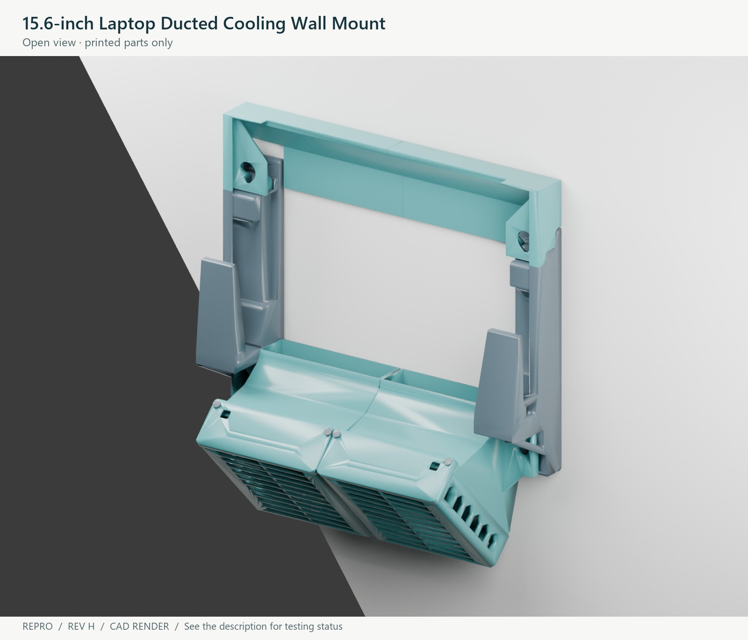
makerworld/2026-09-08/ducted/ducted_02_open.jpg
