thereprocase/dell-5560-wall-mount/makerworld/2026-09-08/ducted/ducted_03_side.jpg

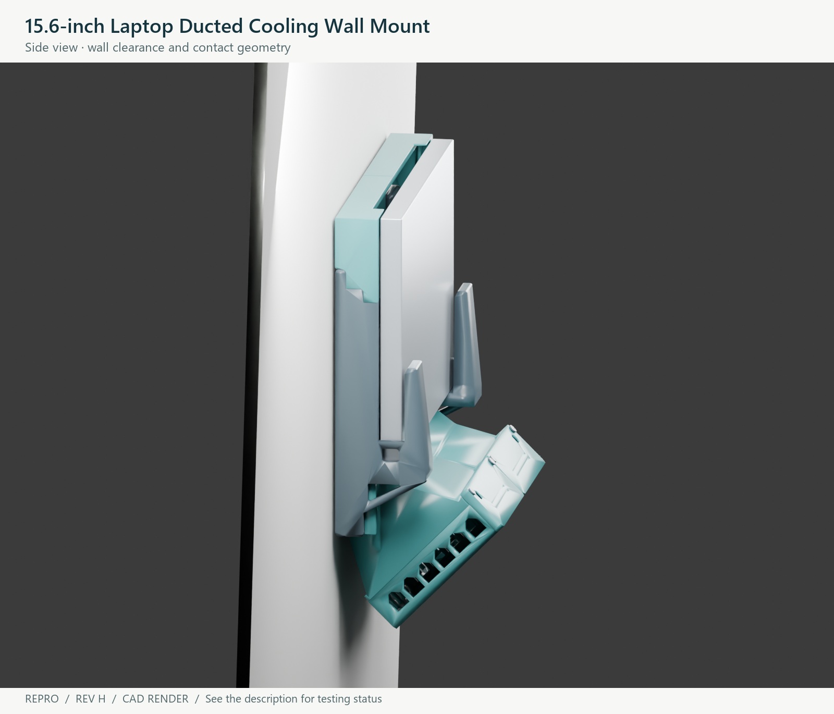
makerworld/2026-09-08/ducted/ducted_03_side.jpg
