thereprocase/dell-5560-wall-mount/makerworld/2026-09-08/ducted/ducted_05_geometry.jpg

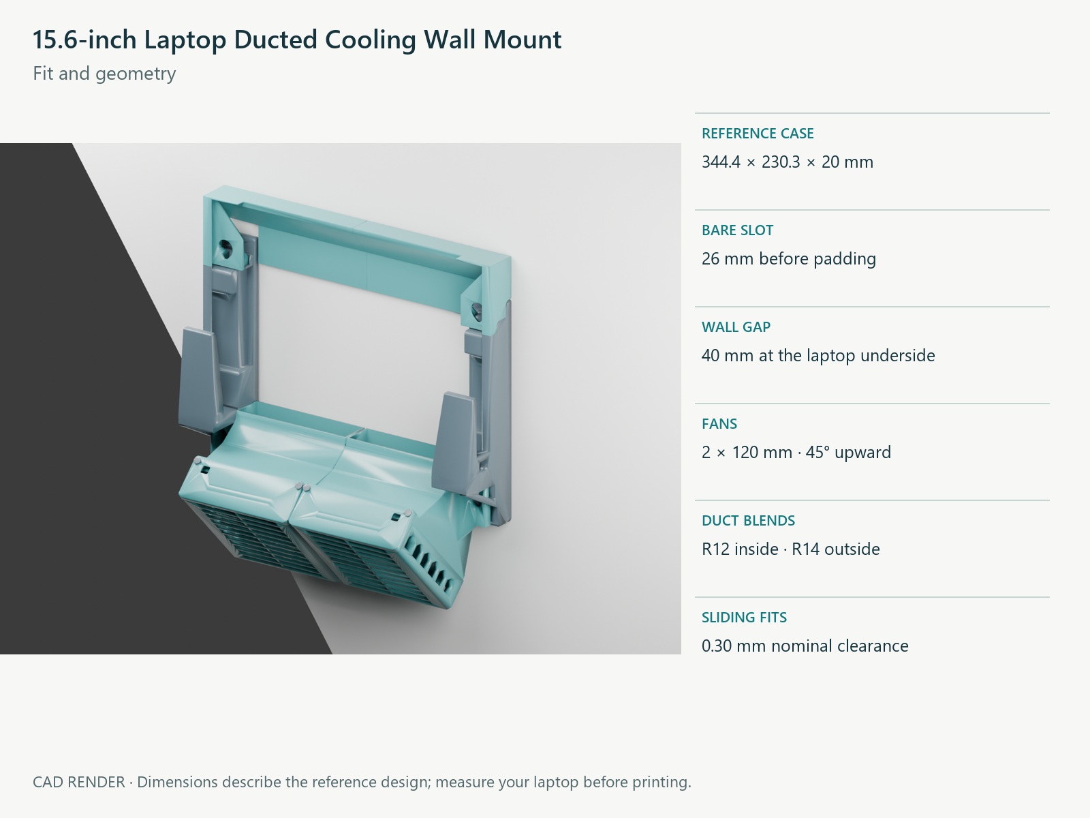
makerworld/2026-09-08/ducted/ducted_05_geometry.jpg
