thereprocase/dell-5560-wall-mount/makerworld/2026-09-08/fanless/fanless_04_detail.jpg

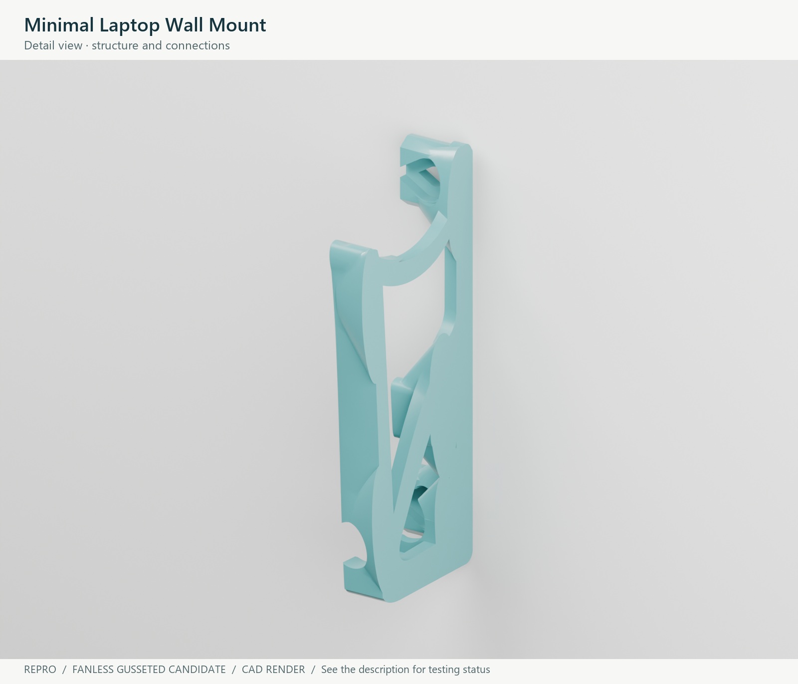
makerworld/2026-09-08/fanless/fanless_04_detail.jpg
