thereprocase/dell-5560-wall-mount/makerworld/2026-09-08/modular/modular_01_installed.jpg

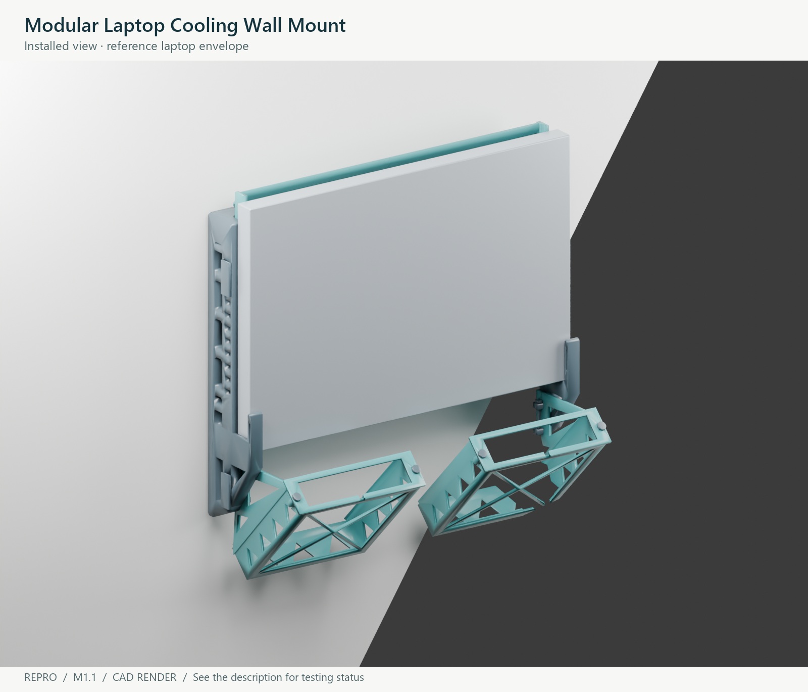
makerworld/2026-09-08/modular/modular_01_installed.jpg
