thereprocase/dell-5560-wall-mount/makerworld/2026-09-08/modular/modular_02_open.jpg

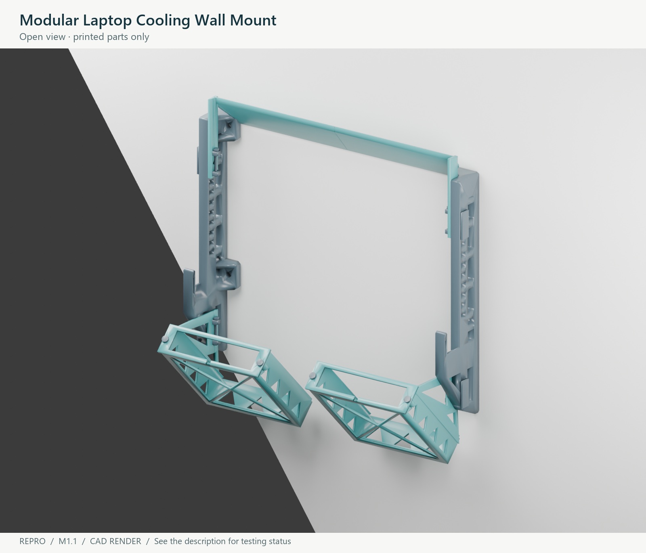
makerworld/2026-09-08/modular/modular_02_open.jpg
