thereprocase/dell-5560-wall-mount/fusion/cfd/cases/OpenCFD_v2412/installed_pressure10_v3/results/iteration_400/airflow_streamlines.png

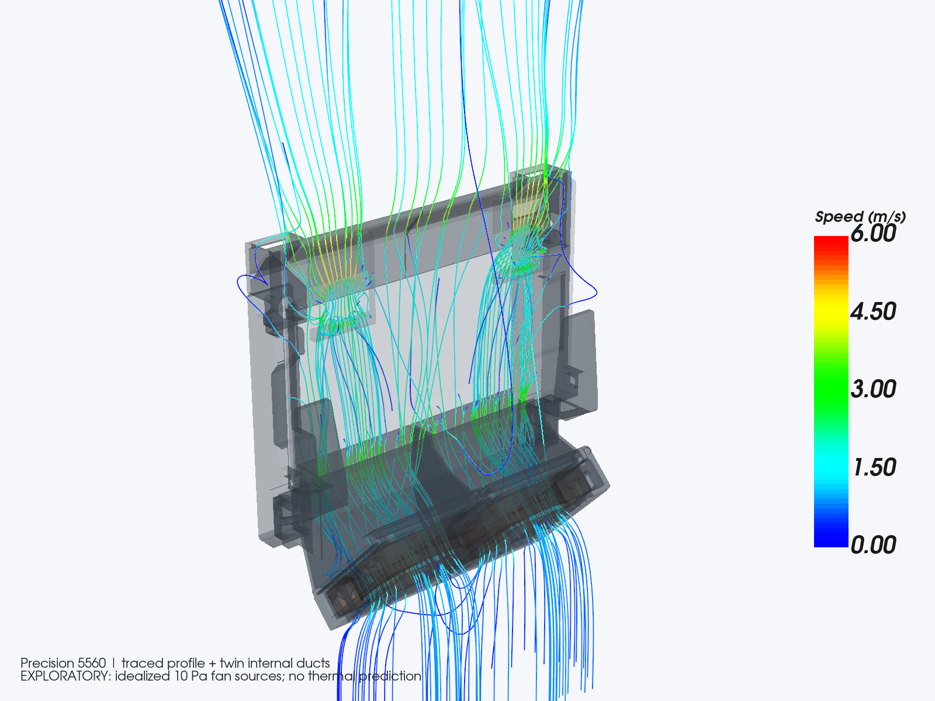
fusion/cfd/cases/OpenCFD_v2412/installed_pressure10_v3/results/iteration_400/airflow_streamlines.png
