thereprocase/dell-5560-wall-mount/revh_retention/reports/01_right_arm_fit_test-toolpath.png

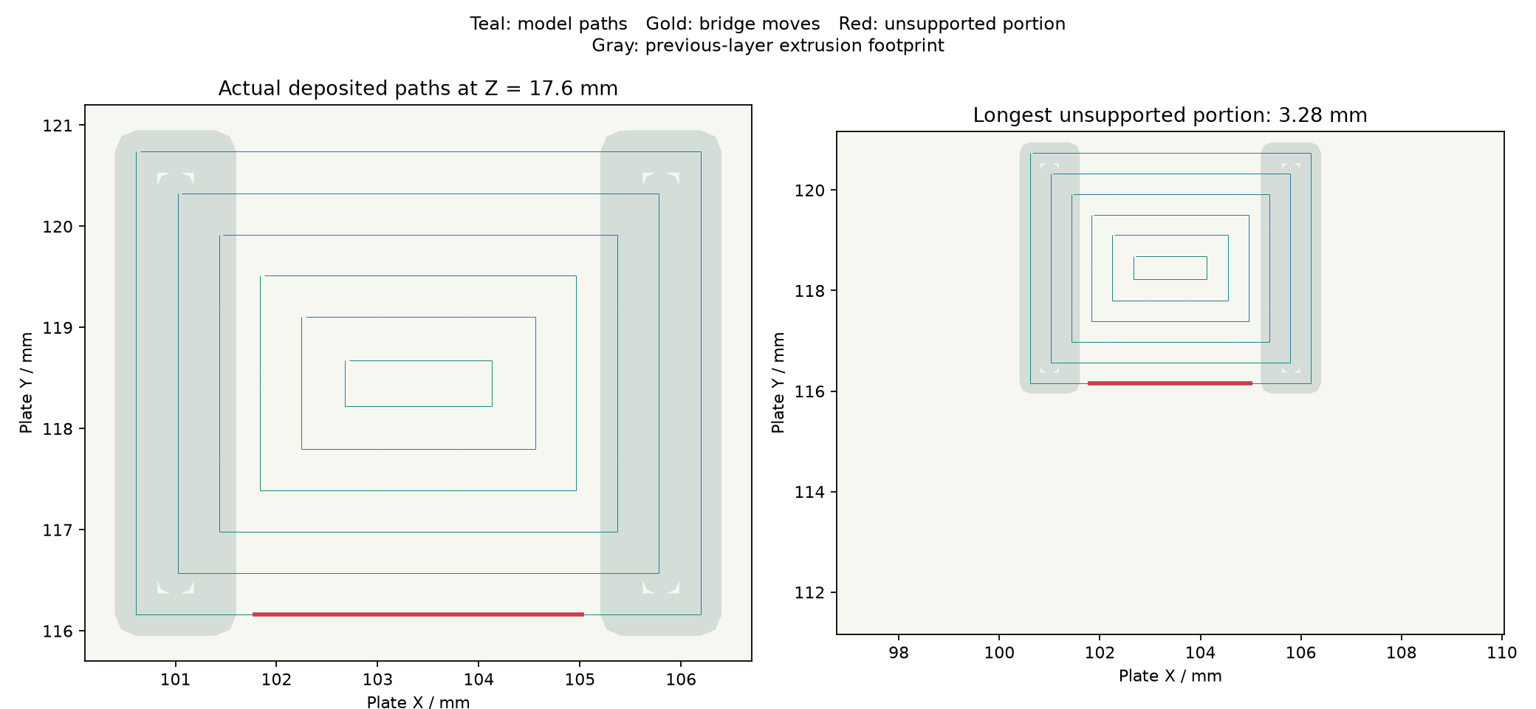
revh_retention/reports/01_right_arm_fit_test-toolpath.png
