thereprocase/dell-5560-wall-mount/docs/simulation/revh-transient/pilot-pressure-history.png

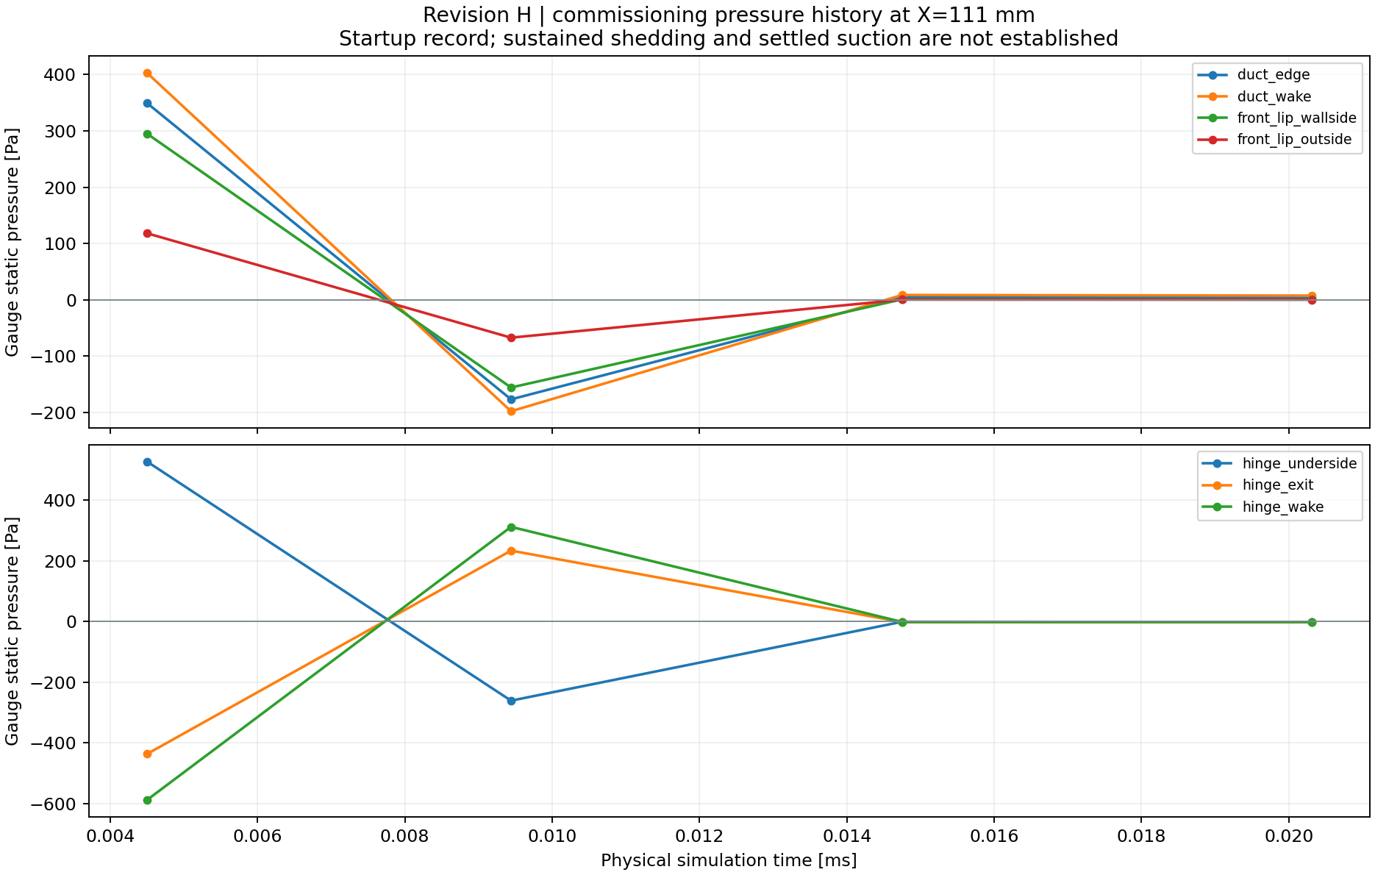
docs/simulation/revh-transient/pilot-pressure-history.png
