thereprocase/dell-5560-wall-mount/docs/simulation/revh-transient/sequence/checkpoint-02/history.png

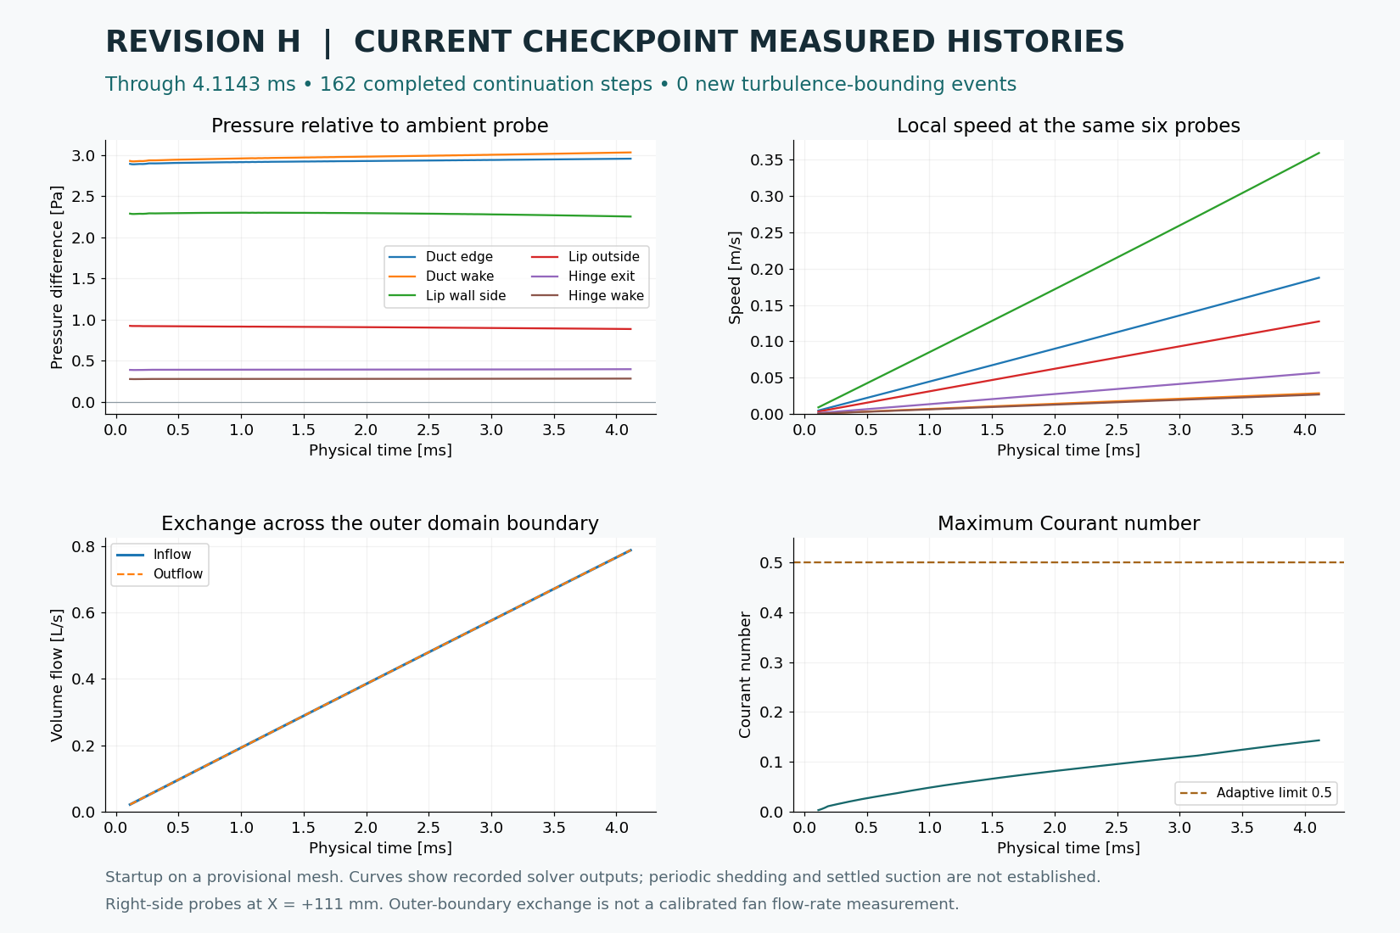
docs/simulation/revh-transient/sequence/checkpoint-02/history.png
