thereprocase/dell-5560-wall-mount/docs/simulation/revh-transient/sequence/final/startup/history.png

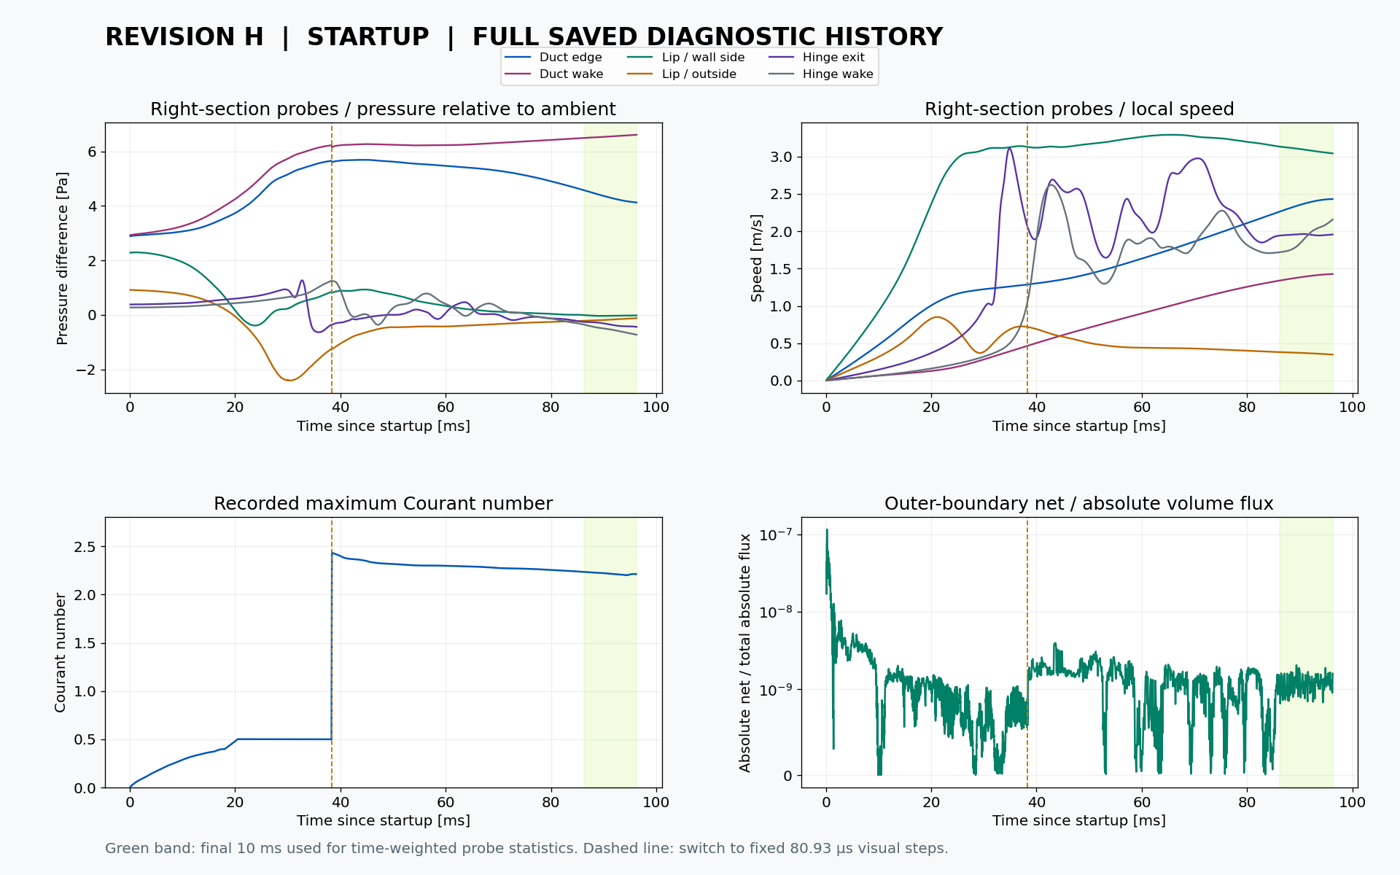
docs/simulation/revh-transient/sequence/final/startup/history.png
