thereprocase/dell-5560-wall-mount/docs/simulation/revh-transient/sequence/flowing/checkpoint-04/history.png

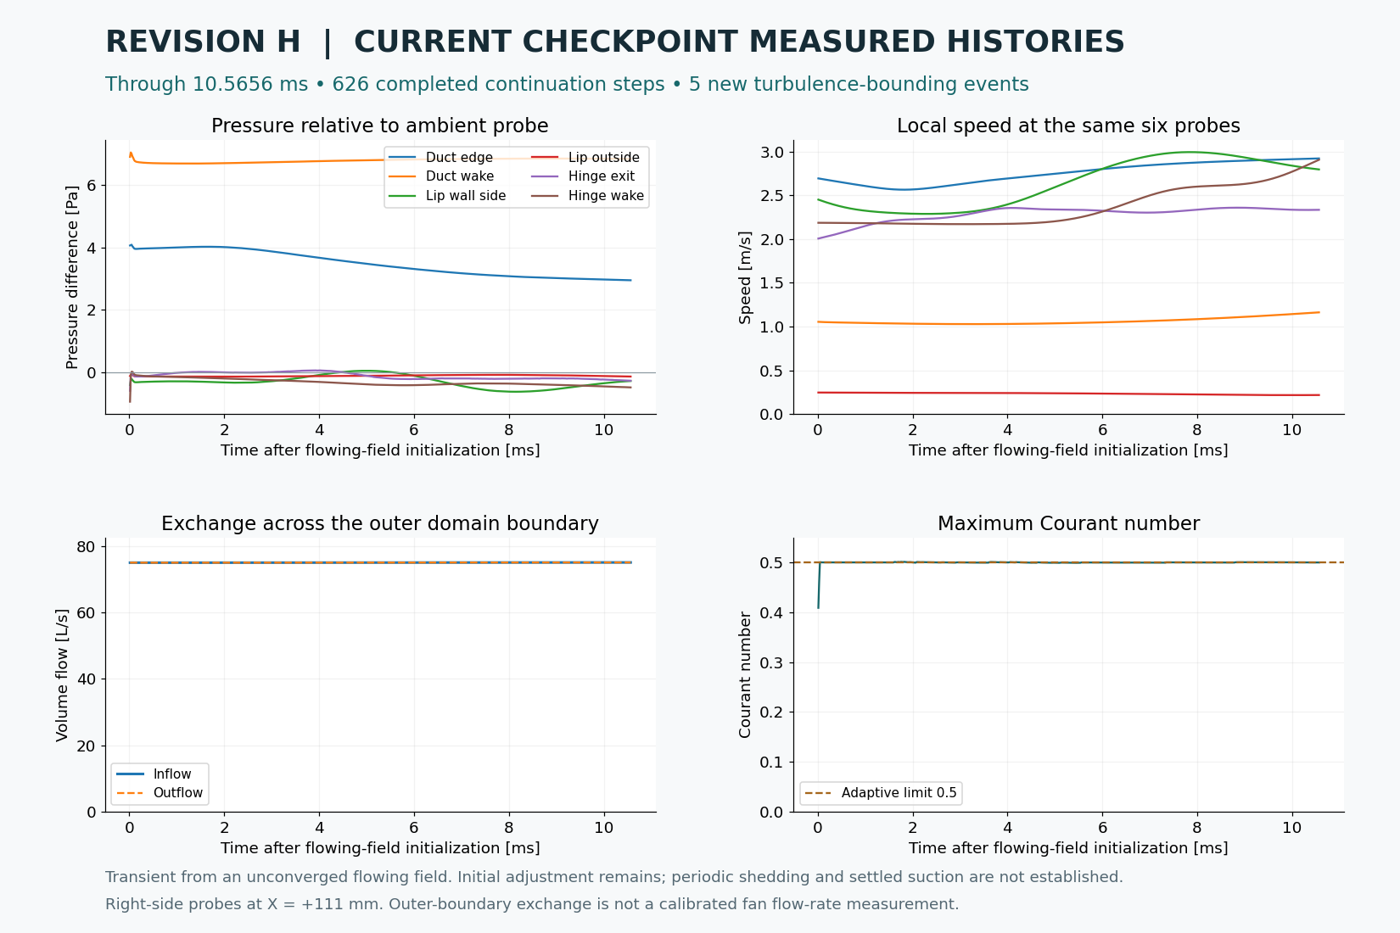
docs/simulation/revh-transient/sequence/flowing/checkpoint-04/history.png
