thereprocase/dell-5560-wall-mount/docs/simulation/revh-transient/sequence/hour-1/history.png

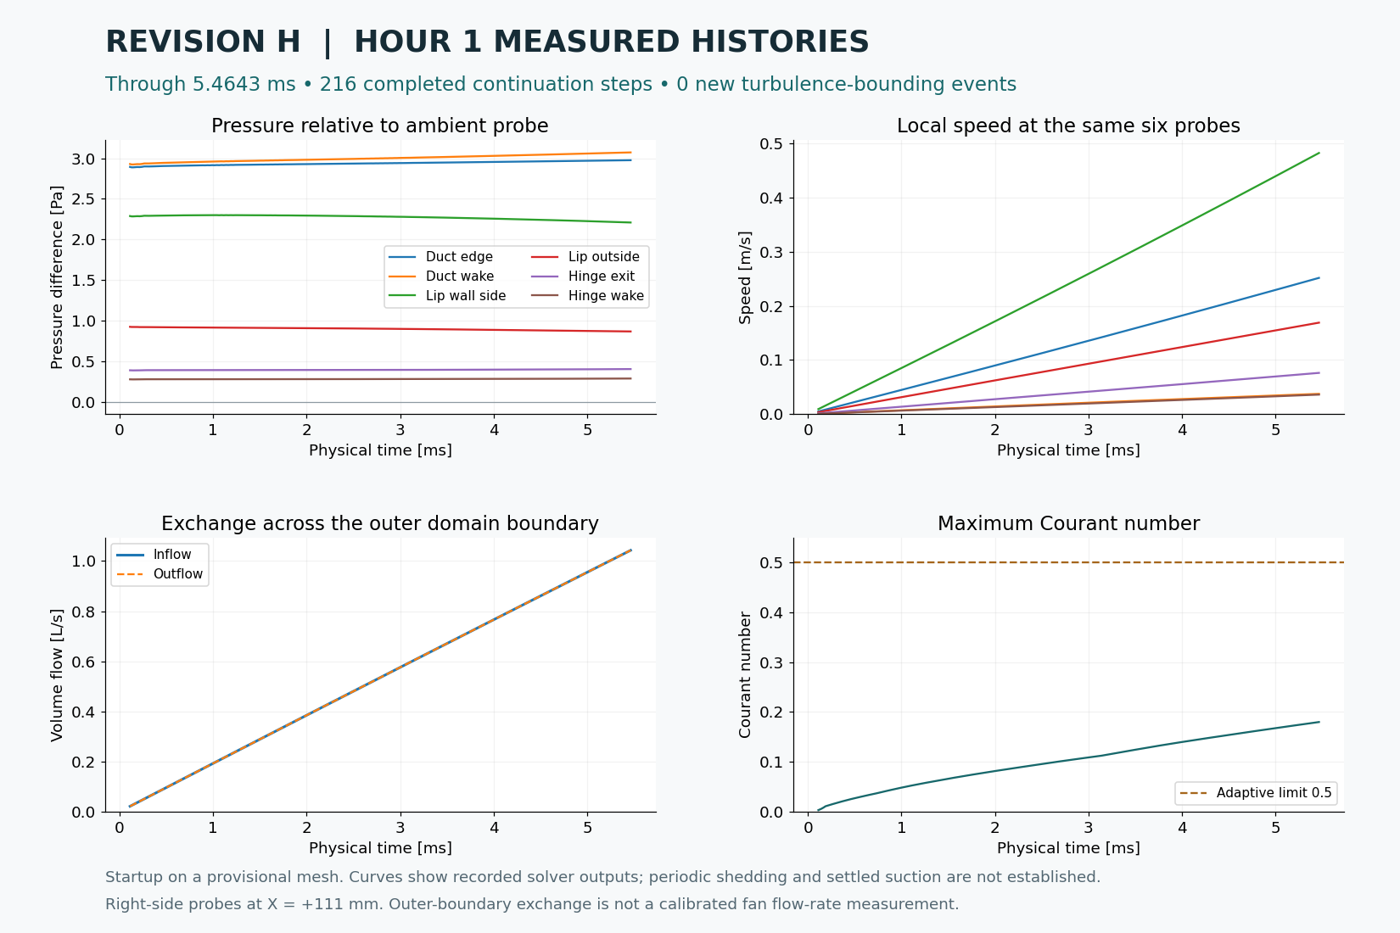
docs/simulation/revh-transient/sequence/hour-1/history.png
