thereprocase/dell-5560-wall-mount/docs/simulation/revh-transient/sequence/hour-18/history.png

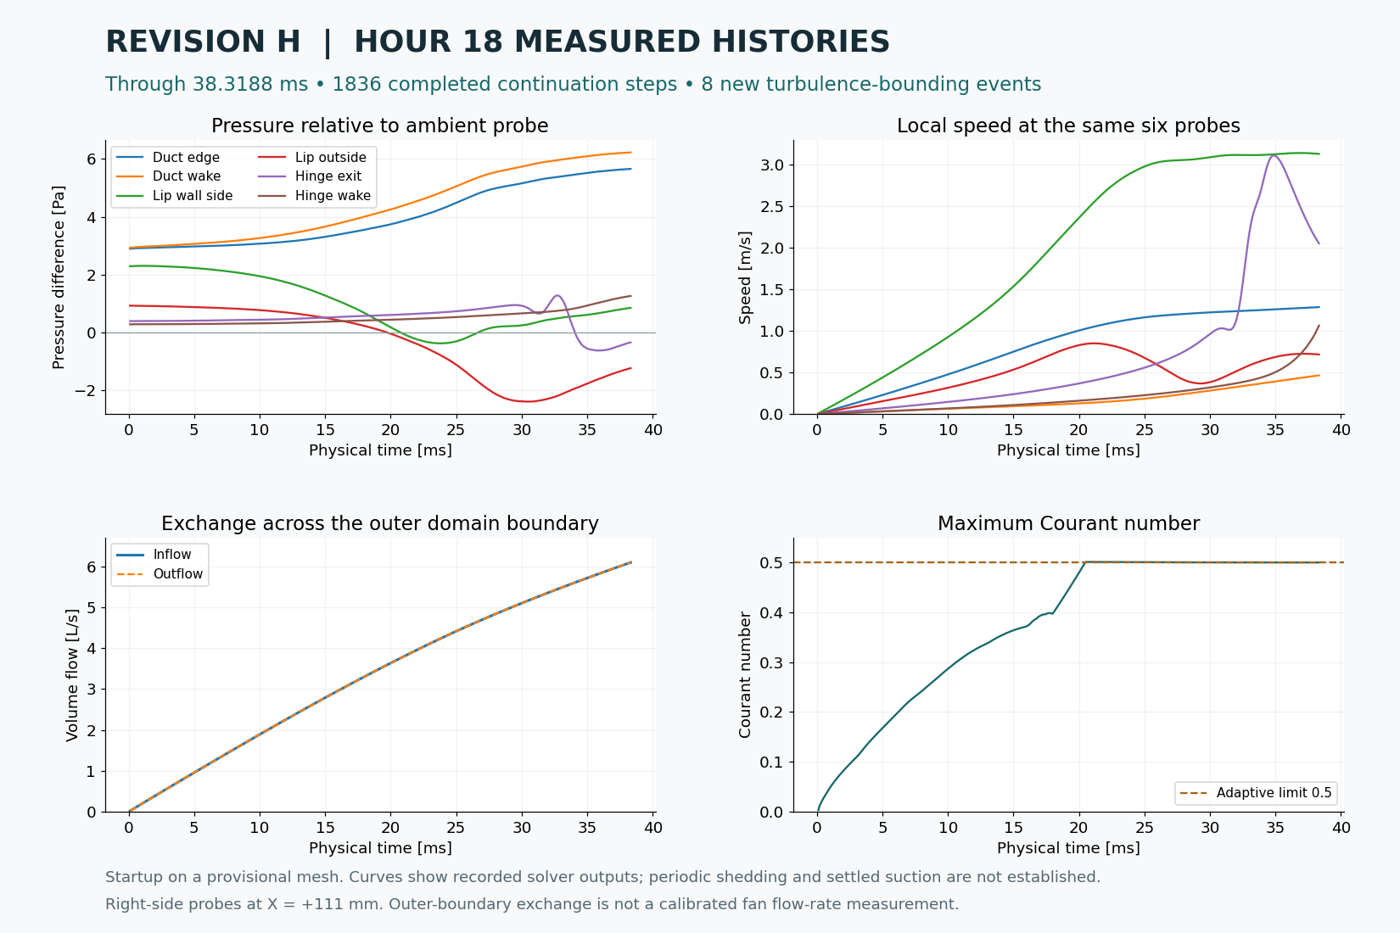
docs/simulation/revh-transient/sequence/hour-18/history.png
