thereprocase/dell-5560-wall-mount/docs/simulation/revh-transient/sequence/steady/history-final.png

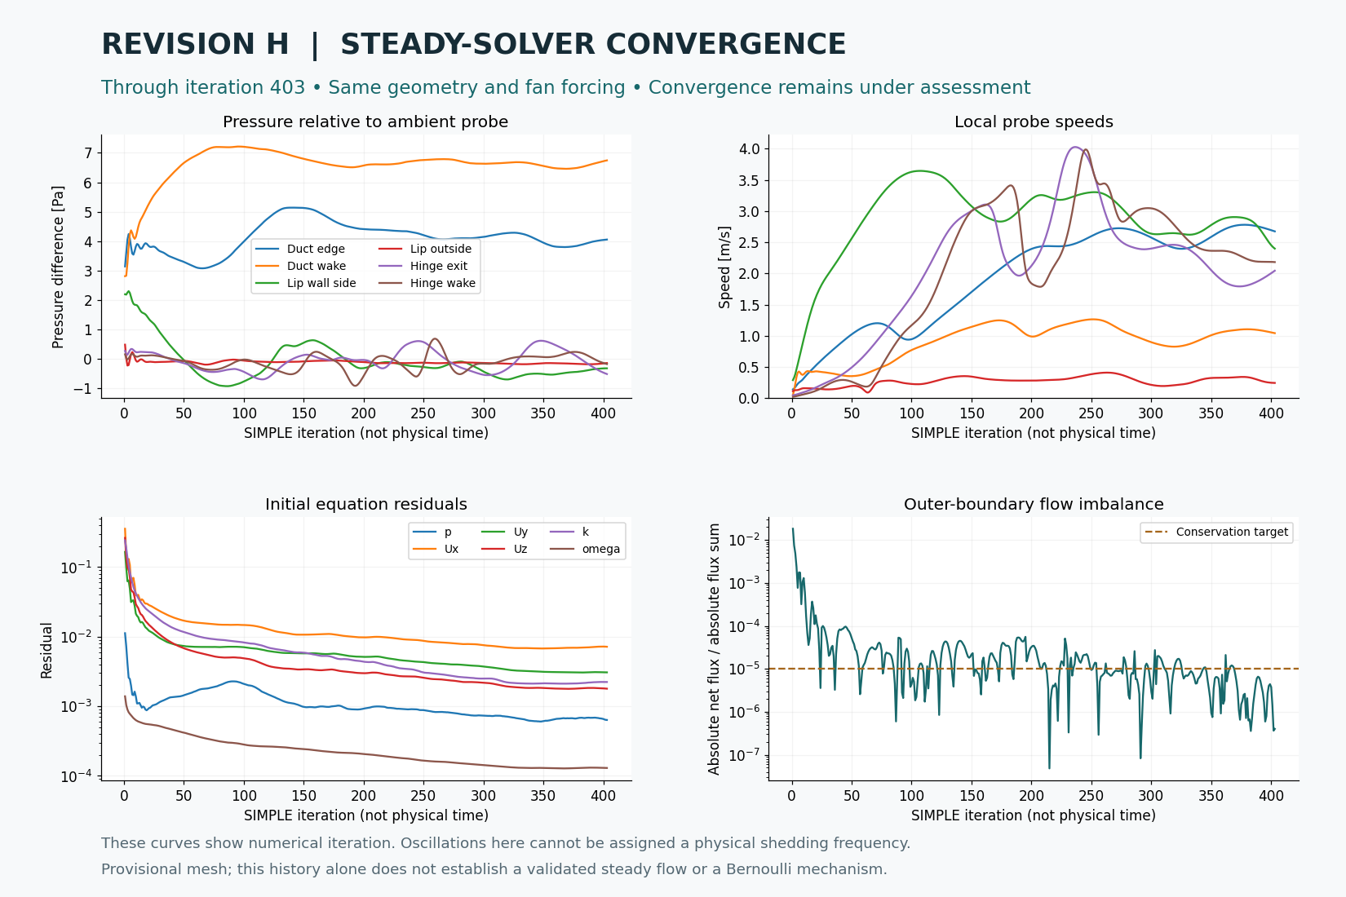
docs/simulation/revh-transient/sequence/steady/history-final.png
